markshuttle/dogfence-pcb/ACCEPTANCE.md

# Prototype and Field Acceptance

**Draft revision: 1.2.1-dev. Test requirements, not test results or release approval.**

This protocol separates basic acceptance of **five fully assembled prototypes** from qualification of the **41-station, 0-4000 m installation with 82 APEM indicators**. There are 40 spans, five earth-connected stations and 36 standard stations. Five basic bench passes do not authorize a perimeter production order, prove a board surge rating, or release the fence for animal containment.

[Agreed requirements](REMEDIATION.md#agreed-requirements) and [release gates](REMEDIATION.md#release-gates) control this protocol. Test the [reviewed prototype population](pcb/ASSEMBLY.md#reviewed-components) against the [BOM](pcb/BOM.csv). **C4, C5, W3, W1 and W4 remain open** for transient response, powered recovery, continuous thermal behavior and supplier process/fit acceptance; the [issue register](REMEDIATION.md#issue-register) owns their disposition.

Use [INSTALL.md](INSTALL.md) for isolation, wiring and operation, [RISKS.md](RISKS.md) for fault/environmental limitations and [ELECTRICAL](pcb/ELECTRICAL.md) for the circuit evidence. All steps below require recorded evidence; an unperformed or inconclusive test is **NOT RUN / HELD**, not PASS.

Purchases and allocation, including [resistor procurement/history](MATERIALS.md#resistor-procurement-and-history), belong to [MATERIALS](MATERIALS.md); manufacturer sources and unresolved product/process discrepancies belong to [ENVIRONMENT_EVIDENCE](pcb/ENVIRONMENT_EVIDENCE.md).

## Release Boundaries

| Gate | Evidence needed before release | Status in this draft |
| :--- | :--- | :--- |
| **P: File-verified prototype artifacts** | Strict file/artifact and sourcing checks; matching `status=prototype`, `mode=prototype` manifest and hashes; all five ledger holds explicitly deferred, not closed. | **Authorized artifact scope only.** Require current source-matched results in REMEDIATION; this protocol implies no fresh publication or upload/order authorization. Supplier CAM/placement/allocated parts are still required before an actual order. |
| **A: Production file ready** | Original engineering/file-release review: correct hub/circuit design; consistent source, libraries, rules and revision; passing checks; reviewed data and synchronized documentation. | **Held by unresolved protection, continuous-duty and part/land-pattern acceptance**, even when automated file checks pass. Not closed by P. See `pcb/verification.json`. |
| **B: Original prototype-order gate** | Original Gate A plus exact part/fit, placement, GDT forming, solder/via process and CAM acceptance, and an approved, safely bounded test programme. Known manufacturing defects cannot be deferred silently. | **Held wherever supplier/process evidence or controlled scope is missing.** Prototype-dependent tests may be explicitly deferred, not passed; P alone does not close B or authorize an order. |
| **C: Field release** | Required normal, selected negative-voltage protection, duty/thermal, visibility, full-hub, RF/site, fault/surge and material evidence; accepted earthing and maintained cattle-fence prohibition; documented performance limits. | **Held pending genuine qualification.** Excluded installation-polarity immunity is not a test PASS. |

The live checklist, not this table, records subsequent evidence-backed closures. **P is separate from the original A/B/C production/field holds.** Switch/environmental qualification and enclosure dry-fit on received boards are not prerequisites to prototype-file generation. Board-specific MPN/fit, GDT forming, panel/process, supplier CAM/placement and allocation remain order tasks; whole-BOM `allocation_verified` remains `false`. `1.2.1-dev` identifies a draft target; record actual board markings and hashes rather than relabelling older hardware as tested.

**TE prototype results do not qualify Yageo production.** Before production release, separately review the Yageo part's manufacturer/rating, land-pattern, thermal, pulse and process evidence, update the controlled BOM/CAD, libraries, models and notes, and reverify under the [population/substitution controls](pcb/ASSEMBLY.md#reviewed-components). Define the production configuration's required qualification and retained evidence explicitly; an order does not implement or approve a BOM variant.

## Preconditions

Apply these to the corresponding **hardware test**, not Gate P artifact generation. Switch/field approval is needed for hub/site tests and OneGel acceptance for potting, not for unpowered incoming-board inspection. An isolated board bench test still needs its own approved electrical bounds and stop limits.

1. Freeze the intended test configuration, including the revisions of this protocol and its referenced limits/tables. Record board serial numbers, source revision, schematic/BOM, as-built deviations, native placement/assembly drawing, fabrication manifest and report hashes. The population comes from the final BOM, not the legacy component count. **1.2.1-dev is retained for the approved 2 mm east board extension and H2/H4 moves after the westward GDT/via relocation.** Keep the pre-extension `1.2.1-dev` and earlier axial-AC / SMT AC/rear-B `1.2.0-dev` snapshots' hashes and sample histories separate, without transferring test results to the new outline/mount configuration. Approve substitutions and rework explicitly; no field soldering is part of the installation plan.
2. Have the electrical reviewer supply **numerical acceptance bands before testing**: source minimum/nominal/maximum including accessible adjustment, tolerance and overshoot; verified cable resistance/temperature range; per-channel current and branch loading; LED forward/reverse limits; power/temperature derating and stop limits; protection trip/recovery behavior; and the intended surge/insulation test envelope. Missing bounds hold the corresponding test. Do not choose limits after seeing the result.
3. Use **one MEAN WELL LRS-75-36 (36 V / 2.1 A / 75.6 W) for TEST; keep the second disconnected as a spare**. Verify receipt/nameplates and the TEST unit's qualified setting; no parallel, series, separate-channel or opposite-end feeding. Qualify the actual supply's hiccup/retry behavior with the actual **Littelfuse 0217002.MXP (2 A, 217 series)** and **Phoenix Contact UK 5-HESILED 60 / 3004139** holder and any revised source protection. Published DC interrupting capability is not clearing coordination.
4. Confirm the exact six-end switch program and source-side wiring. **Kraus & Naimer CA10.A364** is provisional; current **WAA364 (formerly A364) is eight-pole, 1-0-2 centre-off, 60-degree switching, not six-pole**. The six-end matrix is unchanged; **two extra poles remain unassigned**. The [catalogue contact/link schedule](pcb/ENVIRONMENT_EVIDENCE.md#catalogue-contact-schedule) is verified static source evidence, not the supplied-switch pinout. Obtain manufacturer approval of the exact offered contact development, DC breaking suitability and **global break-before-make** sequence across the entire used program, in both directions. A 20 A thermal rating or a static continuity test cannot supply this evidence. Assign physical terminal numbers only in the subsequently accepted hardware drawing.
5. Establish an authorized test area, independent animal containment, emergency shutdown, personnel responsibility and safe source isolation. OFF/TEST disable the RF fence. Follow [INSTALL.md](INSTALL.md#safety-first): isolate transmitter/PSU/backups, discharge and verify de-energization before handling terminals, then disconnect all six field ends. Inspect the **entire 4 km boundary cable, stations and hub** against the [energized-cattle-fence prohibition](INSTALL.md#cattle-fence-prohibition); record compliance and any required reassessment. If the hazard is found, stop work/use, arrange safe isolation and reassess before proceeding. Do not work during storms. Mains/PE and any surge testing require the relevant qualified personnel.
6. Obtain the supplied-revision APEM, COMBI 308 PP/TPE, Essentra, confirmed AMC cable and WISKA OneGel documents and define the material/fit process after manufacturer-conflict clarification. Do not pot the reference sample. Do not deliberately reverse LED flying leads to prove the excluded immunity requirement, or surge-test an assembly as an ordinary bench check; abnormal-voltage work requires a controlled test plan.

The [declared source-envelope study](pcb/DESIGN_BOUNDS.md#evidence-and-inputs) and [electrical load cases](pcb/ELECTRICAL.md#2-calculated-results) are analysis inputs, **not pre-approved test bands or enforced hardware limits**. Establish actual adjustment, tolerance, ripple/startup and hub/interface losses; PSU OVP is not a precision operating limiter. The historical restricted-voltage proposal was never enforced. Qualifying the actual normal source range is an alternative to requiring an active cutoff.

## Sample Allocation

All five units receive the workmanship, cold-circuit and normal-function checks below. The allocation is **proposed scope, not accomplished coverage**; record changes and sample history before each qualification test.

| Unit | Proposed additional use | Restriction |
| :--- | :--- | :--- |
| Board 1 | **Unpotted reference** with approved parts, measurements and photographs. | Retain unpotted; no intentional fault, reversal-stress, environmental or destructive surge programme. |
| Board 2 | Instrumented selected negative-voltage protection and unpotted electrical characterization; support nondestructive hub testing. | No required reversed-flying-lead survival test after the user's installation-risk acceptance. Approve the actual clamp/exposure test scope first and record stress/degradation before reuse. |
| Board 3 | Complete enclosure dry-fit/process qualification, then potted **0 m/source-end** continuous-duty thermal testing. | Fit actual WAGOs, cables, glands, earth conductors and lid indicators; instrument before filling. |
| Board 4 | Complete enclosure dry-fit/process qualification, then potted **4000 m/far-end** duty, visibility and environmental/site work. | Include reduced-voltage conditions and real viewing angles; reuse only if prior tests leave the unit suitable. |
| Board 5 | Full-hub/RF work and controlled source-fault/protection development; potentially destructive tests only when approved. | One unit cannot establish every surge, fault and environmental corner. Record stress order and preserve evidence. |

Five boards are not a 41-station fixture and do not provide independent replicates for every test. Review the required fault/surge polarities, levels, repetitions and destructive sample count with the test laboratory. **Request approval for more boards, indicators and fixture materials when the scope needs them**, rather than sacrificing the reference or inventing five-board coverage. Required deployment quantities and historic purchases remain distinct in [MATERIALS.md](MATERIALS.md).

## Instruments and Evidence

Use calibrated instruments suited to the circuit, location and energy involved. The following are acquisition requirements for the low-voltage programme, not claims about an available meter. Tighten them where the final design's margin requires it; record instrument model/serial, calibration, range, resolution, accuracy specification, offsets and probe loading.

| Measurement | Required capability / method |
| :--- | :--- |
| Steady DC voltage | At least a **0-60 V DC** measurement range covering the verified supply maximum, with appropriate overload/transient and common-mode ratings. Target expanded uncertainty no worse than **0.5% of reading + 0.05 V** for source/rail readings. Resolve the actual LED terminal voltage with **0.05 V or better uncertainty**, or tighter if needed for the 5 V limit. |
| Normal current | Suitable ranges for roughly **0-50 mA per indicator** and **0-3 A source current**, enlarged if the approved source can exceed these ranges. Target uncertainty **1% of reading or better** at each operating point, including offsets and shunt tolerance. Use calibrated low-burden shunts or properly fused current inputs; connect in series while unpowered, never place a current input across a supply. Fault/pulse ranges need separate sizing. |
| Resistance | Low-ohm/Kelvin measurement for PCB bonds, typically **0-1 ohm with at most 0.02 ohm uncertainty**; **0-100 ohms with at most 0.2 ohm uncertainty** for a core baseline; and a suitable resistor range with **0.25% or better uncertainty** for a 1% resistor. Lead/contact compensation is required. A beeper is a connectivity screen, not a precision bond measurement. |
| Leakage / high resistance | Record the meter's actual range, test voltage, input impedance and detection limit. Use a suitably sensitive guarded measurement if a sub-microampere bound is required. **A 0.00 mA display is not proof of zero or sub-microampere leakage**, and `OL` means beyond that instrument's range under those conditions, not infinity. |
| Temperature | Calibrated attached thermocouples/RTDs and an electrically suitable logger, covering at least **-20 to +125 degrees C**, with **2 degrees C or better uncertainty** including attachment effects; tighten for small margins. Measure ambient, internal gel/air and critical parts. Use appropriately isolated sensors. Do not infer part temperature by touching it; uncorrected IR readings on shiny parts are not sufficient. |
| Waveforms / timing | Appropriately rated **differential or isolated** voltage and current acquisition. Select probe bandwidth and sampling to resolve the fastest relevant edge, with at least ten samples across it and a justified probe rise-time/loading budget. Capture peaks, switching transitions, RF, start-up and full PSU hiccup/retry cycles, not just a DMM average. Record trigger, bandwidth, sample rate, time span, clipping checks and raw data. |
| Mechanical / optical | Calipers/gauges adequate for drawing tolerances, a calibrated low-range torque tool for the LED nut, and a measured **5 m** viewing distance. Record actual daylight illuminance, weather, background, sun direction, lens orientation and observer angles; use a light meter with documented range/accuracy suitable for full sun. Photographs alone do not establish ON/OFF visibility. |

These low-voltage ranges **do not authorize high-voltage field or surge measurements**. The qualified lab must select probes, isolation, differential/common-mode voltage, impulse energy and measurement-category ratings for the actual test. Never lift a scope's protective earth or improvise with a grounded scope clip on a floating field core. A mains isolation transformer is not a substitute for rated differential measurement. Keep required source chassis PE intact. Probe resistance/capacitance can alter LED reverse-voltage sharing; include that loading in the method and uncertainty.

Document an expanded uncertainty `U` with its confidence/coverage factor and the complete measurement chain. Apply guard bands: for an upper limit require `measured maximum + U <= limit`; for a lower limit require `measured minimum - U >= limit`. Include component/environmental corner allowances from the analysis separately. Resolution is not accuracy. If uncertainty or uncaptured transients could conceal a violation, mark **HELD**, not PASS.

## All-Five Workmanship

**Incoming fit evidence precedes assembly.** [ASSEMBLY's adopted hole/pin limits](pcb/ASSEMBLY.md#hole-fit-evidence) and [DFM evidence](pcb/DFM_EVIDENCE.md#independent-acceptance) distinguish published maxima from controlled **E procurement envelopes** and historical parts. Independently inspect **every allocated controlled-envelope part, including attrition**, with uncertainty. Verify the separate **0.050 mm radial per-pin pattern limit after common rigid alignment through the insertion length**; together with **+/-0.05 mm hole position on each axis**, it allocates **0.241421 mm diametrally in addition to the 0.10 mm assembly allowance** for retained Kefa/earth-GDT holes. R1/R2, D1-D4 and all three inter-core GDTs are SMT, with no insertion holes or axial resistor/AC forming/standoff. No allocated lot, earth-GDT forming process or insertion yield is approved by these calculations.

Perform and record these checks on **each** unpowered prototype before stress testing:

1. Match markings, references, MPNs, values, population and orientation to the accepted [BOM](pcb/BOM.csv) and [reviewed components/drawing](pcb/ASSEMBLY.md#reviewed-components). The design specifies **16 electrical parts, nine SMT and seven THT**, plus four mounting footprints. Verify both prototype R1/R2 are the selected TE part and all three inter-core GDTs, including GDT_AC, are the selected Ruilon SMT part, not production or retired-part substitutions. Require incoming-lot and PCBA-job allocation evidence, not just a matching sourcing code. No assumed approval of alternative indicators or historical active candidates.
2. Verify the **65 x 56 mm** outline and agreed fabrication tolerances, clean depanelized edges, and four **3.2 mm NPTH** mounting holes at the [controlled positions and mechanical clearances](pcb/ASSEMBLY.md#physical-guardrails). Rails/tooling removal follows the accepted manufacturer's plan; do not assume automatic removal or impose an unquoted outline tolerance.
3. Verify the required two exterior **2 oz / 0.070 mm** copper layers and
   [layer-specific protected geometry](pcb/ASSEMBLY.md#physical-guardrails)
   through manufacturing evidence and inspection: **3.20 mm A/C main rails on
   both faces, exactly 6.00 mm nominal rear B main width**, the **3.20 mm front-B
   main track with its approved stop**, the rear-return move and intact EARTH
   copper. Compare source/native and processed geometry with
   the controlled drawing and agreed fabrication tolerances; 6.40 mm is not the
   selected rear-B width. Require **>=3.00 mm different-core A/B/C copper
   separation on B.Cu only**, and **>=3.00 mm fence-to-EARTH separation on both
   faces**, applying `measured minimum - U >= limit`. Record the locations,
   measurements, uncertainty and manufacturing evidence; nominal source minima
   of **3.02 mm rear inter-core / 3.25 mm EARTH** are not finished-board guarantees.
   Preserve all nine rail and five earth stitching vias at the
   [controlled positions](pcb/ASSEMBLY.md#stitching-via-identification) and
   **1.00 mm nominal drill / 1.80 mm copper**. Vias are standard **UNTENTED on
   both sides: nominal 1.80 mm F.Mask/B.Mask openings, no via paste and no
   fill/plug/cap**. Adjacent same-net rail-via mask openings intentionally overlap;
   no SMT mask/paste aperture may overlap a protected via hole or annulus.
   Inspect processed drills/openings and actual solder ingress, drain-through,
   beads and cleanliness. Neither untented ENIG nor gel seals a via, and
   surface-copper weight is not barrel-plating thickness.
4. Compare the adopted [component-hole schedule](pcb/ASSEMBLY.md#hole-fit-evidence), pin/body/pattern limits and incoming reports with actual finished holes, annular rings and courtyards. Only retained connector/earth-GDT insertion holes remain; verify no resistor, diode or former GDT_AC holes. Require actual free insertion, accepted seating/earth-GDT forming and solder fill; nominal hole size alone is not lot-fit approval. Do not ream a plated hole, force a component or shrink a courtyard to hide interference. Resolve defects through the assembler/design owner.
5. In the controlled board view, verify `J_IN` opens left, `J_EARTH` right, `J_LED_A` north and `J_LED_C` south. Verify both LED connectors place the anode `+` left and cathode `-` right. D1/D2 cathodes face right toward LED positive; D3/D4 are rotated 180 degrees with **cathodes left to LED positive and anodes right to B**. Check actual nets and assembly drawing, not only the local `BYG23T_SMA_K_Right` name. D3/D4 are shunts after D1/D2, not additional series parts.
6. Inspect all three SMT inter-core GDTs against the accepted
   [placement/body/seating controls](pcb/ASSEMBLY.md#placement-and-polarity),
   including electrodes and solder fillets. Require no unintended conductive
   bridge, loose solder/debris or contact between unlike nets; record photographs
   and seating/clearance observations before gel. **GDT_AC has no axial
   lead-forming, raised-air-gap or height-gauge requirement.** Its SMT seating and
   the through-board B crossing still need workmanship, cold and qualified
   insulation/transient checks, not acceptance from mask or gel alone. SMT
   resistor seating follows its accepted reflow process, not retired PR02 rules.
   Check the three axial earth GDTs at **9.00 mm centre pitch** against the
   controlled **8.21 mm body envelope and 0.10 mm per-side projected pose
   allowance**: the budgeted body gap is **0.59 mm**, not a 1.00 mm air-gap or
   impulse-insulation claim. Measure their actual formed pitch, body/lead
   projections, standoff and complete height against the accepted
   [earth-GDT forming drawing](pcb/ASSEMBLY.md#axial-forming-approval), with
   uncertainty; missing forming/process limits leave that check **HELD**.
   Record results and defects per board. Retiring AC's forming task does not
   close W5's remaining forming, support/enclosure or material/process holds.
   On both bare and assembled boards, verify **>=3.00 mm between unlike-net
   pads of different GDTs and between AC pads and front B copper**, including
   solder encroachment after assembly. Record minimum location, value and
   uncertainty; require `measured minimum - U >= 3.00 mm`. The **3.20 mm nominal
   source minimum** is not a finished-board guarantee. This does not impose 3 mm
   within one tube or between the same-net AB/BC B pads, nor qualify flashover
   withstand. Check J_IN seating/access at the **0.25 mm courtyard gap** and
   inspect solder/beads and cleanliness at vias under its conservative body
   projection; record hidden-inspection evidence or hold an inconclusive result.
7. Inspect SMT seating/wetting, THT joints, shorts, contamination, damaged parts and excessive lead protrusion to the **agreed workmanship class and edition** (for example IPC-A-610 Class 2 when specified in the order). Obtain appropriate assembler evidence for internal barrel fill or hidden defects; an exterior fillet alone does not establish internal fill. Record any inspection requiring additional samples rather than sectioning the reference.
8. Match processed mask/stencil data and actual SMT joints to the
   [Ruilon land/clearance controls](pcb/ASSEMBLY.md#smt-via-relocation) and
   [SMA/resistor assembly controls](pcb/ASSEMBLY.md#indicator-sma-and-resistor-assembly).
   The selected metric Ruilon pattern's contradictory inch entry and actual
   solder/profile acceptance remain **W1 at all three GDT positions**, not
   resolved by the drawing choice or use of the same part code. Inspect **six
   Ruilon, eight BYG23T and four resistor paste apertures**, including actual
   registration/solder allowances and separation from via holes/annuli. Verify
   the **2.80 mm nominal land/mask/paste inner gap** and distinct **1.80 mm
   connected-copper gap** beneath each SMT GDT against source and processed
   geometry; inspect actual underbody joints/cleanliness against the accepted
   process and record any hidden-inspection evidence needed. Obtain supplier
   placement/stencil/solder acceptance of the
   [retained alternative TE lands](pcb/ASSEMBLY.md#2512-smt-resistors) under
   **W4**; body containment is not a manufacturer-exact land match. Verify
   land/body/courtyard geometry and zero additional source mask/paste margins
   against the referenced drawings. These source-design counts/geometry are not
   native or processed-stencil acceptance. Preserve below-tube insulation space;
   a raw F.Paste export is not supplier approval.

## All-Five Cold Checks

Disconnect external LEDs/loads as the **final circuit's** cold-test procedure requires; unplug all sources. Added clamps and semiconductor branches can change inter-net readings. Do not reuse a blanket requirement that every A/B/C pair must read above 50 or 100 megohms.

- Check intended same-net continuity from each `J_IN` core to its branch/rail test points, and between the three `J_EARTH` positions. Include the rear B connection to GDT_B_E's input PTH and both LED returns after the front-B stop/return relocation. Use the final netlist and a documented low-ohm limit with the uncertainty above; record readings and investigate unexpected resistance or intermittency. A shared earth net is not an aggregate terminal-current rating.
- Screen unintended shorts and earth leakage in both meter polarities, recording test voltage, range, connected loads and expected semiconductor paths. Compare against the final schematic's predicted behavior. **A DMM-open GDT is not proof of sparkover, discharge capacity or recovery.** Do not use a megger through electronics.
- Check resistor values and diode orientation/forward behavior at the meter's actual test current and temperature. For prototype **TE 35212K2FT, 2.2 kohm / 1%**, nominal tolerance arithmetic is **2178-2222 ohms**, not an automatically valid 25 C incoming-test band. The model's 25 C reference is an engineering assumption, not a verified TE measurement condition. Establish applicable reference/test conditions and allowances for **+/-100 ppm/C**, solder/ageing drift, measurement guard bands and parallel paths before accepting an in-circuit reading; see [DESIGN_BOUNDS](pcb/DESIGN_BOUNDS.md#evidence-and-inputs). A diode's forward reading is test-current dependent, and reverse `OL` is not a rated-voltage test.
- For an optional installed-cable baseline, follow [INSTALL.md](INSTALL.md#optional-dmm-checks): disconnect all six ends from hub/PSU/transmitter/backups and measure each **Start-to-End core separately**. Do not use zero or the parallel-core resistance as the single-core target. Set limits from verified cable data and commissioning baselines; record the actual cable data, temperature and meter uncertainty, and separate electronics if they affect the diagnosis.

## All-Five Normal Function

Use two actual **APEM Q10F5SXXSG02E no-resistor indicators** per board. Verify lead polarity before power. The published family maximum is **20 mA forward and 5 V reverse**, subject to the exact part's temperature and pulse conditions. A raw indicator is not a regulated 2 V load.

1. On a guarded, isolated low-voltage bench fixture, connect labelled A and C to the approved TEST positive source and B to **DC negative, not an assumed earth ground**. Connect each LED anode/cathode to its channel's verified `+`/`-` terminals. Set current limiting from the approved per-board normal envelope and fault-stop plan, not an arbitrary 0.5-1 A limit for one board.
2. Energize under the approved procedure and capture start-up as well as steady values. Test at the approved minimum, nominal **36 V**, and maximum supply/local-voltage conditions, including **0 m/source-end and 4000 m/far-end** loading. Record each LED's current and voltage, resistor voltage/power, board input and source current. Derive LED current from resistor drop only if the final branch current balance permits it; protection/bleed current may make them different.
3. Compare results with the final tolerance-aware analysis. The [historical nominal forward-only comparisons](pcb/ELECTRICAL.md#2-calculated-results) are context, not acceptance bands for a modified circuit. Verify the source can supply the actual 41-station network, including any credible negligible-cable commissioning load, without overload cycling. An upgrade's normal capacity margin does not prove fault coordination.
4. Check both channels illuminate as specified. Capture peak LED current/reverse voltage as well as steady readings; apply uncertainty and the exact part's limits. A visual glow is not a current measurement. Normal operation must remain within limits throughout the approved temperature and source range.
5. With power removed between changes, disconnect local tap A, then C, then B independently and verify the final design's expected local responses: A off/C on, A on/C off, and both off respectively. Restore and retest normal function. These are **local branch checks**, not a substitute for the full-hub cut tests below.
6. Record initial measured temperatures and abnormal behavior, but do not call a short bench run a continuous-duty qualification. Quarantine a failing unit and record correction/retest before any later qualification use.

## Negative-Voltage Protection

**Scope revised by the user, 2026-09-07:** accidental low-voltage installation polarity errors may damage LEDs; replacement with installation spares is accepted. **Reversed flying-lead survival is no longer mandatory.** Record polarity checks and spare allocation rather than performing destructive reversal solely to prove an excluded immunity requirement. This is a risk acceptance, not a protection-test PASS.

For the implemented D3/D4 negative-voltage shunts, test only the **selected, stated protection scope** on the allocated instrumented unit with correctly oriented external LEDs, a reviewed current-limited fixture and stop limits. Include normal operation, relevant negative connector voltage, startup/turn-off and agreed transients. The former complete eight-case source/LED-reversal immunity matrix is not a required design exit. Change wiring only while isolated; do not prescribe darkness as proof of protection. **C4 remains held because ordinary transient response is not qualified, not because the shunts are absent from CAD.** BYG23T's **75 ns reverse recovery is not forward-clamp speed**; the [typical forward-recovery test](pcb/DESIGN_BOUNDS.md#fault-screen) is not proof of <=5 V at the LED. D3/D4 do not regulate positive voltage or forward pulse current.

Measure **at the physical LED**, accounting for probe loading, and capture reverse voltage, forward current, protection current/power and temperature. Respect the **5 V reverse / 20 mA forward** ratings in normal operation and establish acceptable response to the defined pulse exposure; absent pulse ratings are not proof that every brief excursion causes failure. Do not invent blanket surge immunity or silently waive ordinary/nearby-lightning damage. The cattle-fence exposure is excluded by the whole-boundary installation prohibition, not a pulse-test PASS. Stop at the pre-approved thresholds and retain failures. Any topology change must pass the full-hub observability tests.

## Full-Hub Cuts

Use the **actual approved hub**, including sources/protectors and independently accessible boundary ends. With **all sources and the field disconnected**, verify and record **every RUN/OFF/TEST state for each of the six ends** against [INSTALL's functional matrix](INSTALL.md#functional-matrix). Record the expectation revision with the accepted hub terminal drawing; the functional matrix is not physical terminal numbering.

TEST is **same-end Start A/C positive, Start B DC negative, all End A/B/C separately isolated**. OFF isolates all six ends individually. T1/T2 retain the required OEM protector connections. RUN and TEST ties are made only on the appropriate **source-side contacts**, never as permanent boundary-side straps. **No End A/C common, opposite-end B return or dual-B negative return is permitted in TEST.** Retain manufacturer/dynamic evidence of global break-before-make, source isolation and DC load breaking; static states alone do not prove them.

Build a reviewed **41-station** fixture with A, B and C modeled separately over all 40 spans, using actual assemblies or validated electrically equivalent indicator/protection modules. A plain resistor load that loses the final branch's directionality or protection leakage is not automatically equivalent. Validate cable resistance/tolerances and actual nonlinear branch behavior; request additional hardware if needed. A five-board chain or software-only test is not a full-hub hardware pass.

Run and record **all seven clean-cut combinations (A, B, C, A+B, A+C, B+C, A+B+C) at each of the 40 spans: 7 x 40 = 280 cases**, including **0-100 m and 3900-4000 m**. Compare every case with the revision-controlled [clean-cut indications](INSTALL.md#clean-cut-indications), with one clean cut site, otherwise healthy branches/GDTs and no additional inter-core shorts. Record the automated model/regression results and the full-fixture results separately.

Record **both LED states at all 41 stations for every case** and representative actual currents/voltages, not just a count of lit LEDs. The first applicable transition must identify the adjacent 100 m span. Exact broken-core classification is not required. Exercise representative multiple-site [repair/retest](INSTALL.md#repair-and-retest) sequences: isolate all sources and six ends, repair the first located span, restore TEST, and check all stations again to locate remaining faults, including the final span. The separate 0 m and 4000 m stations at the shed must not be joined accidentally in the fixture.

Include negative controls for an unintended field-side A/C tie and an extra End B negative connection, demonstrating that the procedure/model detects their masking effects; do not install these as operating options. Separately record local failed indicators/taps, inter-core shorts and mixed open/short cases. They are diagnostic limitations, not cases required to satisfy the clean-cut table. Perform live fault stress only under the later qualified fault plan. Finish by restoring the approved wiring and verifying **operator restoration of RUN** and receiver function; TEST/OFF require independent containment throughout.

## Enclosure and Materials

With the assembly unpowered and before potting, dry-fit the actual **COMBI 308, polypropylene (PP) with TPE gasket, not polycarbonate**, with board, four **Essentra LCBSBM-6-01A-RT** supports, three **WAGO 221-613s**, actual cables/glands, both lid LEDs, plugs/seals, earth conductors where applicable, and service tools. Test both standard and earth-connected configurations. Check each board's support interfaces; use the allocated full assemblies for documented enclosure/process qualification.

- Verify support hole and board-thickness tolerances against the exact Essentra drawing (listing nominally 3.18 mm hole, 1.57 mm panel and 9.53 mm spacing), retention without damage, accepted adhesive preparation/dwell on the actual PP substrate and long-term mechanical support. Gel is not assumed to replace failed adhesive or support locks.
- Measure the actual internal clearances, wire bends, screwdriver access and lid service slack against the [controlled body/pose envelopes](pcb/ASSEMBLY.md#body-and-courtyard-evidence). Include J_EARTH's unchanged body/pose envelope and full courtyard, now nominally inside the extended edge, under the [edge-clearance controls](pcb/ASSEMBLY.md#earth-terminal-edge-clearance). Before this fit check, obtain accepted routed-edge tolerances and numerical mechanical/tool-clearance limits; require `measured minimum - U >= accepted minimum` for each clearance. Stop and record interference or confirmed limit violations as **FAIL**; mark missing limits or inconclusive fit **HELD**. Nominal or conditional budgeted margins are not accepted supplier tolerances or measured fit. External box dimensions do not establish a universal wall-clearance margin. Close the lid fully without pressing on SMT bodies/joints, displacing axial earth GDTs, straining LED leads or trapping the gasket. Record actual edge, seating, body/lead and lid clearances with uncertainty, including solder seating height, and reinspect after closure/re-entry. No retired AC overpass-height gauge applies; earth-GDT forming and complete assembly fit remain required.
- Verify the exact APEM cutout, panel thickness, seal stack and tightening instructions. Published Q10 guidance is **0.20-0.25 Nm**, subject to **Q10F5SXXSG02E** confirmation; record the actual torque/instruction revision. Verify cable glands against measured jacket diameter and the accepted WISKA entry/sealing arrangement. Do not use green/yellow as an active core.
- Record the confirmed **AMC Oceanflex CM03/05.100** reel labels from MATERIALS and **red, black and PLAIN green** cores. AMC **2026 Update V.3** lists **3 x 2.5 mm^2, Class 5 tinned copper, 7.4 mm maximum OD, 60 V max DC, -30 to +70 degrees C** complete-cable service. Reconcile the [conditional standard-resistance ceiling and strand-construction discrepancy](pcb/DESIGN_BOUNDS.md#evidence-and-inputs) for the supplied lot; the screen is not measured reel resistance. Obtain separate weather/UV, wet-conduit and impulse evidence. The older core-only 105-degree reference is not a complete-cable rating.
- Retain the exact **WISKA OneGel, 10108963, single-component 300 ml cartridge; no mixing** technical/process and safety evidence. Obtain dated supplied-lot clarification of the conflicting cure/temperature fields, with batch/storage record, preparation, application conditions, coverage/fill/vent method and re-entry limits. Do not import MP0100 instructions, assume self-levelling pour behaviour or prescribe an unsupported cure time or volume. Verify compatibility with PP/TPE, exact supports/adhesive, LED seals/leads, WAGO 221-613 contacts/housings, cable, components and assembly residues. **No thermal conductivity is published in the reviewed OneGel sources**; do not substitute a generic silicone value.
- Record pre-/post-potting photographs, measured dispensed consumption/usable yield, coverage/void inspection and normal electrical results. Historical litre and per-box estimates in MATERIALS are not acceptance volumes. Define and perform the intended raised-installation rain/condensation/salt, thermal-cycle, cable-entry strain and service/resealing tests on the completed assembly. IP claims must be limited to an applicable tested configuration; constituent ratings and gel do not establish hermetic or IP68 performance. No continuous submersion or multi-decade life is qualified here.

## Continuous Duty

**Continuous-safe normal TEST** is required even though normal use is one to two hours. A timer is not the baseline safeguard. Qualify the potted, closed assembly under an approved worst-credible ambient and solar envelope, not just the observed outdoor **-10 to +30 degrees C** or a ten-minute unpotted bench test.

Exposed LED front faces and cool outside air do not establish internal resistor temperature. SMT terminations, solder lands and PCB copper may change heat rejection, but do not lower electrical loss or prove cooler operation. No closed OneGel thermal test has been performed. Qualifying the real normal supply range is an alternative to adding circuitry solely to enforce the historical restricted-voltage proposal.

Use [DESIGN_BOUNDS's nominal and upper TE-prototype thermal cases](pcb/DESIGN_BOUNDS.md#thermal-screens) with their declared resistance/source assumptions, not measured temperatures, retired PS12/PR02 calculations or unreviewed Yageo ratings. The model's reference/temperature inputs are engineering assumptions, not verified TE test conditions. Establish applicability of catalogue power/ambient derating from [TE's different reference mounting](pcb/DFM_EVIDENCE.md#te-rating-and-mounting-basis) before using it as acceptance evidence; unverified transfer is not demonstrated two-layer failure. A rating-only ambient ceiling is not an approved assembly stop limit. PR02 hot-spot, mounted thermal-resistance and axial-standoff data do not apply. Actual chip/termination/PCB and adjacent-material temperatures remain to establish for each accepted part/configuration.

| Case | Required coverage |
| :--- | :--- |
| **0 m / source end** | Highest accessible PSU adjustment plus tolerance/ripple/overshoot, low cable drop, resistor/LED tolerances that maximize dissipation, and the hottest credible solar-loaded enclosure. Include the real load on the source, not only an ideal bench PSU. |
| **4000 m / far end** | Final distributed-cable/load behavior at both the minimum-current/visibility corner and the maximum credible local heating corner, with the actual potted enclosure and solar exposure. Do not assume far-end and source-end boards have identical currents or temperatures. |
| Normal source capacity | Actual 41-station load and any credible negligible-cable staging configuration, maximum setting and temperature derating. Record source regulation, overload/hiccup absence in normal operation, and power balance against the final analysis. |

Attach calibrated sensors before potting to R1/R2 and any new dissipative protection parts, relevant terminals/cable, gel/interior and enclosure/ambient locations. Record supply and branch current/voltage alongside temperatures. Ensure sensors do not compromise insulation, sealing or heat flow without accounting for it. Use a controlled radiant/thermal setup or a justified measured outdoor solar case; brief cloud-cooled results do not bound direct-sun operation.

Run through at least the two-hour typical duty and continue to demonstrated steady state. As a protocol criterion, under stable imposed conditions require critical temperatures to change by less than **1 degree C over an hour**, then log another hour; justify logger stability and any alternative criterion before testing. If stability or the environmental envelope is not established, extend the test or hold it. This demonstrates a bounded steady-state condition, not indefinite lifetime.

Compare measured temperatures/powers plus uncertainty and corner allowances with **each actual component's applicable derating/mounting conditions**. Do not assume a package or OneGel thermal resistance. Establish chip/termination/pad/PCB, estimated-film and adjacent-material temperatures with both branches powered, including the defined output-short screen. The linked interface/film development targets are not measured results or new user-wide temperature requirements. Check the cable, LED, gel, support adhesive and seals as well as the resistor. Define stop thresholds before starting and stop for instability, smell, damage, abnormal source cycling or a limit violation. Abnormal fault/surge heating remains a separate qualification.

## Daylight Visibility

Test the actual **Q10F5SXXSG02E** units in the final lid/gel/installation geometry at **5 m in full daylight**. Drive at the **final minimum expected field LED current**, including supply minimum, cable resistance/temperature, LED/protection tolerances and actual branch loading. A nominal source-end current or a larger bezel is not a visibility qualification.

Use the [nonuniform high-drop/Rmax versus zero-drop/Rmin comparisons](pcb/DESIGN_BOUNDS.md#normal-current), including conditional clamp diversion, to inform the test envelope. Named corners and the loose comparison floor are **not exhaustive minima, measurements or guaranteed optical floors**. The high-drop and leakage assumptions are not full-temperature low-current manufacturer bounds. Uniform loads cannot set the acceptance current. Verify physical OFF-state glow as well: series-diode reverse leakage is not solved by the ideal one-way cut classifier.

Use real patrol heights/angles, sun directions and backgrounds, including sunlight directly colouring the OFF lens. Record measured current, illuminance, lens condition and geometry. Require the intended operator to distinguish ON/OFF correctly in repeated blinded state changes at every required viewing angle, including the A-off/C-on and A-on/C-off patterns; retain observations and failures. Qualify any shade, orientation or other optical improvement before raising current. LED/resistor substitutions require renewed electrical, thermal, fit and procurement approval.

## RF and Site

1. Use the actual transmitter, required OEM protectors, accepted regional PE/bonding and cable, intended station population, fence construction/height and test receiver. Obtain OEM acceptance of the nonstandard boundary configuration. Record the real carrier/output settings and safe measurements; do not assume a universal RF amplitude or perfect inter-core equality.
2. Compare an accepted reference configuration with the added circuit in **RUN**. Verify boundary detection, absence of unintended receiver activation, transmitter loop/alarm behavior, and absence of misleading indicator light. Check inter-core/common-mode behavior and any rectified/protection current with suitable isolated methods. Darkness is not proof of RF transparency.
3. Inspect and record compliance with the [prohibition on energized cattle fencing](INSTALL.md#cattle-fence-prohibition) near the **entire 4 km boundary cable, every station and the hub**, and maintain it in service. Do not perform energizer-on/off testing of the prohibited exposure. If land use changes or the hazard returns, record the reassessment before use. No numerical safe separation or zero induction/lightning claim follows; plastic conduit is not shielding.
4. Qualify enough repetitions and operating/environmental corners to support the declared scope; define the duration/count beforehand with the reviewer. Record any incomplete population or untested exposure and retain the corresponding release hold. A short pilot with five boards cannot silently stand in for the final RF network or an endurance claim.
5. Verify earthing/bonding and any required site measurements through the qualified installer. The proposed common local earth for the OEM protection and both shed-end boards must match actual building PE/electrodes. Do not introduce independent unbonded rods, direct core-earth connections, or an assumed DC-negative earth bond. Keep animals independently contained until the operator restores and verifies RUN.

## Qualified Fault Tests

**C5 remains held** until the final powered fault and surge behavior is demonstrated. Recovery is unresolved, not an observed latched failure; the modeled ignited-state paths do not predict extinction or non-extinction. D3/D4 do not change those upstream GDT paths. A suitably equipped, qualified reviewer/laboratory must approve the procedure, sample count, applied energy, instrumentation, barriers, shutdown and discharge arrangements. Do not create high-voltage impulses or ignite GDTs with ordinary bench/DMM/grounded-scope improvisations.

- Test the actual source, fuse/holder, switch/interface and final circuit at relevant minimum/maximum output, ambient and cable conditions. Include near/middle/far **A-B, B-C and A-C shorts**, resistive faults that can produce sustained heating below a fuse threshold, and earth faults with the actual floating/bonded return paths. Include appropriate failed-short/failed-open GDT and protection-device cases, and representative additional faults needed by the analysis.
- For the **2 A Littelfuse 217**, use the applicable published **DC interrupting** conditions and actual time-current/I^2t data. Verify clearing or controlled shutdown under the real source waveform; do not assign a pass because a calculated current is merely above 2 A. Cable resistance and PSU hiccup pulses can prevent prompt clearing. Include fuse-holder indication/leakage paths where relevant. An intact fuse is not proof of safety.
- Include GDT ignition followed by a **powered nominal 36 V source**. Approximately **10-15 V arc voltage** can allow DC follow current after sparkover; 36 V below the nominal 470 V firing level does not prove extinction. Capture ignition, arc/follow current, extinction or safe shutdown, and all source retry cycles. Do not substitute a glow-to-arc transition number for holding-current evidence.
- Define the line-to-line and line-to-earth surge waveforms, polarities, source impedances, levels and repetitions before testing the **complete intended discharge path**. Measure residual/overshoot voltage at the vulnerable LED branch, cable, board and hub/OEM interface, and current/temperature in the real GDT/terminal/copper/earth paths. Account for unequal firing, not guaranteed sharing. Component impulse-current figures do not establish an assembled board rating.
- Use exact-part resistor evidence for pulse acceptance. TE's family working/overload ceilings and catalogue working-voltage arithmetic are not a five-second or impulse test specification. The cited TE sheet does not establish the historical PS12 `2.5 * RCWV` / 5 s test; do not transfer PS one-pulse curves or TE prototype results to Yageo. The [TE rating/mounting evidence](pcb/DFM_EVIDENCE.md#te-rating-and-mounting-basis) and [thermal screens](pcb/DESIGN_BOUNDS.md#thermal-screens) control those evidence boundaries.
- Include actual cable/insulation and enclosure/material configurations in the
  applicable dielectric/transient tests, including the **front A/C to rear B
  crossing at GDT_AC through nominal 1.440 mm FR-4** and the actual surface/edge
  paths. That nominal core thickness is not a guaranteed finished dielectric
  minimum or qualified impulse withstand; neither solder mask nor gel supplies
  insulation approval. Define test connections/device states, waveforms,
  voltages, durations, polarities and leakage/breakdown limits before testing,
  so GDT conduction is not mistaken for an insulation result. Record as-built
  laminate/process evidence, post-assembly workmanship, raw measurements and
  pre-/post-exposure insulation and normal-function results. The cable's 60 V
  operating rating is not impulse qualification; neither is a GDT's nominal DC
  sparkover or a switch's insulation/thermal rating. Any destructive insulation
  testing must isolate unrelated electronics and use an approved laboratory
  method; this is not an ordinary bench/field megger check.
- Require the predeclared limits for touch/step hazards, temperature, current, residual voltage, insulation and physical damage to be met, with no uncontrolled arcing or persistent/repeating follow-current heating. After each exposure, verify the specified **powered recovery or safe shutdown**, inspect for latent open/short damage, and repeat normal, selected protection and diagnostic checks as appropriate. A DMM-open GDT must not be called a functioning arrester without the relevant post-stress characterization.

Record any required manual reset/replacement and safe inspection procedure. Recovery of the TEST source is not automatic return to RUN; containment restoration remains the operator's action. Qualifying a declared exposure does not establish direct-strike survival or an untested assembled surge-current/lifetime rating.

## Acceptance Record

For each unit, retain serial/revision, part and process identities, protocol/expectation revisions, test configuration and source settings, measured values with uncertainty, raw captures, photographs, test date/operator, defects, rework, repeat tests and disposition. Retain the unpotted reference and its baseline data. Use the table as an empty record, not a pre-issued certificate:

| Unit | Workmanship | Cold checks | Normal min/nominal/max | Allocated qualification evidence | Disposition |
| :--- | :--- | :--- | :--- | :--- | :--- |
| Board 1 | NOT RUN | NOT RUN | NOT RUN | Unpotted reference record pending | HELD |
| Board 2 | NOT RUN | NOT RUN | NOT RUN | Negative-voltage protection/characterization pending | HELD |
| Board 3 | NOT RUN | NOT RUN | NOT RUN | Source-end potted duty/process pending | HELD |
| Board 4 | NOT RUN | NOT RUN | NOT RUN | Far-end duty/visibility/material/site pending | HELD |
| Board 5 | NOT RUN | NOT RUN | NOT RUN | Hub/fault/protection scope and evidence pending | HELD |

Maintain separate evidence reports for the **280 full-hub cut cases**, selected negative-voltage protection, thermal corners, visibility, enclosure/material process, RF/site (including cattle-prohibition compliance/reassessment) and qualified powered fault/surge recovery. Identify sample reuse and gaps explicitly. The engineering reviewer records evidence-backed gate or issue closure in [REMEDIATION.md](REMEDIATION.md); these documents neither authorize an order nor close C4/C5/W3/W1/W4. Resolve the existing sample, supplier, installer or laboratory requirements before requesting the applicable release.
