markshuttle/dogfence-pcb/REVIEW.md

# Reusable Engineering Audit Brief

**This is a review prompt/template, not a completed audit, order specification override, or release sign-off.** The issue/evidence record and gate decisions are in [REMEDIATION.md](REMEDIATION.md). Draft hardware revision is **1.2.1-dev**, with **1.1.0** the reviewed baseline; determine what is actually implemented from the current sources and reports.

## Scope

Act as a hardware, PCB DFM and procurement reviewer. Read REMEDIATION and [AGENTS.md](AGENTS.md), then the current schematic/PCB, project/rule/library files, reviewed sourcing, build implementation and associated documentation. Include [pcb/ELECTRICAL.md](pcb/ELECTRICAL.md), [pcb/ASSEMBLY.md](pcb/ASSEMBLY.md) and [pcb/DFM_EVIDENCE.md](pcb/DFM_EVIDENCE.md): they distinguish adopted file limits and visually resolved drawings from still-unperformed lot/process acceptance. Missing acceptance is a hold for its relevant order/qualification scope, not permission to assume it exists.

For a **board/prototype-only audit**, prioritize P3/P4 and **Gate P file-verified prototype artifacts**, separate from the original A/B/C production/field holds. Preserve switch/environmental qualification without restarting that research; enclosure dry-fit follows prototype receipt, not file generation. Supplier CAM/placement/allocated parts, SMT seating and earth-GDT fit/forming/panel/process acceptance remain explicit order tasks. No upload or order is authorized.

Use [pcb/ENVIRONMENT_EVIDENCE.md](pcb/ENVIRONMENT_EVIDENCE.md) for manufacturer sources and detailed unresolved discrepancies, and [MATERIALS.md](MATERIALS.md) for the latest user-confirmed inventory, reel labels and PSU allocation.

Perform a **read-only audit of design/source files** unless changes are separately requested. Use headless tools and build-owned, non-hidden project-local staging; preserve unrelated work and audit evidence. Reports/generated test outputs do not authorize source edits, commits, uploads, part purchases or fabrication. Record the exact revision/hashes and tool versions reviewed; old successful reports are historical evidence only.

## Agreed Baseline

| Area | Audit against this requirement, not a forced upgrade |
| :--- | :--- |
| Prototype | **Five individual fully assembled JLCPCB boards**, including all SMT/THT work and controlled earth-GDT forming; **no field soldering**. |
| Fabrication | Available JLCPCB standard **FR-4, two layers, 2 oz copper on both F.Cu/B.Cu, ENIG, nominal 1.6 mm finished thickness, green mask quote default**. Selected vias are **UNTENTED both sides, no fill/plug/cap**. This is not a special-stackup/filling request or evidence of special CAM approval. Do not impose High-Tg 170, 2-microinch gold or other process changes without approved need and supplier acceptance. |
| Deployment | **41 stations at 0, 100, ..., 4000 m**, including separate shed-end boards: **36 standard + 5 earth-connected**, **82 LEDs, 164 supports, 123 WAGO 221-613 splices**. Reconcile boxes/glands/prototype/spare allocation separately. |
| Purchases | Reconcile orders, cancellations, receipts and allocations against [MATERIALS](MATERIALS.md), including [resistor procurement/history](MATERIALS.md#resistor-procurement-and-history) and the [GDT quantity change](MATERIALS.md#gdt-procurement-and-history). Preserve historical records and current dispositions separately; removed Bencent positions are not a cancelled purchase, and extra fitted Ruilon requirements are not allocated stock. Do not transfer quantities between parts or invent purchases. Check field shortfalls before additional samples/spares, and retain the old switch's unapproved purchase history. |
| TEST | Nominal 36 V, same-end feed/return, typically one to two hours but **continuous-safe normal TEST** required. No direction selector, automatic core classification or timer-based safety requirement. |
| Fault requirement | Localize one site affecting any one, two or all three cores to a 100 m span. Repair first fault and repeat for multiple sites; no promise of identical behavior with mixed open/short faults. |
| Indicators | Purchased **APEM Q10F5SXXSG02E**, no internal resistor, 20 mA family maximum, 5 V reverse maximum. ON/OFF distinguishable at **5 m in full daylight at minimum field current and actual angles**. Q14 and README alternatives are unapproved. |
| Accepted damage / design scope | LED damage from accidental low-voltage installation polarity errors is accepted, with spares still to allocate; reversed flying-lead survival is no longer required. Direct-strike rebuilding is accepted, not all ordinary/nearby transient damage. Continuous-safe normal TEST remains hard. Review the authorized **16-part 2512 SMT/BYG23T hybrid** in ELECTRICAL section 9, not a mandatory historical 40-part circuit. |
| TEST source | **One MEAN WELL LRS-75-36 for TEST; second a disconnected spare** under [INSTALL's source controls](INSTALL.md#switch-and-supply). No parallel, series, separate-channel or opposite-end feeding. Verify received units/settings; source capacity is not a fault fix. |
| Switch candidate | **Kraus & Naimer CA10.A364**, provisional; current **WAA364 (formerly A364), eight-pole, 1-0-2, 60 degrees**, not six-pole. Exact physical numbering, DC/contact/global-transfer approval remain open. Six-end matrix unchanged; **two extra poles unassigned**. |
| Site | Coastal Isle of Man, observed -10 to +30 degrees C with some direct sun, not guaranteed extremes/internal limits. [Energized cattle fencing is prohibited](INSTALL.md#cattle-fence-prohibition) near the **whole 4 km boundary cable, every station and the hub**. Inspect and maintain the prohibition, not the withdrawn exposure test; reassess before use if the hazard returns. No safe-distance or zero induction/lightning claim. |
| Cable | User-confirmed **AMC Oceanflex CM03/05.100** reel labels and **red, black and PLAIN green** cores. Audit supplied manufacturing-revision and conditional standard-resistance applicability against the [AMC 2026 Update V.3 evidence](pcb/ENVIRONMENT_EVIDENCE.md#amc-oceanflex-cable). UV/weather, wet-conduit and impulse evidence remain open, not product identity or colours. Core-only 105-degree data is not a complete-cable rating. |
| Enclosure and gel | **COMBI 308 is PP with TPE gasket, not polycarbonate**. Confirmed **WISKA OneGel, not MP0100: single-component cartridge, no mixing**. [Manufacturer cure/temperature conflicts](pcb/ENVIRONMENT_EVIDENCE.md#wiska-onegel) require clarification; no thermal conductivity is published in the reviewed sources. Audit consumption/yield against the accepted process, not historical purchase estimates. |

## 1. Electrical And Hub Review

- Verify every RUN/OFF/TEST state for all six independent ends against [INSTALL's functional matrix](INSTALL.md#functional-matrix). **TEST Start A/C -> positive, Start B -> DC negative, End A/B/C independently isolated**; OFF isolates all six individually. Required ties must be source-side contacts, not permanent field straps. Reject opposite-end B return, both-B negative ties or an End A/C common that masks a cut. Check transfer globally across all switch poles, not just individual break-before-make claims.
- Preserve the WAGO through-splice/PCB-tap architecture. Model actual cable-end connections and local board currents; do not route the full perimeter current through every PCB in the calculation. Confirm transmitter/DC separation, OFF limitations, fence-inactive indication and independent containment in TEST/OFF.
- Reproduce the four **historical ideal-36 V, forward-only comparisons** in [ELECTRICAL's calculated results](pcb/ELECTRICAL.md#2-calculated-results): distributed 41-board nominal, five zero-cable-resistance boards, all 41 zero-cable-resistance boards and the higher-resistance/higher-drop sensitivity. Record inputs, branch/source currents and power against the named cases; these are not current cable bounds, measurements or visibility proof.
- Review the [declared source/cable/resistance envelope](pcb/DESIGN_BOUNDS.md#evidence-and-inputs): source screens are not enforced limits, and the historical restricted-voltage proposal was never implemented. Confirm the conditional standard-resistance basis and resolve the labelled-strand/standard construction discrepancy. Use the [TE-prototype nonuniform current cases and loose comparison floor](pcb/DESIGN_BOUNDS.md#normal-current), not retired PS12/PR02/MBE evidence or unreviewed Yageo extrapolations. High-drop and clamp-diversion assumptions are not exhaustive or measured minima or predicted brightness. Do not double-count diverted clamp current in source demand or add the disconnected spare's capacity; series-diode reverse leakage and OFF glow remain outside the ideal cut model.
- Test all seven cut-core combinations across the 40 spans, especially the first and 3900-4000 m spans, plus repair/retest sequences, power balance and negative controls for masking connections. Check observability again if protection changes make the rungs bidirectional; the old forward-only model cannot validate a different circuit.
- Review **C4 against its updated scope**, not mandatory survival of installation polarity mistakes. Verify D1-D4 BYG23T identities against the [BOM](pcb/BOM.csv). D1/D2 are series; D3/D4 are negative shunts after them, cathode to LED positive/anode to B. Verify actual connections, light/cut behavior and ordinary/transient response. **75 ns reverse recovery is not forward-clamp speed**; the [typical forward-recovery evidence](pcb/DESIGN_BOUNDS.md#fault-screen) does not prove <=5 V at the LED. The diode reverse rating and output shunts neither regulate forward pulse current nor protect reversed flying leads. Implementation is not qualification, and the historical active design is not a prerequisite.
- Keep **C5** open until the actual PSU/fuse/GDT system is analyzed and appropriately tested for hard/resistive shorts, ignited and failed GDTs, cable-limited current and powered recovery. Recovery is unresolved, **not an observed latched failure**; conditional arc load lines do not predict extinction/non-extinction. D3/D4 do not alter those upstream paths. Use actual DC interrupting/time-current and hiccup data. Do not infer fuse clearing from `>2 A`, extinction from 36 V being below sparkover, or equal transient sharing from parallel conductors.
- Check transient residual voltage, lead overshoot, RF loading and cable insulation limits. A 470 V DC sparkover rating is not a 470 V transient clamp; component 5/20 kA data does not rate the assembled board, and three parallel earth pins do not establish 72 A capability.
- Verify the [TE evidence correction](pcb/DFM_EVIDENCE.md#te-3521-prototype-selection) against **9-1773463-5, Rev G, 02/2025**, not the unsupported 03/2023 attribution for which no archived copy was found. Check that [model fields](pcb/DESIGN_BOUNDS.md#evidence-and-inputs) distinguish the supported manufacturer TCR magnitude from the assumed resistance reference and linear temperature screen. Do not transfer PS12 TCR test endpoints to TE or treat conditional power screens as measured temperatures.
- Bound continuous TEST temperatures using [thermal screens](pcb/DESIGN_BOUNDS.md#thermal-screens) and [actual mounting evidence](pcb/DFM_EVIDENCE.md#te-rating-and-mounting-basis). TE's four-layer reference differs from this two-layer PCB; catalogue power/derating transfer is conditional, not proof of two-layer failure. Verify actual chip/termination/pad/PCB and material-interface temperatures; PR02 hot-spot, mounted thermal-resistance and axial-standoff data do not apply. SMT changes heat flow, not nominal loss or proven OneGel temperature. W3 remains open, not a Gate P prerequisite; no timer, headline wattage or assumed conductivity closes it.
- Keep TE family voltage ceilings distinct from the power-limited catalogue working-voltage calculation under the [rating/mounting evidence](pcb/DFM_EVIDENCE.md#te-rating-and-mounting-basis). The cited TE sheet does not establish a `2.5 * RCWV` / 5 s overload test or the historical PS one-pulse curves. Require exact-part pulse evidence instead of renaming PS12 test conditions as TE data. No component ceiling is a system voltage or surge rating.

## 2. Project And Publication Verification

- Inspect the actual [Makefile](Makefile) and exercise the intended strict workflow: complete-project staging with schematic, PCB, project/rules and reproducible local libraries; headless DRC, ERC, schematic/PCB parity, protected geometry and artifact checking. Retain readable/machine-readable reports on success and failure. Block electrical/DFM errors and unreviewed design warnings rather than suppressing missing libraries or courtyards.
- Verify the resolved KiCad executable by invocation and version. Reviewed tool baseline is **9.0.7**, not untested KiCad 7/8 support. Use Snap-accessible project-local staging and ensure cleanup cannot delete unrelated `tmp/` evidence.
- Check that every public export/package target runs complete file/artifact checks. **`make gerbers` / `make prototype` may publish FILE-VERIFIED PROTOTYPE ONLY packages with all five C4/C5/W3/W1/W4 holds deferred, not closed**. `all`, `package`, `release`, `production`, `drills`, `ipc`, `bom`, `cpl`, `zip-gerbers` and `zip-flytest` retain production holds; production wins mixed goals in either order. `make check` never publishes. Explicit `External` metadata may pass file checks, but unresolved sourcing blocks **both** publication modes. No diagnostic or sourcing bypass, guessed code or automatic approval-hash refresh is allowed.
- With exclusive runtime ownership, use `verify_workflow.py --expect-holds C4 C5 W3 W1 W4` for the default production-refusal comparison and `--target prototype --expect-holds C4 C5 W3 W1 W4` for **real serial/parallel prototype publication**, including notices/manifests. Prototype refusal for unresolved sourcing is not a publication PASS. Preserve useful evidence before cleanup; failures must not leave stale packages presented as current.
- Compare complete schematic/PCB/IPC terminal membership with documented aliases, coordinates/units and rounding tolerance. Reject empty/unrecognized inputs. Verify the [expected file inventory](pcb/ASSEMBLY.md#reviewed-components) independently from native exports: nets, terminals/IPC records, component versus via drills, PTH/NPTH classification and mask/paste apertures. Expected counts are not a current native result. Check actual geometry, layers, BOM/CPL completeness, ZIP contents and hashes; use REMEDIATION for the latest revision-specific results.
- Inspect `build/manifest.json` revision, tool, results and matching source/artifact hashes: **`status=prototype`, `mode=prototype`**, or production **`status=verified`, `mode=build`**. Status alone is insufficient. Verify source/visible board/schematic/docs revisions match and generated `README.txt` carries mode/open-hold notices inside both Gerbers/FlyTest ZIPs. Both modes use the same public filenames and `pcb/Gerbers.zip` mirror; filenames do not identify the approved scope or authorize upload/order.

## 3. Fabrication And Physical Fit

- Apply [README's via and component hole DFM policy](README.md#via-and-component-hole-dfm) using current order-specific manufacturer data. Check applicable two-layer/2 oz rules, including at least 0.1651 mm track width, the project's 0.20 mm general copper clearance and **0.254 mm nominal component PTH ring**, plus hole/edge rules. Distinguish manufacturer minima, conservative project rules and generic via-ring limits.
- Verify all [physical guardrails](pcb/ASSEMBLY.md#physical-guardrails) against source/native geometry: **65 x 56 mm outline and east-shifted H2/H4 mounts**, all mounting holes/keepouts, **3.20 mm A/C main rails on both faces**, **exactly 6.00 mm rear B main width, not 6.40**, approved front-B stop/rear-return move, matching EARTH bus, all fourteen stitching vias, LED connector polarity/outward orientations and earth-GDT pitch. Check **>=3.00 mm different-core A/B/C copper clearance on B.Cu only** with both native and independent guards, separately from fence/EARTH clearance on both faces. Do not impose that inter-core rule on F.Cu's reviewed SMT gaps or claim all A/B/C rails are 3.20 mm on both faces. No folded takeoff or extra via is authorized. Measure actual geometry rather than assuming nominal gaps are tolerance-free; no further unapproved guardrail change is permitted.
- Verify D1-D4's [SMA land/mask/paste geometry](pcb/ASSEMBLY.md#indicator-sma-and-resistor-assembly) and [placement, pad nets and routing](pcb/ASSEMBLY.md#placement-and-polarity). D1/D2 cathodes face right; D3/D4 are rotated 180 degrees with cathodes left to LED positive and anodes right to B. Check straight cathode links and shunt anode-to-B routes to J_LED_A/C pin 2, actual stencil and supplier models, zero additional mask/paste margins and absence of diode PTHs. A footprint name alone is not global polarity evidence.
- Verify R1/R2 origins, rotations, pad centres, land/body/courtyard geometry and zero additional mask/paste margins against the [2512 SMT assembly controls](pcb/ASSEMBLY.md#2512-smt-resistors) and [placement table](pcb/ASSEMBLY.md#placement-and-polarity). The retained project lands differ from TE's recommendation; body containment is not exact land compatibility or 100% fit. Require supplier placement/stencil/solder acceptance of the alternative. No geometry change, resistor holes, axial standoff or forming is authorized by this evidence correction.
- Verify the adopted [component hole/pad and pin-envelope schedule](pcb/ASSEMBLY.md#hole-fit-evidence) against source/native drills. Distinguish the Kefa **E procurement envelopes** from guaranteed maxima and the earth-GDT drawing maximum; the Bencent AC selection/holes are retired. Require independent allocated-lot pin/body inspection with uncertainty, including attrition; no forced insertion, clipped pins or reamed plating.
- For the retained Kefa/earth-GDT holes, verify `nominal hole - 0.08 - pin envelope - 0.241421 >= 0.10 mm`, using rectangular diagonals. The extra position budget covers **+/-0.05 mm hole position per axis** plus an independently controlled **0.050 mm radial per-pin part-pattern limit after common rigid alignment through the full insertion depth**. Do not spend the 0.10 assembly allowance twice or call larger holes solder-fill/lot-fit proof. **W4 remains held.**
- Verify all fourteen vias against the [coordinate/function schedule](pcb/ASSEMBLY.md#stitching-via-identification): **UNTENTED both sides, no via paste, no fill/plug/cap**, with protected drills/copper/positions and specified F.Mask/B.Mask openings. Adjacent same-net rail-via mask openings intentionally overlap; this is not a blanket permission for an SMT mask/paste aperture over a via hole or annulus. Obtain coordinate-specific drill-preservation CAM evidence and inspect solder ingress, beads and cleanliness; ordinary via processing does not guarantee a finished 1.00 mm tolerance or a seal. Resistor and AC insertion holes are removed; identify every retained hole by function, not diameter.
- Verify the [selected metric Ruilon lands and clearance proof](pcb/ASSEMBLY.md#smt-via-relocation) against actual exports/processed data for **all six lands across GDT_AB, GDT_BC and GDT_AC**. The contradictory inch entry and actual solder/stencil/CAM acceptance remain **W1 at all three positions**; figure association is resolved, not manufacturer correction. Recheck full drill-circle/annulus distances with registration and solder allowances, including every GDT, BYG23T and resistor aperture. Preserve the distinct land/mask/paste gap versus connected-copper gap and full-width stub endpoints; reject aperture-over-hole regressions.
- Distinguish **70 micrometres exterior copper** from barrel thickness; a published 18-micrometre average is not a minimum for every barrel. Require accepted plating and solder processes where the electrical case depends on them. Do not add narrow thermal spokes to protected surge paths merely to simplify soldering.
- Verify all [maximum-body boxes and courtyards](pcb/ASSEMBLY.md#body-and-courtyard-evidence) against ASSEMBLY/DFM_EVIDENCE: original figures have been visually read and Kefa uses explicit E boxes, not unbounded nominal bodies. Apply the controlled 0.10 mm projected pose allowance, including tilt. Apply [J_EARTH's current edge-clearance controls](pcb/ASSEMBLY.md#earth-terminal-edge-clearance) to its unchanged body/pose envelope and full courtyard, now nominally inside the extended edge. Distinguish nominal and conditional budgeted margins from accepted routed-edge tolerances and measured fit. Require and record actual panel/depanelization, enclosure and wire/tool-access acceptance; hold missing or inconclusive evidence and do not trim envelopes or move protected earth copper to conceal interference. The 9.00 mm earth-GDT pitch yields a **0.59 mm budgeted body gap**, not 1.00 mm air-gap/impulse proof.
- Verify GDT_AC's [current placement](pcb/ASSEMBLY.md#placement-and-polarity): same Ruilon SMD5050-470NA identity and top-only metric footprint as GDT_AB/BC, approved westward origin, north A/south C pads, no retired Bencent local footprint or two AC insertion holes. Check the front-B stop and rear continuity to GDT_B_E's input PTH, relocated rail vias, and separate **>=3.00 mm unlike-net inter-GDT pad / AC-pad-to-front-B copper controls**. Do not extend those controls inside one GDT or infer physical fit from J_IN's **0.25 mm courtyard gap**; require seating/solder inspection at vias under its conservative projection. The crossing uses nominal **1.440 mm FR-4**, not the old raised air gap; nominal thickness, mask and gel do not qualify impulse insulation. No AC lead-forming or height-gauge requirement remains. Inspect actual SMT seating/fillets and require post-assembly insulation/transient evidence in its qualification scope. The three axial earth GDTs still need accepted [forming drawings](pcb/ASSEMBLY.md#axial-forming-approval), seal/bend/pattern/standoff/height and process inspection; **W5's other fit/material/process holds remain open**.
- Check nominal 1.6 mm finished thickness against stackup, fabrication tolerance and the actual Essentra supports. After prototype receipt, dry-fit COMBI 308, WAGO 221-613s, glands, cable bends, earth wires, lid LEDs and screwdriver/rework access; this is not a prerequisite to Gate P files. Correct APEM mounting torque is **0.20-0.25 Nm**, subject to exact model instructions.
- Check legend height/stroke and pad clearance, useful underside references and revision marking; a font setting does not prove printed minimum stroke. Review manufacturer-added rails, fiducials/tooling and depanelization without invading protected copper. Do not mandate a 73 x 76 mm panel or assume automatic rail removal.

There are no ICs, oscillators or high-speed digital interfaces in the implemented 16-part passive hybrid. Do not prescribe generic decoupling, oscillator guard rings or a blanket ground plane. Assess any further approved circuit additions on their own needs and RF/isolation effects.

## 4. Sourcing And Assembly Data

- Derive the actual population from the schematic/PCB and compare with the [reviewed component index](pcb/ASSEMBLY.md#reviewed-components): all required top-side SMT/THT parts and separate mechanical footprints, including series versus shunt diode roles. Retired parts are not defaults. Verify exact manufacturer, MPN, footprint and population against BOM and order without claiming assembled or native-verified counts from prose alone.
- Generate CPL natively for **all required SMT/THT**, excluding mechanical/DNP items. Retain native signed Y, common origin and correct handedness; do not use absolute Y values. Normalize rotations modulo 360, so -90 and 270 degrees agree. Confirm footprint origins versus physical assembly centroids and document only evidence-backed part/model corrections.
- Independently verify outward terminal openings, both LED connectors' left-positive/right-return pad mapping, **D1/D2 cathodes right, D3/D4 cathodes left**, and GDT_AC's north-south SMT geometry. Do not infer polarity/orientation from local footprint names or move PCB pads to repair an import error.
- Obtain dated quote-specific stock/allocation, attrition, packaging/minimum loading, Basic/Extended status, prices and schedule when supplier review is authorized. Verify both prototype R1/R2 identities and synchronized sourcing metadata against the [BOM](pcb/BOM.csv), including manufacturer `TE Connectivity`, `Sourcing=LCSC` and empty `Sourcing Reference`. A matching identity is not whole-BOM allocation: **`allocation_verified` remains `false`**. Unresolved external rows still block both publication modes; public stock is not allocated inventory. Preserve the linked procurement history without restoring retired procurement/forming tasks. Economic and Standard both permit THT in principle; verify this exact 2 oz/ENIG mixed assembly, heavy-copper soldering and earth-GDT forming job rather than imposing a universal service restriction.
- Audit the [Yageo production selection and its procurement record](MATERIALS.md#resistor-procurement-and-history), not an assumed receipt/allocation or implemented BOM variant. Do not invent manufacturer mounting/thermal/pulse claims from an identity listing. Before production release require separate exact-part review and controlled BOM/CAD, library, model and note updates, followed by reverification and applicable qualification. **TE prototype results do not qualify Yageo production.** Rejected-code history is not another purchase.
- Do not automatically substitute Q14 or README alternatives for stock issues. Require exact electrical, package/pin/body, RF, thermal/pulse, optical, process and procurement review. A larger bezel or higher headline rating is not evidence of system improvement.
- Separate **processed PCB/stencil CAM approval** from **parts-placement/assembly approval**, including panel/rails/fiducials, protected hole coordinates, accepted solder/forming process and delivery condition. A checkout checkbox or 3D preview does not prove both.
- Reconcile 41 field boxes/two cable entries each, additional earth/hub hardware and prototype/spare consumption against actual inventory. Preserve ORDERED/ON HAND history, especially the **2 LED / 4 support / 3 WAGO field shortfalls**; do not turn candidates or pending items into purchases. Historical **207-1331/207-1333** Gelbox suggestions belong to the **4 mm^2 connector series**, not a verified **221-613** match; do not promote them into approved alternatives.

## 5. Qualification And Reporting

Separate file verification, supplier acceptance and physical qualification. Review the actual scope/results under [ACCEPTANCE](ACCEPTANCE.md) for workmanship on all five prototypes, normal function, selected negative-voltage protection, continuous potted thermal soak, 5 m minimum-current daylight contrast, full-hub cut behavior, enclosure/material process, RF/site and qualified fault/surge recovery. Check predeclared limits, uncertainty, per-station records and separation of model results from full-fixture evidence. Do not reinstate the excluded reversed-flying-lead immunity test or call accepted installation damage an immunity PASS. Retain an unpotted reference; obtain approval for extra/destructive samples if needed. A DMM-open GDT, dark LED or displayed 0.00 mA is not proof of firing capability, safe reverse voltage or sub-microampere leakage.

Require supplied-reel manufacturing-revision and conditional standard-resistance applicability, plus UV/wet-conduit/impulse evidence, without reopening confirmed cable identity or colours. Require OneGel supplied-lot process clarification and compatibility with PP/TPE, exact Essentra supports/adhesive and WAGO 221-613s; no assumed mixing, self-levelling pour or curing step. Include credible coastal/solar conditions and actual RUN/TEST RF/site qualification. **Verify recorded inspection/compliance and ongoing maintenance of the whole-boundary cattle-fence prohibition, not energizer-on/off testing of the prohibited exposure**; changed land use or reintroduced exposure requires recorded reassessment before use. Verify the site-specific earthing/bonding design with regional OEM instructions and a qualified installer; do not prescribe arbitrary unbonded rods, direct fence-core earthing or a default DC-negative bond. Do not infer an assembled IP68/hermetic rating, direct-strike protection or multi-decade life from ENIG, gel or component data.

Report **findings first**, ordered by severity, with file/line or measured feature, reproducible evidence, consequence and a specific closure action. Distinguish a demonstrated defect from absent supplier/test evidence and from an optional improvement. Do not describe every unqualified item as certain hardware failure.

Use **PASS, FAIL, HOLD, NOT RUN** only for a named check and inspected revision, not a blanket executive sign-off. Summarize **P separately from the original A/B/C production/field gates**, with remaining conditions and owners. State exactly which commands ran, results and limits, sources/dates, untested cases and missing evidence. A prototype build verifies files with holds deferred; it does not close C4/C5/W3/W1/W4 or grant upload/order/field/surge approval. Do not turn a production-refusal workflow PASS into a publication claim or infer hardware qualification from artifacts.
