markshuttle/dogfence-pcb/pcb/DFM_EVIDENCE.md

# DFM Evidence

Research date: **2026-09-07**. Original DFM baseline: **97e202d**; SMT-resistor
review: **02661d8**, followed by the manufacturer-land correction retained below.
**PS12 replacement review: 2026-09-08**, with no geometry change.
**TE 3521 prototype evidence correction: 2026-09-11**, with no geometry change.
**SMT AC crossover selection: 2026-09-14**, with the explicitly approved
1.2.0-dev AC/front-B/rear-B and return-stem changes retained below as history.
**Westward GDT/via spacing selection: 2026-09-14**, with the explicitly approved
placement/front-B changes below.
**East board extension: 2026-09-15**, with the approved outline/H2/H4 changes
recorded separately under [East Board Extension](#east-board-extension).
Hardware **1.2.1-dev**. Scope: P3/P4 board design and five assembled prototypes.

Dimensions are millimetres unless explicitly marked inches. Global coordinates
use [ASSEMBLY's top-view convention](ASSEMBLY.md#drawing-conventions); local
coordinates are identified separately below. [BOM.csv](BOM.csv) controls the
current population; [Reviewed Components](ASSEMBLY.md#reviewed-components)
indexes its assembly applicability and expected file inventory.

**Evidence, not supplier approval.** The TE prototype body fits the retained
envelope, but its lands remain a project alternative under **W4** and catalogue
rating transfer to this mounting remains conditional under **W3**. The dated
reviews below preserve those corrections and the historical PS12/HP12/axial
investigations. The separately dated AC selection changed population/routing;
the later westward selection changes placement/routing only. The east board
extension changes only the outline and H2/H4, not copper, electrical components
or part/datasheet evidence. None changes qualification status or rewrites those
earlier investigations.
[Physical Guardrails](ASSEMBLY.md#physical-guardrails) controls preservation;
[SMA assembly evidence](ASSEMBLY.md#indicator-sma-and-resistor-assembly) owns the
retained Vishay 89429, 25-Feb-2020 p4 outline/land review. Historical diameter-only
screens below are not the current THT hole schedule.

Prototype files still require every file/diagnostic/sourcing check, with
**C4/C5/W3/W1/W4 deferred, not closed**, in [verification.json](verification.json).
Production/field release remains held. Supplier part/fit/forming/process,
allocation, placement and processed CAM acceptance are separate order duties;
switch/environmental and received-board qualification do not gate prototype
files. No supplier response, physical test or fresh publication result is
implied. [Artifact controls](ASSEMBLY.md#prototype-artifacts) explain the required
source-matched manifest and scope notices. All seven notes, BOM and ledger ship
flat in the full release, not as the complete contents of either fabrication ZIP.

Optional **repository-only** references: [MATERIALS](../MATERIALS.md) owns purchase
history; [README's master DFM policy](../README.md#via-and-component-hole-dfm)
remains normative. This note supports that policy with evidence and calculations;
its sibling assembly controls and local acceptance duties remain usable without
the root guides.

## Westward Spacing Selection

**2026-09-14, hardware 1.2.1-dev: user-approved alternate WESTWARD selection,
not a native, supplier or hardware PASS.** The initially requested eastward
shifts would short unlike-net GDT pads; the exact mirrored westward proposal
also fails the intended spacing/process objectives. The approved alternative
and the disclosed J_IN fit tradeoff are distinct from those rejected cases.

The pre-implementation source-shape assessment is recorded by the
repository-only `tmp/gdt-spacing-feasibility-2026-09-14.py`. It is bound to the
**old 1.2.0-dev PCB SHA-256**, not the edited 1.2.1 source:

```text
84975df16c7241a78c24ba80c33dddadf3c091a93481e685fe0f58a5ed2e38eb
```

The helper's `unapproved_west_candidate` label records its assessment-time
status; the user subsequently approved that alternative. Do not edit the
historical label/hash or run this snapshot-bound helper on changed source.
The following are handed-off nominal source-shape results with the dimension
arithmetic checked separately, not a fresh full-source/native verification.

| Dated candidate disposition | X shifts from 1.2.0-dev: nine rail vias / AB+BC and four stubs / AC and two takeoffs | Source-only finding |
| :--- | :--- | :--- |
| Requested east, **REJECTED** | **+4.00 / +4.00 / +2.00**; front-B stop stays X=121.00 | AB/BC B pads overlap AC pads by **1.20** horizontally. AC pads also intrude into the retained GDT_B_E.1 pad by **0.029455883**. These are unlike-net shorts, not small positive clearances. |
| Exact mirrored west, **REJECTED** | **-4.00 / -4.00 / -2.00**; translated front-B stop X=117.00 | Unlike-net inter-GDT pad gap remains only **2.80**. First rail vias at X=108.50 leave **zero nominal mask barrier** to J_IN: `2.50 - 0.90 - 1.60 = 0.00`. Same-net component mask is not exempt. |
| Alternate west, **SELECTED 1.2.1-dev** | **-3.50 / -4.50 / -2.10**; front-B stop X=115.00 | Unlike-net inter-GDT pad minimum **3.20**; first-via/J_IN mask gap **0.50**. The J_IN-to-AB/BC courtyard gap reduces **4.75 to 0.25**, explicitly disclosed and user-approved; no nominal courtyard clash, **physical fit not proven**. |

For the east case, the signed pad-edge gap is
`(125.80 + 2.00 - 2.75) - (119.50 + 4.00 + 2.75) = -1.20`.
The retained B_E pad relation is
`sqrt(0.45^2 + 1.40^2) - 1.50 = -0.029455883`.
These rejected assessments are not implemented geometry or supplier acceptance.

[ASSEMBLY](ASSEMBLY.md#physical-guardrails) owns the complete current controls:
rail vias **X=109.00/110.50/112.00**, AB/BC and their four **3.20 F.Cu** stubs
**X=115.00**, AC and its two front-only **3.20** takeoffs **X=123.70**, and
front B **3.20 wide, (106.00,122.50)..(115.00,122.50)**. All moved-item Y
coordinates, GDT zero rotations, pad mappings, local lands/body/courtyards,
parts and nets are unchanged. Via drills/copper remain **1.00/1.80**,
untented on both sides, no fill/plug/cap and no paste. Main A/C rails remain
**3.20 on both faces**. Rear B remains **exactly 6.00, X=106.00..131.00**, with
return **X=136.50**; EARTH and its five vias, mounts and indicator routing are
unchanged. No extra via, new circuit or blanket front-side clearance rule is
authorized.

### Westward Clearance Evidence

**Current 1.2.1-dev nominal geometry, not a finished-board or native result.**
All six SMT-GDT lands retain **5.50 X x 1.20 Y**, zero effective mask/paste margins,
and no drills. AB/BC lands now span **X=112.25..117.75**, with the unchanged
[four Y intervals](#smt-land-resolution). AC centres are
**(123.70,120.50)/(123.70,124.50)**, spanning **X=120.95..126.45** and
**Y=119.90..121.10 / 123.90..125.10**. Local body/courtyard dimensions remain
those reviewed for the [initial SMT conversion](#crossover-clearance-evidence).

| Relationship | Nominal source evidence / clearance, mm |
| :--- | :--- |
| Unlike-net pads on different GDTs, minimum | **3.20**: AB.2-to-AC.1 and BC.1-to-AC.2, `120.95 - 117.75`, with overlapping Y intervals. This is not the same-tube land gap. |
| AC pads to retained GDT_B_E.1 copper/open mask | Pad at **(131.00,122.50)**, diameter 3.00: `sqrt(4.55^2 + 1.40^2) - 1.50 = 3.260514678`. |
| AC apertures to retained GDT_B_E.1 drill | Same corner, hole diameter 1.50: `sqrt(4.55^2 + 1.40^2) - 0.75 = 4.010514678`. |
| AC pads to front-B main round cap | Endpoint **(115.00,122.50)**, radius 1.60: `sqrt(5.95^2 + 1.40^2) - 1.60 = 4.512487219`. Cap reaches X=116.60. |
| AC pads to all front WIRE_B copper, minimum | **3.20**, controlled by the AB/BC B lands, not by the shortened main-rail cap or the retained B_E pad alone. |
| Opposite-net copper within each SMT tube | **2.80 land/mask/paste gap**, but **1.80 connected-copper gap** with retained rounded stub endpoints. AC endpoints remain Y=120.00/125.00; AB/BC endpoints remain Y=116.19/121.19/123.81/128.81. Do not extend tracks to pad centres. |
| AB.2 to BC.1 facing lands | **2.42**, `123.71 - 121.29`, both **WIRE_B**. Not an unlike-net differential-flashover case or a new front-clearance rule. |
| J_IN to AB/BC courtyards | **0.25**, X=111.75 to 112.00, formerly 4.75. User-approved drawing-space reduction, not actual connector/GDT/tool fit proof. |
| AB/BC to AC courtyards | **2.70**, X=118.00 to 120.70. |
| AC to GDT_B_E courtyards | **2.52**, X=126.70 to 129.22. |
| AC body including 0.10 projected pose to front B | AC X bounds **120.995..126.405**. To main cap **4.395**; to AB/BC B lands **3.245**; to B_E.1 pad **3.095**. No front B under that bounded body projection; solder seating/tilt still needs inspection. |

The nearest rail via at **X=112.00** and AB/BC aperture corner at **X=112.25**
have **dx=0.25, dy=1.21**. Full-shape radii, not centre clearance alone, give:

```text
corner distance = sqrt(0.25^2 + 1.21^2) = 1.235556555
to nominal 1.00 drill circle            = 0.735556555
to nominal 1.80 annulus/open mask       = 0.335556555
```

At the first rail via **X=109.00**, J_IN's **X=106.00** pad is 3.00 away:
mask-opening edge gap **0.50** (`3.00 - 0.90 - 1.60`), drill-to-drill gap
**1.50** (`3.00 - 0.50 - 1.00`), and via-drill to component-mask gap **0.90**.
These are distinct source budgets; neither same net nor adjacent via-to-via
mask overlap excuses component mask/paste over a via hole. All actual processed
drill/aperture sizes, registration allowances and solder spread remain to accept.

The first two via centres on each rail, **X=109.00/110.50**, now lie under
J_IN's conservative body/courtyard projection. The controlled body envelope reaches
**X=111.40**, **111.50 with 0.10 pose**, and courtyard **111.75**; part of each
X=112.00 annulus also enters that projection. Inspect actual moulding/seating,
full openings, drain-through, wetting and solder beads, not just the absence of
a GDT/connector courtyard overlap. No new body clearance, process approval or
physical qualification is claimed, and no courtyard/land reduction is selected.

Native integration exposed two J_IN silk/mask clashes caused by the relocated
openings. The source and local input footprint now omit only the east/rear
F.SilkS edge; the mirrored B.SilkS reference moves to **(106.00,108.50)**.
Pads, the F.Fab maximum-body box and full courtyard remain unchanged. This is
a legend correction, not via covering, body-clearance relief or physical fit
approval. The other eight local footprint definitions are unchanged.

Rear different-core minimum remains **3.02**, including the retained **3.10**
return gap; fence/EARTH minimum remains **3.25 on both faces**. The native and
independent **>=3.00 rear-only** inter-core controls and both-face fence/EARTH
controls remain required. The nominal **3.20 front inter-GDT pad gap does not
guarantee 3.00 finished** and does not apply to every F.Cu gap. Rear B still
passes below AC through the nominal FR-4 core; mask, gel, body projections and
these source distances do not qualify physical impulse insulation.

The **0.420 mm^2 / 93.75%** ideal-area comparison from the initial conversion
is unchanged, but the last-B-via lumped path to GDT_B_E.1 is now
**`131.00 - 112.00 = 19.00 mm`**, not the former **15.50**. Any length-dependent
screen must use that current geometry under
[DESIGN_BOUNDS](DESIGN_BOUNDS.md#ac-conversion-copper-screen); nominal metal
area is not a board current/surge rating or equal-layer-sharing proof.

All **C4/C5/W3/W1/W4** holds remain open. Supplier CAM/placement, allocated-lot
fit/process, earth-GDT forming and W5 enclosure/support/material acceptance are
unchanged duties. The changed source and controlled notes require a **fresh
matching artifact snapshot**, not relabelling a 1.2.0 package. Require recorded
native/annotation/workflow verification and the revision-specific release
decision; this selection is not that evidence.

## SMT AC Crossover Selection

**Historical first SMT conversion, 2026-09-14, hardware 1.2.0-dev: user-approved
selection, not a native or hardware PASS.** The dimensions below preserve that
snapshot; [Westward Spacing Selection](#westward-spacing-selection) controls
1.2.1-dev placement. GDT_AC changes from Bencent B5G470L / C5337217 to the same
**Ruilon SMD5050-470NA / C39692533** already selected for AB/BC. The original
[manufacturer][ruilon-smt-m] and [distributed][ruilon-smt-l] **SP-GDT-006 A3,
2024-08-19**, especially p3's body/land leaders, were already reviewed under
[Figure Access](#figure-access) and [SMT Land Resolution](#smt-land-resolution).
No footprint redesign, fresh manufacturer retrieval, corrected drawing, stock
reservation or supplier approval is inferred from using it for the third tube.

The initial 1.2.0-dev construction retained AC origin
**(125.80,122.50), 0 degrees**, with new north/south A/C SMT
lands, **F.Cu-only** takeoffs, front-B cutback, **exactly 6.00 mm rear B** and
the necessary **1.00 mm rightward return-stem shift**. AB/BC parts/stubs,
A/C main rails on both layers, EARTH, all fourteen dedicated vias, mounts and
indicator routing remain unchanged. Only the two retired AC component holes
and their barrel links are removed; retained input/earth-GDT PTHs and dedicated
stitches still link layers. That is not preservation of every former parallel
barrel path.

The rear width is **6.00, not the proposed 6.40**. With 7.62 rail spacing and
3.20 A/C widths, the nominal straight-rail edge gap is
`7.62 - 6.00/2 - 3.20/2 = 3.02`; a 6.40 B strip would leave **2.82**, below
the new **>=3.00 rear A/B/C copper requirement**. Width alone was insufficient:
the full-source rear-copper analysis in repository-only scratch
`tmp/gdt-ac-6mm-review.py` found the existing **X=135.50, 1.60-wide B-return
stem** only **2.10** from the A/C rail ends, with either the old or widened B
strip. Meeting the user's whole-back clearance requirement also requires moving
the stem to **X=136.50**. This necessary localized routing adjustment was disclosed
before implementation; all Y coordinates, widths and terminal endpoints remain.
Five adjoining 1.60-wide segments change their stem-side coordinates only.
The stem-to-A/C gap becomes **3.10**; the nominal whole-rear different-core
minimum becomes **3.02**, while global fence/EARTH separation remains **3.25**.

Require a **native >=3.00 different-A/B/C-net clearance rule on B.Cu only** and
an independent full-source guard covering all rear copper, including tracks,
PTH pads and vias, not just the three long strips. The independent **>=3.00
fence/EARTH separation on both faces** remains unchanged. Fresh integrated
native and export checks must verify the changed source; the source-shape
calculation is not that result. The **0.02 mm
nominal margin** over the rear design threshold is small: source coordinates
do not guarantee **>=3.00 on the finished etched board**. Obtain accepted CAM,
etch/registration tolerances and finished-gap acceptance evidence; do not
silently widen B to recover area or lower the rule to obtain a PASS.

Using nominal 0.070 mm exterior copper, the rear crossover strip has
`6.00 * 0.070 = 0.420 mm^2`, **93.75%** of the former ideal dual-3.20 sum
`2 * 3.20 * 0.070 = 0.448 mm^2`. This is a local ideal-area comparison, not
restored full area, guaranteed finished copper, equal layer sharing, replacement
barrel area or a board current/surge rating. [ELECTRICAL](ELECTRICAL.md) retains
the circuit/protection limitations; [DESIGN_BOUNDS](DESIGN_BOUNDS.md) owns named
current/thermal screens, not this drawing-only comparison.

**2026-09-14 applicability erratum:** all B5G470L pin/body/hole/forming and
overpass calculations retained below describe the **retired axial AC design**.
They are not current supplier tasks or a reason to impose a raised gap on SMT
AC. The former **>=2.00 gap, 2.50 +/-0.25 underside, <=8.50 complete height**
process was never physically qualified; removal of that construction is not
qualification closure. Only the three earth GDTs remain axial, with their
existing forming/lot/process holds. All **C4/C5/W3/W1/W4** holds remain open.

### Crossover Clearance Evidence

These are **historical 2026-09-14, 1.2.0-dev nominal source-shape dimensions**,
not finished-board measurements, processed CAM acceptance or a new native DRC
result. They do not describe the [1.2.1-dev westward geometry](#westward-clearance-evidence).
The shared SMD5050 pattern is unchanged: each **5.50 X x 1.20 Y** rectangular, undrilled
F.Cu/F.Mask/F.Paste land uses zero effective mask/paste margins. At AC the A/C
centres are **(125.80,120.50)/(125.80,124.50)**; both lands span
**X=123.05..128.55**, with **Y=119.90..121.10 / 123.90..125.10** respectively.
The retained project footprint has a **5.21 X x 4.50 Y** maximum-body box based
on the already reviewed dimensions and a **6.00 X x 7.50 Y** project courtyard,
not a manufacturer-specified assembly envelope. End-face height is **<=5.21
before solder seating**, not the axial 4.2 dimension; this applies to all three
SMT tubes.

| Relationship | Nominal source evidence / clearance, mm |
| :--- | :--- |
| Opposite A/C copper under AC | New 3.20-wide takeoffs stop at **Y=120.00/125.00**, each 0.50 outward from its land centre. Round caps end at **121.60/123.40**, leaving **1.80** connected-copper gap, versus **2.80** between lands/mask/paste. |
| Front-B cap to either AC land | Front-B endpoint **(121.00,122.50)**, radius 1.60: `sqrt(2.05^2 + 1.40^2) - 1.60 = 0.882438`. No right-hand front-B track stub is needed; GDT_B_E.1 retains its front PTH pad through the rear connection. |
| Existing AB/BC B land to nearest AC land | **0.80**, from X=122.25 to X=123.05 where their Y spans overlap. This is a front-side component gap, not the >=3.00 rear-core rule. |
| AB/BC courtyard to AC courtyard | **0.30**, X=122.50 to X=122.80. |
| AC courtyard to GDT_B_E courtyard | **0.42**, X=128.80 to X=129.22. Drawing space, not proven rework/tool access. |
| Nearest AC aperture to hole, GDT_B_E.1 | Hole at **(131.00,122.50)**, diameter 1.50: `sqrt(2.45^2 + 1.40^2) - 0.75 = 2.071790`. Full drill circle, not just the centre. |
| Same AC aperture to full annulus/open mask | GDT_B_E.1 diameter 3.00: `sqrt(2.45^2 + 1.40^2) - 1.50 = 1.321790`. Compare actual processed apertures and registration, not only nominal pad copper. |
| Front B to maximum AC body including pose | West body bound **125.80 - 5.21/2 - 0.10 = 123.095**; front-B cap reaches **122.60**. Minimum **0.495**, including 0.10 projected pose; no front B under that body envelope. |

Rear B spans **Y=119.50..125.50**, below both complete AC lands and body,
separated in the source stackup by **nominal 1.440 mm FR-4**. Removing front B
from below the body is not removal of that through-board crossover. Neither
the FR-4 model, nominal surface gaps nor mask/OneGel establish physical impulse
qualification or approved insulation. Inspect seating/tilt, solder spread and
the processed copper/mask/stencil; the existing **4.00 mm versus 0.165-inch
discrepancy and W1 stencil/profile hold apply to all three SMT GDTs**. The
[current assembly and acceptance controls](ASSEMBLY.md#acceptance-record) remain
binding; no AC forming acceptance is newly claimed.

## TE 3521 Prototype Selection

The **2026-09-11** independent review visually read original TE **CGS 3521 Series,
Data Sheet 9-1773463-5 Rev G, 02/2025, PDF pages 1-5**. The printed revision
differs from the earlier **03/2023** citation. No March 2023 TE PDF/page images
were retained in the inspected project `tmp/` or `/tmp/opencode`; staged project
notes repeating that date are not a manufacturer source. No material comparison
against an unretained March 2023 edition is asserted.

| Source | Readable evidence / limitation |
| :--- | :--- |
| [Original TE 3521 PDF][te-pdf], Rev G 02/2025 | **V: pp1-5**. p1 ratings/ambient derating, AEC-Q200 and MSL 1; p2 working-voltage formula/body/terminal bands; p3 recommended lands and four-layer reference PCB; pp4-5 performance-test conditions. These do not establish the earlier exact-pattern or PS12-derived test claims. |
| [JLCPCB C4129105](https://jlcpcb.com/partdetail/C4129105) | Identifies **TE Connectivity 35212K2FT, 2.2 kohm, 2 W, 1%, +/-100 ppm/C, 2512**, classified as an Extended Part for automated PCBA assembly. Identity is not receipt or job allocation. |
| [JLCPCB C876850](https://jlcpcb.com/partdetail/C876850) | Direct listing verified 2026-09-11: **YAGEO SR2512FK-7W2K2L, 2.2 kohm, 2 W, 1%, +/-100 ppm/C, 2512**. Unpopulated production variant's identity only, not receipt, job allocation or independent model/footprint/process/thermal acceptance. |

### TE 3521 Body And Lands Fit

TE p2 gives **L=6.35 +/-0.10, W=3.20 +/-0.20, H=0.55 +/-0.10**: maximum body
**6.45 x 3.40 x 0.65 mm**. Terminal bands are distinct: **l1=0.60 +/-0.25 top**
and **l2=0.50 +/-0.20 bottom**, not a common 0.55 +/-0.25 band.

The existing `R_2512_6332Metric` F.Fab remains **X=+/-3.225, Y=+/-1.70** and
F.CrtYd **X=+/-4.05, Y=+/-2.10**, respectively **6.45 x 3.40** and **8.10 x 4.20**.
Body containment is supported; it is not a manufacturer-exact land-pattern or
electrical drop-in approval.

TE p3's drawing leaders identify **A as transverse width, B as longitudinal pad
length and C as the inner gap**. The table gives A=3.0, B=1.5, C=5.0 mm:

| Land geometry, mm | TE p3 recommendation | Retained project alternative |
| :--- | ---: | ---: |
| One rectangular land, X x Y | **1.50 x 3.00** | **1.35 x 3.70** |
| Inner gap | **5.00** | **4.90** |
| Centre pitch, derived | **6.50** | **6.25** |
| Outside span, derived | **8.00** | **7.60** |
| Local pad centres, derived | **X=+/-3.25, Y=0** | **X=+/-3.125, Y=0** |

The HP/PS-derived alternative remains undrilled, top-side F.Cu/F.Mask/F.Paste
with project-selected zero additional mask/paste margins. All actual pad
positions and routing remain unchanged. Accept the **specific retained
alternative** through the existing W4 supplier placement/stencil/solder-process
review, not by relabelling it as TE's recommendation. A different recommendation
does not by itself prove the alternative unusable or require a reroute.

For nominal PCB lands and a centered TE body, these are **geometric extensions,
not guaranteed wetted fillets**; PCB fabrication and placement errors are excluded:

| Extension per side/end | Calculation | Conditional geometry, mm |
| :--- | :--- | :--- |
| Outer toe | `3.80 - L/2` | **0.625 nominal; 0.575..0.675** over published L tolerance |
| Inner land beyond bottom band (heel) | `L/2 - l2 - 2.45` | **0.225 nominal, not a guaranteed minimum**; body/band and placement tolerances still apply |
| Transverse side | `(3.70 - W)/2` | **0.25 nominal; 0.15 minimum** over published W tolerance, before placement error |

Inspect actual seating, wetting, fillets and solder volume. The 0.65 body-height
maximum excludes solder seating height; no axial standoff applies.

### TE Rating And Mounting Basis

TE p3 explicitly states **four-layer PCB, 2 oz outer layers and 4 oz inner
layers**. The project remains **two-layer, 2 oz per side**. Transfer of the
catalogue power/derating basis to this mounting is conditional on adequate heat
flow and accepted assembly; actual continuous thermal qualification remains
**W3**, and alternate-land/process acceptance remains **W4**. This is not proof
that two layers fail or that 2 W is possible only on four layers. Do not change
the protected stackup/copper to manufacture a claimed match.

- **Power/working voltage, pp1-2:** 2 W at 70 C ambient, constant from -55 to
  70 C and linearly derated to zero at 155 C; operating range **-55..155 C**.
  Family working/overload/dielectric
  ceilings are **250/500/500 V**. `min(250, sqrt(P*R_nominal))` gives **66.33 V
  RCWV** at catalogue 2 W / 2.2 kohm; this is not a system operating voltage.
- **TCR, p4:** **+/-100 ppm/C for 100 ohm < R <=10 Mohm**, covering 2.2 kohm.
  The method calls for characterization at room and minimum/maximum operating
  temperatures, marked **User Spec**. The model's **25 C reference, -30..125 C
  study and -55..125 C supported inputs are engineering assumptions**, not TE
  test conditions. [DESIGN_BOUNDS](DESIGN_BOUNDS.md#evidence-and-inputs) leaves
  numeric manufacturer test endpoints unknown.
- **Overload, pp1-2/4-5:** the inspected sheet gives a 500 V family ceiling but
  does **not establish the 2.5*RCWV, five-second test** previously carried over
  from PS12. No short-time or pulse capability is inferred; applicable TE or
  standard evidence would be needed to establish those conditions. This is not
  a claim that no such specification exists elsewhere.
- **Heat/process:** retained **0.501018 W nominal / 0.756803 W upper per resistor**
  are conditional DC calculations under [DESIGN_BOUNDS](DESIGN_BOUNDS.md#thermal-screens),
  not measured chip/pad/PCB temperatures or a cooler result. PR02
  hot-spot/K/W/standoff data do not apply. TE p5 solderability
  and soldering-heat tests are not an accepted stencil/reflow recipe; PS12's
  historical reflow profile is not automatically transferable.

These TE results do not qualify the unpopulated Yageo production variant; apply
the [independent review/substitution controls](ASSEMBLY.md#reviewed-components)
before changing the population.

## PS12 SMT Selection (Historical Review)

**Historical only, not current population or TE/Yageo specifications.** This
preserves the then-selected **Uni-Royal PS122WF2201T4E / C2793873** and its
manufacturer evidence, not available inventory or job allocation.

The bounded **2026-09-08** review used the actual **PS Series** document from
**Uniroyal Electronics Global Co., Ltd.**, not the HP datasheet. The cover and
printed footers identify **SMD-SP-007, V.7, 08-Jan-2026**, eleven pages; the
July-2026 upload date is not a drawing revision.

| Source | Readable evidence / limitation |
| :--- | :--- |
| [Original manufacturer PS PDF][ps-pdf] | **V:** pages **1, 2, 4, 5, 6, 7 and 8**: cover, ordering, body/land leaders, ratings/derating, one-pulse curves, TCR/overload and reflow. Public Google PDF-viewer page images were visually read; text extraction was supplementary, not dimensional proof. |
| [Manufacturer PS12 product page][ps-page] | PS12, 2 W, 0.5%/1%/5% options, 0.1 ohm..10 Mohm, **+/-100 ppm/C**, consistent with the PS PDF. Links the PS specification, not HP. |
| [JLCPCB C2793873][ps-jlc] and [LCSC C2793873][ps-lcsc] | Both identify **PS122WF2201T4E, 2.2 kohm, 2 W, 1%, +/-100 ppm/C, 2512**, with a 500-V family label. Public identity is not receipt, inspected lot or board-job allocation. |
| [Stable LCSC datasheet entry][ps-distributed] | Resolves to [this PDF target][ps-target]; attempted retrievals did not yield usable drawing pages. No distributor-PDF revision is established here; the manufacturer PS PDF controls the drawing review. |

Page 2 decodes **PS12 / 2W / F / 2201 / T4 / E** as PS12, 2 W, 1%, 2200 ohm,
tape/reel with a standard 4,000-piece reel, standard feature. It does not require
a full-reel purchase for five prototypes or establish job allocation.

Then-reviewed metadata was **`MPN=PS122WF2201T4E`**, **`LCSC Part #=C2793873`**,
**`Sourcing=LCSC`**, empty **`Sourcing Reference`**, and [the PS manufacturer
PDF][ps-pdf] as **`Datasheet`**. No NAC external-source row or pending HP code
applied to PS; these are historical metadata, not current sourcing instructions.

### Body And Lands

PS page 4's body drawing gives **L=6.35 +/-0.10, W=3.20 +/-0.20 and H=0.55 +/-0.10**,
therefore maxima **6.45 x 3.40 x 0.65 mm**. Its top termination length A is
0.60 +/-0.25 and bottom termination length B is 0.50 +/-0.20. Those letters are
body-drawing dimensions, not the separate land-pattern letters on page 5.

PS page 5's original leaders independently identify:

| Land drawing field | Meaning | Manufacturer recommendation, mm |
| :--- | :--- | ---: |
| A | Inner gap between lands | **4.90 +/-0.10** |
| B | One land's longitudinal length | **1.35 +/-0.10** |
| C | Transverse land width | **3.70 +/-0.10** |
| D | Outside span | **7.60 +/-0.10** |

The PS review retained these nominal values as **rectangular, undrilled
F.Cu/F.Mask/F.Paste lands**, with **zero effective mask margin, paste margin and
paste ratio**. They matched the HP-derived geometry; no PS land deviation was
needed. `D = A + 2B` keeps the dimensional choices consistent. The zero margins
are the project's aperture choice, not a manufacturer stencil specification.
Centre pitch is `4.90 + 1.35 = 6.25`, hence local X=**-3.125/+3.125** for
pad 1/pad 2. Each nominal land has **4.995 mm^2** area. Customer F.Paste remains
a source datum, not approval of the assembler's processed aperture or deposit.

The maximum-body F.Fab is **X=+/-3.225, Y=+/-1.70**. The selected courtyard is
**X=+/-4.05, Y=+/-2.10**: lands plus 0.25 per side need **8.10 x 4.20**;
maximum body plus 0.10 projected pose and 0.25 assembly clearance needs
**7.15 x 4.10**, which fits inside it. Body height 0.65 excludes solder seating
height. The chip is not assigned the retired resistor's axial body standoff.

### Placement And Routing

The PS review did not change placement/routing; the retained TE implementation
uses the same [origins, pad/net mappings and indicator routing](ASSEMBLY.md#placement-and-polarity).
Preserve nonpolar R1/R2 pad numbering, one-way D1/D2 branch order, straight
cathode links, takeoffs and shunt routes. The
[physical guardrails](ASSEMBLY.md#physical-guardrails) prohibit an unapproved
folded branch, new via or change to the protected rails/EARTH/returns/mounts/LEDs.

### Rating And Process

- **PS TCR basis, p7:** +/-100 ppm/C, with reference temperature **25 C or
  specified room temperature** and test temperatures **-55/125 C**. The PS web
  page agrees. These inputs supported the PS resistance screen, not TE's test
  conditions; neither the separate 155 C operating endpoint nor PR02's
  250 ppm/K model was used for that screen.
- **Power/voltage:** 2 W through 70 C ambient, linear derating to zero at 155 C.
  PS pp4/5 specify **500 V maximum working / 1000 V maximum overload / 500 V
  dielectric withstand**, operating range -55..155 C. The working limit is also
  constrained by `RCWV = sqrt(P*R)`, still **66.33 V** for nominal 2.2 kohm at
  2 W. Page 7's five-second overload test uses the lower of `2.5*RCWV` and
  1000 V, still **165.83 V**, with +/-(1% +0.1 ohm) resistance-change limit
  for the 1% part. The family voltage labels are not allowable continuous
  voltages for every resistance value.
- **One-pulse limits, p6:** PS supplies separate **power-versus-duration and
  voltage-versus-duration curves**; both constrain use. No curve digitization,
  repetitive-pulse rating or assembled-board/transient qualification is claimed.
  The HP review's absence of established pulse curves is not a PS fact.
- **Heat path:** the PS nominal comparison still dissipated about **0.50 W per
  resistor**. Neither the family change nor wider tracks establishes reduced
  heat or temperature; **PR02's hot-spot limit and 75 K/W mounting example do not
  apply**. See the [assembly heat-path limitation](ASSEMBLY.md#2512-smt-resistors),
  not a completed continuous-duty test.
- **Reflow:** visually read p8 recommends SAC305, 150..200 C preheat for
  60..120 s, <=3 C/s ramp-up, 217 C liquidus for 60..150 s, **260 C peak**,
  10 s within 5 C below peak, <=6 C/s ramp-down, <=8 minutes from 25 C to peak
  and **two reflow cycles**. The manufacturer explicitly calls for application
  adjustment. Actual mixed-assembly/stencil acceptance remains a supplier fact,
  not permission to apply the most permissive GDT heat-test limit to every part.

These PS-specific limits remain historical, not transferable TE or Yageo
specifications.

## HP12 Investigation History

**Historical 2026-09-07 review of 02661d8, not PS research or current sourcing
instructions.** The then-intended HP122WF2201T4E remained without a verified
JLCPCB/LCSC code. Its manufacturer document was **SMD-SP-003, HP Series, V.7,
08-Jan-2026**, from Uniroyal Electronics Global Co., Ltd., carrying Uni-Royal,
Royalohm and Uniohm branding; the July upload date was not its revision date.

| Historical source | Evidence retained / limitation |
| :--- | :--- |
| [Original manufacturer HP PDF][hp-pdf] | **V:** pages **1, 2, 4, 5, 6 and 8**, including cover, ordering, body/land leaders, ratings/derating, TCR/overload and reflow. **T:** full eleven-page text through [the reader][hp-text]. No dimensions were inferred from an unreadable figure. |
| [Manufacturer HP product listing][hp-page] | HP12, 2 W, 0.5%/1%/5% options. The applicable range was listed at **+/-75 ppm/C**, conflicting with the PDF's **+/-100 ppm/C**. The tighter figure was not adopted. This conflict does not transfer to PS. |
| [LCSC C2791283][hp-wrong-lcsc] and [JLCPCB C2791283][hp-wrong-jlc] | Both identify **HP122WJ0472T4E, 4.7 kohm, 5%, 2 W, 2512**, not HP122WF2201T4E or PS122WF2201T4E. The old mapping was rejected; internal metadata parity could not cure that identity mismatch. |
| [NAC Semi former intended-MPN listing][hp-nac] | Readable **ROYALOHM HP122WF2201T4E, 2512, 2.2 kohm, 1%, 2 W**; retrieved MOQ **3,600**. Former external BOM/source reference, not an accepted small-lot quote, JLCPCB code or allocation. Public stock was indicative only. |

The [HP-associated LCSC PDF][hp-distributed] did not yield usable drawing pages;
no revision or dimensional proof was assigned to it. TME returned HTTP 403 and
Mouser an access-denied page. Exact/prefix searches did not establish an HP code
or packaging-only alternative: the [JLCPCB exact search][hp-search-jlc] and
[known-listed HP122WJ0472T4E control][hp-control-jlc] both returned
JavaScript-dependent zero-result pages; [LCSC search][hp-search-lcsc] returned
`Search by ""` without rows. These were retrieval limitations, not proof of HP
unavailability. No HP supplier response, purchase or board-job allocation was
established by that investigation.

HP p2 decoded **HP12 / 2W / F / 2201 / T4 / E** as 2 W, 1%, 2.2 kohm,
tape/reel with a standard 4,000-piece reel and standard feature, not a requirement
to purchase a full reel. HP's recorded family working/overload limits were
**300/500 V**, with 500 V dielectric withstand and a five-second overload test;
no one-pulse curve was established in that HP review. Both HP and PS limits are
now historical; the active TE evidence is separately recorded above.

**Historical land correction, not approved alternate geometry:** 02661d8 used
1.80 x 3.40 roundrect lands at +/-2.80, 3.80 inner gap and 7.40 outside span,
with 6.30 x 3.20 F.Fab and 7.90 x 3.90 courtyard. Its F.Fab did not bound the
HP12 maximum body; the courtyard was 0.10 short per transverse side under the
stated pose/assembly budget. No neighbour collision was demonstrated. The prior
manufacturer-land correction replaced that deviation; the later PS review
independently supported those corrected lands. They are retained as an alternate
pattern for TE, not as TE's recommendation. Internal/native consistency was not
land-pattern approval.

## Conclusions

- **TE prototype selection:** exact C4129105 identity is resolved; maximum body
  fits the retained envelope, but **TE p3 recommends different lands and a
  four-layer reference PCB**. Retain current geometry as a project alternative
  pending W4 supplier acceptance and W3 thermal/mounting qualification. Neither
  an exact mechanical/electrical drop-in nor a two-layer failure is established.
- Original mechanical figures for **all six requested part families were
  visually read**, including the Kefa tolerance tables and both Ruilon THT
  revisions. Their dimensional associations are no longer a text-reader hold.
- Ruilon **2R470TD-8** has a drawing lead maximum of **1.05 mm**. Its former
  97e202d 1.20 mm hole left only `1.20 - 0.08 - 1.05 = 0.07 mm`, below the
  required 0.10 mm allowance; the retained selected hole is **1.50 mm**. Its
  metric maximum body is **6.30 long x 8.20 diameter**.
- Kefa **KF128-7.62-3P** pins are rectangular, nominal **0.90 x 0.80**.
  **KF129-5.08-2P** has a real source conflict: **0.90 x 0.80** in the
  C475092-distributed drawing versus **0.95 x 0.80** in the manufacturer-linked
  drawing, both marked **A / 21.03.13**. The former 97e202d 1.40/1.30 holes were
  not a tolerance-supported solution; both retained selections use **2.00 mm**.
  In particular, the old KF129 hole failed the project allowance even using the
  smaller nominal pin, before adding pin tolerances.
- The retired Vishay MBE explicitly labels its **0.80 mm lead as nominal**.
  Bencent's original figure labels a **0.80 mm round lead without a tolerance**.
  Neither figure supplies a manufacturer-guaranteed finished lead maximum. A controlled
  **0.90 mm finished acceptance envelope** was proposed for each; at that
  checkpoint it remained operative only for **B5G470L**, with 1.40 mm holes.
  **2026-09-14 applicability erratum:** B5G470L is now retired too; current
  R1/R2 and GDT_AC are SMT. Neither historical E envelope is a current fit hold.
- Ruilon **SMD5050-470NA**: **X1 is pad centre-to-centre spacing**, not the inner
  gap or outside span. The metric recommendation translates to **5.50 x 1.20 mm
  lands at local Y = +/-2.00** in this board's orientation. The 4.0 mm / 0.165 in
  conflict exists in the original manufacturer PDF too. Use of the metric column
  is an explicit selected engineering choice, not a claimed manufacturer erratum.
- **Standard untented ENIG vias** are a supported alternative to unsupported
  1.00 mm filling/tenting assumptions. Preserve every 1.00/1.80 via and all
  protected copper. No special fill, press-fit tolerance or CAM exception is
  proposed as the solution.

## Figure Access

In the original DFM research, direct PDF requests with native `webfetch` returned
PDF streams rather than rendered pages. That was not treated as evidence that the figures were
unreadable. The original public URLs were then opened through Google's public
PDF viewer, and its page-image endpoints were fetched with native `webfetch`.
The returned image attachments, including dimension arrows and title blocks,
were visually inspected. No terminal network fetch or download script was used.
Existing `tmp/dfm-review/` and `tmp/layout-review/` directory listings were also
inspected without changing their evidence; they did not provide the requested
component drawings in the inspected listings.

The later PS12 review and the **2026-09-11 TE correction** used the same
public-viewer method for their respective original PDFs, independently of the
historical THT/GDT/HP retrievals. TE PDF pages **1-5** were visually inspected;
the full seven-page text was supplementary, not proof of drawing leaders.

Repeatable access method, not an alternative drawing authority:

1. Fetch `https://docs.google.com/gview?embedded=1&url=<URL-encoded-original-URL>`
   as HTML. Some initial requests returned an empty response; retrying succeeded.
2. Use the returned `img?id=...` URL under `https://docs.google.com/viewerng/`,
   with `&page=N-1&w=2400` for printed page N. `page` is zero-based;
   `pagenumber` did not select the requested page in this viewer.
3. Check the actual printed page number, MPN/family, revision and dimension
   leaders. Viewer IDs are temporary, so the permanent evidence links below
   identify the original files, not expiring image tokens.

**V** means original figure visually read; **T** means retrieved text.
**Derived** means arithmetic from published dimensions. **E** means a controlled
procurement/assembly envelope, **not a manufacturer guarantee**.
Original PDFs/images were not added to the workspace in this bounded task.

| Retained or explicitly historical identity | Original source and revision | Access actually used |
| :--- | :--- | :--- |
| Cixi Kefa KF128-7.62-3P / C474957 | [Manufacturer drawing][k128-m] and [C474957 drawing][k128-l], title KF128-7.62, revision A, 21.03.13, one sheet. Manufacturer [product page][k128-page] links the 7.62 drawing separately from 7.5. | V: both sheets, pin leaders, PCB layout and general tolerance table. P=3 applied to the family drawing. |
| Cixi Kefa KF129-5.08-2P / C475092 | [Manufacturer drawing][k129-m] and [C475092 drawing][k129-l], title KF129-5.08, revision A, 21.03.13, one sheet. [Product page][k129-page] identifies the 5.08 drawing. | V: both sheets. Different 0.95/0.90 pin-width labels despite identical revision/date; not silently reconciled. P=2. |
| **Historical, retired:** Vishay MBE04140C2201FC100 / C1368610 | [Document 28766][vishay], revision 11-Jul-2018, p13 dimensions; p4 ordering and p7 construction/assembly. [Document 28721][vishay-pack], revision 16-Jan-2025, packaging. | V: 28766 p13. T: ordering, tin-plated copper construction and packaging. Packaging did not establish a missing lead-diameter maximum. Not a current procurement/forming requirement. |
| **Historical, retired 2026-09-14:** Bencent B5G470L / C5337217 | [C5337217 PDF][bencent-l], A2 / 2018-01-03, p2. The then-current [manufacturer product page][bencent-page] supplied [this direct PDF download][bencent-m], also A2 / 2018-01-03. | V: p2 from both sources. The 20260514 upload pathname is not a new drawing revision. Lead diameter is printed directly on the figure, outside its A/B/C table. |
| Ruilon 2R470TD-8 / C2836978 | [Distributed SP-GDT-017][ruilon-tht-l], A3 / 2023-11-02, p3; [manufacturer SP-GDT-017][ruilon-tht-m], A6 / 2025-10-16, p5. Manufacturer listing [page 4][ruilon-page4] links A6 for 2R470TD-8. | V: both dimension figures, specifically the **TD axial** drawing, not the SD surface-mount drawing below it. Mechanical dimensions agree. |
| Ruilon SMD5050-470NA / C39692533 | [Distributed SP-GDT-006][ruilon-smt-l] and [manufacturer SP-GDT-006][ruilon-smt-m], A3 / 2024-08-19, p3. Manufacturer listing [page 5][ruilon-page5] links that file for the exact non-BVL MPN. | V: both p3 figures/tables; X/X1/Y leaders and body axes resolved. T: p5 reflow and p6 solder-bridging caution. No BVL or NB substitution used. |

## THT Dimensions

### Kefa

The printed general linear-tolerance table on **both** families says:
dimensions up to 6: +/-0.20; over 6 to 10: +/-0.30; over 10 to 30: +/-0.50 mm.
Its heading cites **GB/T 14486-2008**, a plastics dimensional-tolerance standard.
There is no separately stated plating/burr allowance for the metal pins.
Applying its +/-0.20 band to pin cross-sections is a conservative, drawing-based
**procurement envelope**, not a claim that the plastics standard independently
guarantees the maximum finished metal pin. The chosen limits must include the
actual tin plating and any permissible stamping/cutting irregularity.

| Association visually read | KF128-7.62, P=3 | KF129-5.08, P=2 |
| :--- | :--- | :--- |
| Rectangular pin cross-section | Front view width 0.90; side view thickness 0.80. | Front view width 0.90 in LCSC copy, 0.95 in manufacturer copy; side view thickness 0.80 in both. |
| Lead length below seating face | 4.30 +/-0.30. The table's "Pin Dimensions 4.3" is length, not diameter. | 4.80 +/-0.30. The table's "Pin Dimensions 4.8" is length, not diameter. |
| Body depth, front to rear | 10.50; pin row to rear face 5.20, hence nominal front projection 5.30. | 10.60; pin row to rear face 4.90, hence nominal front projection 5.70. |
| Body height above seating face | 14.10. Derived general-tolerance upper bound 14.60. | 18.30. Derived general-tolerance upper bound 18.80. |
| Main body length along pin row | P x 7.62 = 22.86; derived upper bound 23.36. | P x 5.08 = 10.16; derived upper bound 10.66. |
| End interlocking projection | Separately dimensioned 0.60; derived upper bound 0.80. Do not omit it from an isolated terminal's envelope. | Separately dimensioned 0.55; derived upper bound 0.75. |
| Actual part pitch callouts | 7.62 and (P-1) x 7.62, without individual +/- labels. General bands would be +/-0.30 on adjacent pitch and +/-0.50 on 15.24 overall span. | 5.08 and (P-1) x 5.08, without individual +/- labels; general band +/-0.20. |
| Recommended PCB, **not a pin tolerance** | Hole diameter 1.40 +0.10/-0.00; pitch 7.62 +/-0.03. | Hole diameter 1.40 +0.10/-0.00; pitch 5.08 +/-0.03. |

The Kefa PCB hole recommendation has **no negative hole tolerance**. A JLCPCB
nominal 1.40 component hole can finish at 1.32; it is not the same requirement.
Likewise the +/-0.03 layout pitch must not be passed off as the tolerance of
the delivered connector pins.

Proposed finished-pin limits:

```text
KF128 E: width <=1.10, thickness <=1.00
         diagonal = sqrt(1.10^2 + 1.00^2) = 1.486607
KF129 E: width <=1.15, thickness <=1.00
         diagonal = sqrt(1.15^2 + 1.00^2) = 1.523975
```

The KF129 envelope covers the larger of the conflicting nominal widths plus
the printed small-dimension tolerance band. These are not promises that an
uninspected allocation meets them. Check the widest insertion section, not
just the tapered tip. Do not clip, grind or squeeze pins into compliance.

Body projections also need tolerance stacking, not just a larger total depth:

```text
KF128 rear max = 5.20 + 0.20 = 5.40
      front max = (10.50 + 0.50) - (5.20 - 0.20) = 6.00
KF129 rear max = 4.90 + 0.20 = 5.10
      front max = (10.60 + 0.50) - (4.90 - 0.20) = 6.40
```

Neither sheet independently dimensions every end-face-to-pin datum. The
pin-row-relative body boxes below are therefore explicit **E acceptance boxes**,
including the end keys, rather than an assertion of exact body centring from
the drawing alone. Their row half-extents are based on half the toleranced
main length plus the entire maximum end key: `23.36/2 + 0.80 = 12.48` and
`10.66/2 + 0.75 = 6.08`, rounded outward to 12.50 and 6.10. Inspect both ends
relative to the actual pin-pattern datum, not only the total body length.

### Axial Parts

| Exact identity | Visually resolved dimensions | Finished-pin design treatment |
| :--- | :--- | :--- |
| **Historical, retired:** Vishay MBE04140C2201FC100 | p13's `d_nom = 0.80` is the round wire diameter. `D_max = 4.20` is body diameter; `L_max = 11.90` body length; `l_min = 31.0` each unformed lead; `M_min = 15.0` mounting pitch. | Former **E <=0.90 diameter**, including tin finish, roundness and forming distortion, was a nominal +0.10 design limit, not a Vishay guarantee. No current R1/R2 insertion or forming task. |
| **Historical, retired 2026-09-14:** Bencent B5G470L | p2 lead is explicitly round, diameter **0.80**, with no +/- or maximum qualifier. A=62 +/-2 is unformed overall length; B=6 +/-0.20 is body length; C=diameter 5.50 +/-0.20 is body diameter including the end-electrode outline. Copper leads, matte-tin finish are stated. | **E <=0.90 diameter**, for the stated procurement rationale. A/B/C tolerances do not create a tolerance on the separate 0.80 lead callout. Former 1.20 holes passed diameter-only against this E, but not the complete fixed-pattern budget below; then-selected holes were **1.40**. No current AC insertion task. |
| Ruilon 2R470TD-8 | TD figure in both revisions: lead diameter **1.00 +/-0.05**; body diameter **8.00 +/-0.20**; axial body length **6.00 +/-0.30**; unformed overall length **62 +/-2**. | Drawing-derived maximum **1.05 diameter**. Require the finished insertion section to remain <=1.05 after forming too; enlarged bends/burrs must not enter the barrel. THT finish is nickel plated in the retrieved manufacturer text. |

The Ruilon A6 version-history text dates its A3 entry 2023-03-31, whereas the
distributed A3 dimension sheet prints 2023-11-02. This does not change the
visually matching mechanical numbers, but retain the exact applicable file/lot;
do not merge electrical or temperature claims across revisions.

Where a metric and a rounded inch body limit differ slightly, the proposed
library bounds below round **the larger converted upper value** outward:

| Body dimension | Metric upper | Inch upper converted | Proposed bound |
| :--- | ---: | ---: | ---: |
| Historical Bencent diameter | 5.700 | (0.217+0.008) x 25.4 = 5.715 | 5.72 |
| Ruilon TD diameter | 8.200 | (0.315+0.008) x 25.4 = 8.2042 | 8.21 |
| Ruilon SMT end-face A/B | 5.200 | (0.197+0.008) x 25.4 = 5.207 | 5.21 |

These small outward roundings avoid needing a controlling-unit assumption for
body clearance. They are not new manufacturer dimensional tolerances. Ruilon's
1.05 metric lead upper limit is already larger than the converted inch upper
limit, `(0.039+0.002) x 25.4 = 1.0414`.

## Hole Recommendations

All hole sizes here are **nominal finished component PTH dimensions**, not
unplated tool diameters. Use ordinary round holes, not press-fit or slots.
The first table is the **historical 97e202d diameter-only screen**, not the
current hole schedule. The adopted Kefa/earth-GDT position budget follows it,
with the retired AC case explicitly labelled; current R1/R2, D1-D4 and GDT_AC
have no holes.

```text
H_min = H_nom - 0.08
D_pin = finished round diameter, or sqrt(W_max^2 + T_max^2)
Diameter-only requirement: H_min >= D_pin + 0.10
Nominal ring = (minimum pad width - H_nom) / 2 >= 0.254
```

| Part family | 97e202d hole | H_min minus design pin envelope | Diameter-only minimum on a 0.10 mm hole grid |
| :--- | ---: | ---: | ---: |
| KF128, E diagonal 1.486607 | 1.40 | -0.166607 | 1.70 |
| KF129, E diagonal 1.523975 | 1.30 | -0.303975 | 1.80 |
| MBE0414, E diameter 0.90 | 1.00 | 0.020000 | 1.10 |
| B5G470L, E diameter 0.90 | 1.20 | 0.220000 | 1.10 |
| 2R470TD-8, diameter 1.05 | 1.20 | 0.070000 | 1.30 |

The first two negative results are against the **proposed conservative E**,
not a claim that every nominal connector fails to enter the old board.
Nominal KF128 diagonal is 1.204159, leaving 0.115841 in that former worst hole,
only 0.015841 beyond the required allowance before any pin tolerance. KF129's
smaller nominal diagonal is also 1.204159, leaving **0.015841 total** in its
1.22 worst hole; the larger nominal diagonal is 1.241974 and exceeds that hole.

### Independent Position Budget

The last column above is **not** a complete insertion recommendation. A 0.10
diametral assembly allowance cannot also pay for arbitrary pitch error.
JLCPCB publishes hole position tolerance +/-0.05. Conservatively treating that
as +/-0.05 on each board axis gives radial `e_h = sqrt(2)*0.05 = 0.070711`.

The retained selected Kefa/earth-GDT ordinary-process geometry follows, with a
**separately controlled part-pattern limit `e_p <=0.050 mm radial` per pin**.
This limit applies after one common rigid alignment of the complete pin pattern
to the nominal footprint, through the full insertion length. It includes
non-collinearity, lean and forming errors, not just adjacent pitch. It is an
incoming/formed-part inspection condition, **not a Kefa/GDT guarantee**.

```text
Additional diametral position budget = 2*(e_h + e_p) = 0.241421
Require H_nom - 0.08 - D_pin - 0.241421 >= 0.10
```

| References | Selected hole / retained pad size | Diameter-only clearance | Clearance after separate position budget | Nominal ring |
| :--- | :--- | ---: | ---: | ---: |
| J_IN, J_EARTH | **2.00 / 3.20** | 0.433393 | 0.191972 | 0.60 |
| J_LED_A, J_LED_C | **2.00 / 2.80** | 0.396025 | 0.154604 | 0.40 |
| **Historical GDT_AC / B5G470L, retired 2026-09-14** | **1.40 / 2.80** | 0.420000 | 0.178579 | 0.70 |
| GDT_A_E, GDT_B_E, GDT_C_E | **1.50 / 3.00** | 0.370000 | 0.128579 | 0.75 |

**2026-09-14 applicability erratum:** the AC row preserves the former hole/ring
case unchanged, not an SMT fit requirement. The current
[hole schedule](ASSEMBLY.md#hole-fit-evidence) includes only Kefa and earth GDTs.
For those retained parts this is the conservative **bounded THT design**, not a
requirement to enlarge every hole this much regardless of actual part evidence.
It deliberately trades more solder volume and fixture dependence for insertion
margin without requiring tighter JLCPCB fabrication tolerances. The retained
Kefa/earth-GDT pad shapes, centres, nets and copper dimensions remain unchanged. The
minimum ring is 0.40, above 0.254. Nominal rings are not guarantees of finished
registration, etch tolerance, solder fill or barrel copper.

Smaller holes are supportable only with an independently demonstrated combined
alignment bound `e_h + e_p <= (H_nom - 0.08 - D_pin - 0.10)/2`, or an accepted
forming process that fits the measured actual board pattern. Do not claim that
1.70/1.80 connector holes accommodate the broad general pitch bands on the
Kefa drawings. Conversely, screening an ordinary lot to the explicit E/pattern
limits is a legitimate alternative to waiting for a new manufacturer guarantee;
do not claim the screen has already passed or that its yield is known.

For the retained 15.24-pitch axial earth GDTs, the radial part-pattern bound limits
two-pin spacing error to at most 0.10. Inspect the actual formed pattern and
accepted standoff/height after seating; larger holes must not permit collapse or tilt.
The minimum-hole proof covers neither ceramic-seal bending stress nor pullout.

## Body Geometry

Implementation coordinates in this table are **local footprint coordinates**,
using the existing origins/rotations and the two distinct LED pad mappings.
Body boxes include electrodes, moulding projections and end keys, but not the
entire unformed lead length. Retain reference/polarity/lead graphics as needed.
Use the complete [local/global LED mappings](ASSEMBLY.md#placement-and-polarity),
including stored pad angles. Body-outline changes do not authorize pad-position,
pad-angle or net changes.

Selected assembly control: the actual projected body must remain inside its
listed body box expanded by **0.10 on each side**, including translation and
tilt. This is an inspected projection bound, not permission to add arbitrary
rotation on top of the allowance. Courtyards contain that projection plus at
least 0.25 assembly margin, and existing pads plus 0.25 where pads dominate.

| Footprint family | Selected F.Fab body/envelope box: X; Y | Selected F.CrtYd box: X; Y |
| :--- | :--- | :--- |
| KF128 Input and Earth | **-6.00..5.40; -12.50..12.50** (E) | **-6.35..5.75; -12.85..12.85** |
| KF129 LED A and C | **-5.10..6.40; -6.10..6.10** (E) | **-5.45..6.75; -6.45..6.45** |
| TE 3521 prototype SMT resistor, retained alternate lands | **-3.225..3.225; -1.70..1.70** | **-4.05..4.05; -2.10..2.10** |
| **Historical B5G470L north-south overpass, retired 2026-09-14** | **-2.86..2.86; -3.10..3.10** | **-3.25..3.25; -9.30..9.30** |
| 2R470TD-8 east-west | **-3.15..3.15; -4.105..4.105** | **-9.40..9.40; -4.46..4.46** |
| SMD5050-470NA north-south electrode axis | **-2.605..2.605; -2.25..2.25** | **-3.00..3.00; -3.75..3.75**, retained |

These selections do not conceal interference by shrinking courtyards. The
Ruilon SMT-GDT body's shorter Y follows its resolved axial C dimension; its
courtyard Y is deliberately retained. TE's maximum body fits the existing
explicit envelope; the retained alternate lands are not TE's recommended pattern.
Preserve protected vias, rails, earth copper,
mounts and LEDs; native file verification and actual assembly acceptance remain
different checks.

**2026-09-14 applicability erratum:** the B5G470L body/courtyard row is historical.
The following checkpoint-placement calculations are preserved, **not a new DRC
run**: the AC-related **0.05/0.17** gaps apply only to the old overpass. Use
[Westward Clearance Evidence](#westward-clearance-evidence) for the current
1.2.1-dev SMT-GDT placement. The **4.75 J_IN gap** below also belongs to the
earlier AB/BC placement; it is now **0.25**. Retained Kefa/earth-GDT envelope,
overhang and body-gap controls still apply.

**2026-09-15 mechanical applicability erratum:** the LED/mount and J_EARTH
edge calculations in this checkpoint list apply to the **old 63.00 x 56.00
outline, east edge X=160.00 and H2/H4 centres X=155.50**. Preserve their
**0.10 LED/mount gap and 1.30 conditional overhang** as historical evidence;
[East Board Extension](#east-board-extension) records the new margins. The
retained body/pose envelopes and earth-GDT body-gap controls are unchanged.

- J_IN courtyard east becomes X=111.75; SMT west is X=116.50: **4.75 gap**.
- SMT east becomes X=122.50; overpass west is X=122.55: **0.05 gap**.
  This is a small drawing-space margin, not demonstrated rework access.
- Overpass east is X=129.05; earth-GDT west is X=129.22: **0.17 gap**.
- Earth-GDT courtyard height is 8.92 on the preserved 9.00 pitch: **0.08 gap**.
  With an 8.21 body bound and the stated 0.10 projected displacement allowance
  for each neighbour, physical body gap is at least
  `9.00 - 8.21 - 2*0.10 = 0.59`. This is **not a 1.00 mm air-gap guarantee**,
  nor an impulse-insulation qualification. Inspect the full bodies/electrodes.
- LED courtyard global X is **139.05..151.95**. The protected H2/H4 courtyard
  west boundary was X=152.05: **0.10 gap** with the old mount positions.
  LED A global courtyard Y is **96.25..108.45**; LED C is **136.55..148.75**.
  No pad/net remapping or
  connector rotation change is needed.
- At unchanged J_EARTH=(155.00,122.50), 180 degrees, the controlled E body envelope
  reaches X=161.00 before pose allowance, or **161.10 after it**. With the old
  nominal edge X=160.00, the pre-pose body overhang was **1.00**. The former
  **CONDITIONAL 0.20 inward-route allowance** put the edge at **159.80**, requiring
  **1.30 overhang including pose**, not the former nominal 0.30. That allowance
  was not an accepted supplier tolerance or a guaranteed manufactured margin.
  Its courtyard reaches X=161.35. The old panel/routed-spacing and COMBI review
  needed that full envelope, not trimmed bodies/courtyards or shifted earth copper.

The Kefa maximum body heights are 14.60 and 18.80 above their seating planes;
seat standoff and solder/lead protrusions are separate. Assuming flush seating
and the standard 1.44..1.76 board-thickness range, untrimmed lead protrusion is
2.24..3.16 for KF128 and 2.74..3.66 for KF129. These calculations do not approve
the support/enclosure fit or the assembler's trimming process.

### East Board Extension

**2026-09-15, hardware 1.2.1-dev: user-approved mechanical update, not a native,
CAM or hardware PASS.** The staged PCB expands only the east edge **2.00**, from
**X=160.00 to 162.00**, and moves H2/H4 **2.00 east**. This is distinct from the
rejected eastward GDT proposal; the approved westward GDT/via placement remains.
All copper, vias and electrical components stay in place. Local lands,
body/courtyard shapes, drill sizes, stackup, population and part/datasheet evidence
are unchanged; no fresh manufacturer retrieval or supplier acceptance is implied.

- Board outline is now **65.00 x 56.00**, from **(97.00,94.50) to
  (162.00,150.50)**; the west, north and south edges are unchanged.
- **H2=(157.50,99.00), H4=(157.50,146.00)** replace their former X=155.50
  positions. **H1=(101.50,99.00), H3=(101.50,146.00)** remain. All four centres
  are nominally **4.50 from their adjacent edges**; **3.20 NPTH**, 6.40 collar
  markings and **3.45-radius front/back mechanical courtyards/copper keepouts**
  are unchanged.
- J_EARTH remains **(155.00,122.50), 180 degrees**. Its existing controlled E
  body maximum is **X=161.00**, **161.10 including 0.10 projected pose**, and its
  retained courtyard maximum is **161.35**. These are the existing project
  envelopes, not new manufacturer maxima or accepted-lot measurements.

| Relationship | Current nominal or conditional arithmetic, mm |
| :--- | :--- |
| Posed body to nominal east edge | `162.00 - 161.10 = 0.90` |
| Courtyard to nominal east edge | `162.00 - 161.35 = 0.65` |
| Posed body with **CONDITIONAL 0.20 inward-route allowance** | Assumed edge `162.00 - 0.20 = 161.80`; `161.80 - 161.10 = 0.70` |
| Courtyard with the same conditional allowance | `161.80 - 161.35 = 0.45` |
| LED courtyard to H2/H4 courtyard west bound | `157.50 - 3.45 = 154.05`; `154.05 - 151.95 = 2.10` |

The former **0.20 inward-route allowance remains CONDITIONAL**, not an accepted
supplier outline tolerance. Neither the nominal **0.90/0.65** nor conditional
**0.70/0.45** establishes guaranteed manufactured margins. Nominal envelope
containment replaces the old drawn overhang, not outline/edge/hole-position,
allocated-part/pose, panel/clamping/depanelization or enclosure/support/tool-fit
acceptance. Use [Earth Terminal Edge Clearance](ASSEMBLY.md#earth-terminal-edge-clearance)
for the canonical extents and local acceptance duties; do not trim envelopes,
move copper or assume a courtyard is sufficient cutter clearance.

All **C4/C5/W3/W1/W4** holds remain open and whole-BOM **`allocation_verified`
remains `false`**. A fresh source-matched artifact snapshot is required; earlier
checks and packages do not verify this mechanical or controlled-note change.
Supplier/order and received-board qualification remain separate from Gate P
files. This entry records the approved geometry and arithmetic, not fresh native
checks, processed CAM, a physical fit result or hardware approval.

### Overpass Control

**HISTORICAL, retired 2026-09-14: B5G470L only.** The requirements and arithmetic
below record the former unqualified overpass, not current SMT instructions or
current forming holds. The complete [historical drawing and method](ASSEMBLY.md#gdt_ac-forming-drawing)
remain available; the [SMT AC crossover](ASSEMBLY.md#smt-ac-crossover) replaces
this construction without closing physical protection/insulation qualification.

Keep GDT_AC at X=125.80, north-south, pad Y=114.88/130.12, pitch 15.24.
The whole raised body/electrode/lead span must retain **>=2.00 above the highest
finished PCB surface** before encapsulation, as ASSEMBLY.md requires. A
candidate fixture target is body underside **2.50 +/-0.25**, with the complete
assembled projection limited to **8.50 maximum height**: 2.75 + 5.72 = 8.47
for the body alone. Inspect the actual complete span; the body-only calculation
does not account for an upward lead bow or a low bend.

The 15.14 minimum formed pitch and 6.20 maximum body leave 4.47 per end before
body offset and bend geometry. This establishes available geometric room, not
an approved bend radius or seal setback. Manufacturer/assembler limits on seal
support, bend radius, springback and soldering remain specific open facts.
Gel does not preserve an air gap or replace insulation qualification.

## SMT Land Resolution

**2026-09-14, 1.2.1-dev applicability:** the reviewed local pattern/body/process
evidence still applies to **AB, BC and AC** without a footprint change. Current
AB/BC global coordinates are updated below; the old via proof is explicitly
historical. Four-land and paste-area comparisons remain specific to **AB/BC**,
not a claim that AC was always SMT. Current AC coordinates and component-hole
clearances are in [Westward Clearance Evidence](#westward-clearance-evidence).

In both original **SP-GDT-006 A3 / 2024-08-19 p3** figures:

- **X=1.2** spans the width of one narrow rectangular land, along the tube axis.
- **X1=4.0** runs between the dashed centre lines of the two lands.
- **Y=5.5** spans the long dimension of each land, transverse to the tube axis.
- A/B=5.0 +/-0.2 describe the **square end face**, not a 5 x 5 plan body with
  4.2 height. C=4.2 +/-0.3 spans the axial length including end electrodes;
  D=0.5 +/-0.1 describes one end-electrode thickness.

The conversion conflict is substantial, not ordinary display rounding:

```text
4.000 mm / 25.4 = 0.157480 in, not 0.165 in
0.165 in * 25.4 = 4.191 mm
```

The original manufacturer file repeats the contradiction; there was no public
correction in the retrieved exact-MPN source. **The printed metric 4.00 mm
spacing is explicitly selected**, not an inferred manufacturer erratum. The
duplicated 0.165 also appears as the correct rounded inch value for C=4.2 in the
same table, which is consistent with a copied conversion error, but does not prove
the manufacturer's intended correction. Do not average the numbers, silently
choose a 4.2 pitch, call X1 a gap, or claim written approval.

Retained selected footprint geometry, preserving pad numbers and nonpolar part
orientation:

| Pad | Local centre | Copper / nominal mask / nominal paste rectangle |
| :--- | :--- | :--- |
| 1, north | **(0,-2.00)** | **5.50 X x 1.20 Y**, F.Cu/F.Mask/F.Paste |
| 2, south | **(0,+2.00)** | **5.50 X x 1.20 Y**, F.Cu/F.Mask/F.Paste |

Use zero extra mask/paste margins as the source baseline; no custom stencil
process is implied. Inner land gap is **2.80**, outside span **5.20**, width
**5.50**. At the **1.2.1-dev AB/BC origins X=115.00**, their four lands have
**X=112.25..117.75**, moved west from the 1.2.0-dev X=116.75..122.25. Y is unchanged:

| Part / pad | Global Y bounds |
| :--- | :--- |
| GDT_AB / 1 | 116.09..117.29 |
| GDT_AB / 2 | 120.09..121.29 |
| GDT_BC / 1 | 123.71..124.91 |
| GDT_BC / 2 | 127.71..128.91 |

The metric body/electrode limits give at least 0.40 axial overlap of each
electrode with its land at nominal placement, also with up to +/-0.10 axial
translation when evaluated over C=3.9..4.5 and D=0.4..0.6. This is a geometric
contact check, not a solder-fillet or paste-volume qualification. Transverse
body maximum 5.21 plus +/-0.10 placement fits inside the 5.50 land width.

**Keep the current AB/BC 3.20-wide connection-stub endpoints** at
(115.00,116.19), (115.00,121.19), (115.00,123.81), (115.00,128.81).
Only X changed from 119.50 in 1.2.0-dev; Y, F.Cu layer and width are retained.
They still overlap the lands with a full-width incoming section. Do not
blindly extend these wide round-ended tracks to the new pad centres: their
inner copper ends would then leave only 0.80 between opposite nets. Keeping
the old endpoints preserves their existing **1.80 masked-copper gap** beneath
each AB/BC tube. The 2.80 figure above is the **land/mask/paste gap**, not the minimum
gap of all connected copper. Preserve mask over the extra stub copper and
inspect the processed mask and stencil; no solder bridge may reduce the
insulation distance beneath the arrester.

**Historical metric-land/via proof, retained through 1.2.0-dev:** the closest
protected via was X=115.50 on each adjacent rail, with AB/BC land west edge
X=116.75. That land corner gave dx=1.25 and dy=1.21:

```text
corner distance = sqrt(1.25^2 + 1.21^2) = 1.739713
to full nominal 1.00 drill circle         = 1.239713
to full nominal 1.80 copper/mask opening  = 0.839713
```

That metric-land selection allowed untenting without moving/shrinking vias or
filling them to cure the former SMT collision. The **1.2.1-dev westward
placement changes those distances**, not the historical proof; use the
[current via/J_IN gaps](#westward-clearance-evidence). If CAM expands apertures
or changes drills, subtract those actual changes and registration allowances
and recheck all six current lands. The historical AB/BC area change per source
paste land was from 10.40 to the retained **6.60 mm^2**, a
**36.54% reduction at equal stencil thickness**. JLCPCB generates its processed
stencil using its own component rules, not necessarily these raw F.Paste
rectangles. This does not specify the actual deposited solder volume.

## Standard Process

The authorized baseline is ordinary **two-layer FR-4, 2 oz on both sides,
nominal 1.6 mm, ENIG**, with green mask a standard choice. Nothing in these
recommendations needs epoxy/copper filling, reliable 1 mm tenting, press-fit
holes, heavier barrel plating by assertion or a special CAM concession.

| Primary public evidence, retrieved 2026-09-07 | What it actually establishes |
| :--- | :--- |
| [Via covering][jlc-via], updated 18-Aug-2026 | Untented vias have no special process requirements; exposed copper receives the selected finish, including ENIG. The <=0.5 mm covering recommendation applies to the other treatments, not untented vias. Untented vias are wettable; solder ingress/beads remain possible. |
| [Pad/via hole tolerance][jlc-holes], updated 24-Apr-2025 | Ordinary component holes: +0.13/-0.08; use pin diagonals and metric one-decimal hole sizes. Ordinary via diameter is **not controlled** and may be adjusted in production. |
| [Rigid PCB capabilities][jlc-pcb], live table | Two-layer 2 oz and ENIG offered; hole position +/-0.05; two-layer/2 oz component PTH ring >=0.254; 1.6 thickness +/-10%; 18 micrometres **average**, not minimum, hole plating. Mask can be 1:1 following the June-2025 LDI update; 2 oz mask bridges require 0.20. |
| [PCBA capabilities][jlc-pcba], live table | Mixed SMT/THT offered in both service tiers. Standard PCBA needs 70 x 70 minimum processing size and rails; Economic lists applicable 1.6/green/ENIG options. These are not allocation or exact 2 oz assembly-quote acceptance. |
| [Stencil preparation][jlc-stencil], updated 16-May-2026 | Stencil apertures are generated from verified production/component data, not simply copied from the customer's paste Gerber. Normally only selected SMT parts receive apertures. |

Adopted via implementation: explicitly **untent all fourteen on both
sides**, with nominal **1.80 circular F.Mask/B.Mask openings**, no via F.Paste,
and select the standard **Untented, no fill/plug/cap** order option. This replaces
the checkpoint's global front/back tenting request. Preserve **1.00 drill / 1.80
copper** at every location in the
[coordinate/function schedule](ASSEMBLY.md#stitching-via-identification).

Use coordinate/function identification, never a fill-by-diameter instruction.
Keep all component holes open. Review ordinary production files for preservation
of the fourteen 1.00 nominal drills and unchanged copper; reject an unapproved
CAM reduction rather than accepting it as an implementation detail. Public
standard-via guidance does **not** guarantee a 1.00 finished diameter/tolerance.
Any contractual finished-via minimum beyond standard service
remains a separate unresolved supplier fact, not authority to order special
processing. An untreated via is not a sealed environmental barrier.

The PCBA FAQ says unused through-holes are protected during wave soldering, but
that is not a coordinate-specific promise for these exposed stitching vias.
Inspect solder ingress, loose beads, hole fill, wetting and cleanliness on actual
boards. Do not depend on fill or mask opacity to make a process acceptable.
Retain the [protected rails/returns](ASSEMBLY.md#physical-guardrails) and solid
earth bus, including **exactly 6.00 rear B** and the **1.2.1-dev front-B stop
at X=115.00**, rather than the former all-3.20 dual-layer B geometry.
No thermal spokes, slits or drill reduction to ease soldering.

The published PCBA reflow table gives Economic 255 +/-5 degrees C and Standard
240 +/-5 degrees C, whereas SP-GDT-006 lists a 260 +0/-5 peak profile. Those
numbers are not interchangeable evidence of an accepted joint/body profile.
Select an ordinary supported assembly service whose actual profile is suitable;
do not presume a special profile is authorized. The 2 oz thermal load, actual
alloy/flux, THT sequence and formed GDTs still require process evidence.

## Independent Acceptance

The E limits make a bounded design possible; **no actual lot or sample was
measured in this research**. A normal procurement inspection can control them
without pretending that the manufacturer guarantees a new dimension.
These are supplier/order and physical-acceptance controls, not additional
qualification prerequisites for prototype artifact generation. Later enclosure,
thermal and protection activities stay separate from the board file workflow.
Current insertion checks apply to Kefa and the **three earth GDTs**; forming
applies only to those earth GDTs, not the retired B5G470L. All three inter-core
tubes instead need the selected SMT-land, seating and stencil/profile acceptance.

1. Record the adopted finished-pin/body/pattern limits and exact
   drawing/MPN/lot on the procurement and assembly traveller. Obtain an ordinary
   allocated-lot dimensional report or inspect independent actual samples
   before relying on the envelope for the prototype order. Do not approve an
   unallocated catalogue photo or supplier CAD model as this evidence.
2. For the five-board baseline, inspect **every allocated part** in the
   controlled-envelope families, including spares used in assembly. Measure
   both rectangular axes at their largest insertion section and enough axial
   wire orientations to bound ovality. Include plating, burrs and uncertainty:
   accept an upper limit only when `measured maximum + uncertainty <= limit`.
3. Independently measure the complete pin pattern through the insertion depth,
   using a calibrated optical fixture or suitable metrology. Confirm the
   separate 0.050 radial per-pin envelope, not just one nominal pitch. Formed
   earth GDTs are inspected after forming; R1/R2 and all inter-core GDTs are
   undrilled SMT. A tight nominal gauge that forces leads into place is not a
   valid inspection.
4. Check insertion with a dimensional fixture representing the chosen minimum
   finished holes and the accepted pattern budget, then on the actual boards.
   Record free insertion, seating, body projection, lead protrusion and accepted
   earth-GDT standoff/height. Never ream plated boards or force ceramic seals
   to fit. Larger-hole solder fill/workmanship must be accepted independently.
5. Measure body/end-key extents relative to pin-pattern datums and verify the
   proposed projected-body boxes, neighbour gaps, mounting keepouts and
   [J_EARTH edge clearance](ASSEMBLY.md#earth-terminal-edge-clearance) against the
   revised outline/mounts and accepted actual tolerances. Record the measurements
   and uncertainty; nominal/conditional margins are not accepted supplier limits.
   Inspect J_IN seating and solder/beads around the moved rail
   vias under its projection, and the reduced **0.25 courtyard gap** to AB/BC;
   nominal drawing space is not a physical-fit result.
   Perform the complete unpotted COMBI/WAGO/support/LED dry-fit,
   including screwdriver access and lid travel, before encapsulation.
6. Inspect processed copper/mask/paste/drills and actual SMT fillets. Keep the
   manufacturer's below-arrester insulation space free of solder. Inspect
   untented vias and do not treat gel as a seal or the drawing as surge proof.
   Retain the unpotted reference and distinguish workmanship from P2/P6
   electrical, thermal, environmental and powered-recovery qualification.
7. Accept the rear different-core finished-etch clearance and associated CAM
   tolerances for the new crossover. **3.02 nominal is not a guaranteed 3.00
   finished gap**; neither is the selected **3.20 front inter-GDT pad gap**.
   Compare full shapes, retained front GDT_B_E.1 pad and all
   six SMT-GDT apertures; preserve the [approved takeoff/cutback geometry](ASSEMBLY.md#smt-ac-crossover).

### Remaining Supplier Facts

| Party / part | Precise fact still needed; what no longer needs rediscovery |
| :--- | :--- |
| Kefa / C474957 and C475092 | Which controlled KF129 A/21.03.13 pin-width variant is actually supplied: 0.90 or 0.95? What finished metal-pin tolerances, plating/burr inclusion, pitch/non-collinearity and pin-to-body datums are guaranteed? The rectangular axes, body projections, end keys and drawing general-tolerance bands **have been read**. Adopted E limits plus independent lot acceptance can replace an absent tighter guarantee for that limited lot, not for all future purchases. |
| TE Connectivity / 35212K2FT / C4129105 | Exact prototype identity resolved; ten fitted parts plus attrition still need quote/job allocation. TE p2 body/bands and p3 recommended lands/reference PCB have been read. Accept the **retained alternative 1.35 x 3.70 lands at 6.25 pitch**, actual supplier model/placement, stencil and solder process under W4; W3 thermal transfer to the project's two-layer mounting remains conditional. Do not treat catalogue P70 or the family overload ceiling as assembled qualification. |
| Yageo / SR2512FK-7W2K2L / C876850 | Identity confirmed, not current prototype population or allocation. Independently accept applicable manufacturer evidence/model, footprint/placement, stencil/solder process and thermal performance, then review the source/BOM update before a Yageo build. |
| **Historical, retired 2026-09-14:** Bencent / B5G470L | Finished 0.80-wire tolerance and allowable forming/seal-support geometry were not accepted. Public p2 really contains a round 0.80 callout without its tolerance. A2 body limits were resolved; the then-current manufacturer download did not supply a newer toleranced lead drawing. The <=0.90 E/forming controls are retained evidence, **not current procurement or assembly tasks**. |
| Ruilon / 2R470TD-8 | Exact revision/production code allocated; allowed bend radius/seal setback, post-forming lead condition and ordinary nickel-lead solder process. The 1.05 lead maximum and 6.30/8.20 metric body maxima are **resolved in both drawings**, not unreadable. |
| Ruilon / SMD5050-470NA | **All three inter-core tubes:** formal resolution of X1=4.0 mm versus 0.165 in, preferably a corrected controlled drawing; actual supplier model, processed stencil, seating and joint/profile acceptance. Figure association and the selected metric-based implementation are resolved here, without claiming manufacturer correction or approval of the old 5.2 x 2 alternative. Five boards require **15 fitted parts plus supplier-defined attrition**, not an established purchase/allocation. [MATERIALS](../MATERIALS.md) owns procurement history (**repository-only**). |
| JLCPCB / actual assembly | Ordinary-service part allocation, retained drill data, processed mask/stencil, fitting/lead-forming capability, real solder profile and workmanship. Accept the [revised outline/mounts and J_EARTH edge/panel/fit envelope](ASSEMBLY.md#earth-terminal-edge-clearance), including actual edge/hole-position tolerances and panel/depanelization clearances. Standard untented fabrication does not require a 1 mm fill exception. Any required finished-via/barrel minimum beyond published standard guarantees remains a separate design/supplier decision, not implicitly approved special processing. |

## Verification Scope

These dated records apply only to their named snapshots. Reorganizing this note
does not revalidate an older package or report a new native/hardware result.

**Original 97e202d research record:** read AGENTS.md, all of REMEDIATION.md and
ASSEMBLY.md; inspected the then-current BOM, relevant local footprints and
routing without editing them. Original figure access and primary web evidence
are identified above. The stated diagonals,
hole/position/ring budgets, body conversions and SMT clearances were checked
with a calculation-only `python3 -B -c` invocation using `math.hypot`; it did
not read/write project files or access the network. No KiCad checks or physical
tests were run, and no release hold is closed by this record.
`git diff --no-index --check /dev/null pcb/DFM_EVIDENCE.md` passed as a
documentation whitespace check, not a hardware gate.

**02661d8 read-only review:** the source geometry check and 60 geometry tests
passed; retained native XML/IPC/CPL/BOM/Gerber/drill data matched the reviewed
PCB/schematic hashes, and the retained assembly PDF was inspected. Those results
described the former roundrect resistor lands, **not a validation of the selected
rectangular correction**. The manufacturer/body and C-code findings above were
not disproved by internal file consistency. In-memory probes also showed missing
resistor angle/aperture guards and a body/courtyard test that no longer iterated
R1/R2; the parent owns the checker/test corrections.

**Historical 2026-09-08 PS documentation integration edited only ASSEMBLY.md and DFM_EVIDENCE.md.**
The parent owns CAD/libraries/BOM/sourcing metadata, diagnostic review, checker
changes and integrated verification. No shared Make/native workflow, source
synchronization, supplier request, upload, order, commit or physical test is run
by this documentation task. Publish only source-matched artifacts under the
explicit prototype/production distinction; do not refresh approval hashes or
claim supplier/performance acceptance from this evidence record.

**Historical 2026-09-11 TE evidence correction edits only ASSEMBLY.md and DFM_EVIDENCE.md.**
It uses the independent original-page review above and the verified C876850
listing, corrects attribution/assumptions and preserves every physical guardrail.
No CAD/library/BOM/model/ledger or generated artifact is edited by this task.
Native/build/workflow/annotation verification remains with the parent; this
documentation correction is not a new native or hardware PASS and closes no hold.

**Historical 2026-09-14, 1.2.0-dev SMT AC documentation integration edits only
ASSEMBLY.md and DFM_EVIDENCE.md.** Read agreed requirements, current holds, physical guardrails
and existing source/evidence. `python3 -B tmp/gdt-ac-6mm-review.py` ran read-only
on the pre-conversion source: the old stem left 2.10 with either rear width;
the approved 6.00 / X=136.50 case left 3.02 rear-core minimum and 3.25 rear
EARTH separation. The helper verified that its source bytes were unchanged.
Other crossover dimensions above record the approved geometry handoff, not an
additional native run or physical measurement. No fresh manufacturer review,
CAD/library/BOM/ledger/approval edit, generated artifact, shared build workflow,
supplier request, upload, order, commit or hardware test is performed by this
documentation task. The parent owns integrated source/native/export checks,
diagnostic review and current results; old PASS records do not verify this change.

Documentation-only checks: `git diff --check -- pcb/ASSEMBLY.md pcb/DFM_EVIDENCE.md`
passed. Reused the existing `tmp/deduplication-review/audit.py` parser/functions
read-only, without its report-writing entry point: **101 local links resolve**;
the flat-note source projection resolves **93**, with **eight explicitly labelled
repository-only root-guide references** separately reviewed. No missing paths,
fragments, parser warnings or removed legacy anchors were found. The original
AC drawing/six-step method and DFM overpass calculations remain byte-identical,
as do the existing TE/PS/HP reviews and assembly resistor/axial history. This is
not an actual package audit, external-URL recheck, native result or hardware test.

**2026-09-14, hardware 1.2.1-dev westward documentation integration edits only
ASSEMBLY.md and DFM_EVIDENCE.md.** Read AGENTS, agreed requirements, issue/release
holds, current handoff and the owned assembly/DFM controls before editing. Read
the old-hash-bound spacing helper without executing or changing it. A
calculation-only `python3 -B -c` invocation using `math.hypot` checked the
new via corner/drill/annulus, inter-GDT and B_E pad/hole, front-B cap, body/pose,
courtyard, J_IN mask/drill and rear-rail dimensions above. It also checked the
rejected east overlaps, exact-mirror west gaps and **19.00 versus 15.50 mm**
last-B-via path. It did not read/write project files or access the network.
No CAD/library/BOM/ledger/approval or generated artifact is edited here. No
shared build/native/annotation/workflow command, supplier request, upload,
order, commit or physical test is run by this task. Integrated verification and
the new source-matched artifact/release record remain with the parent; none of
the preserved earlier results verifies 1.2.1-dev or closes an engineering hold.

Documentation-only verification: `git diff --check -- pcb/ASSEMBLY.md pcb/DFM_EVIDENCE.md`
passed. Reused the existing `tmp/deduplication-review/audit.py` parser/functions
read-only, without its report-writing entry point: **112 local links from the
two owned notes resolve**; their flat-note projection resolves **104**, with
**eight explicitly repository-only root-guide references** separately reviewed.
No missing paths/fragments, parser warnings or removed legacy anchors were
found; both owned notes are ASCII and the audited input reads were stable.
Diff review preserves the prior SMT-conversion dimensions, retired axial
drawing/method, manufacturer data and old native/test results. This is not an
actual package audit, external-URL recheck, native result or hardware test.

## Direct Sources

Exact original URLs behind the linked source tables above:

[te-pdf]: https://www.te.com/commerce/DocumentDelivery/DDEController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
[ps-pdf]: https://www.uni-royal.cn/en/images/userfile/file/1784854235b7c79f8d8a205c5d.pdf
[ps-page]: https://www.uni-royal.cn/en/article.php?id=10109
[ps-jlc]: https://jlcpcb.com/partdetail/C2793873
[ps-lcsc]: https://www.lcsc.com/product-detail/C2793873.html
[ps-distributed]: https://www.lcsc.com/datasheet/C2793873.pdf
[ps-target]: https://datasheet.lcsc.com/datasheet/pdf/72ec9a363d94a6fd0729e3976f9248d5.pdf?productCode=C2793873
[hp-pdf]: https://www.uni-royal.cn/en/images/userfile/file/1784806233a2e6d381ea80b5d9.pdf
[hp-text]: https://r.jina.ai/https://www.uni-royal.cn/en/images/userfile/file/1784806233a2e6d381ea80b5d9.pdf
[hp-page]: https://www.uni-royal.cn/en/product.php?s=High-Power+Thick+Film+Chip+Res
[hp-wrong-lcsc]: https://www.lcsc.com/product-detail/C2791283.html
[hp-wrong-jlc]: https://jlcpcb.com/partdetail/UniRoyalElec-HP122WJ0472T4E/C2791283
[hp-nac]: https://store.nacsemi.com/products/detail?stock=XSJMZ0000010410
[hp-distributed]: https://datasheet.lcsc.com/datasheet/pdf/72ec9a363d94a6fd0729e3976f9248d5.pdf?productCode=C2791283
[hp-search-jlc]: https://jlcpcb.com/parts/componentSearch?searchTxt=HP122WF2201T4E
[hp-control-jlc]: https://jlcpcb.com/parts/componentSearch?searchTxt=HP122WJ0472T4E
[hp-search-lcsc]: https://www.lcsc.com/search?q=HP122WF2201T4E
[k128-page]: https://www.kefaelectronic.com/KF128-7-5-7-62-PCB-Terminal-Block-pd45490974.html
[k128-m]: https://jirorwxhqiillo5p.ldycdn.com/KF128-7.62-aidqiBpqKirRliSqmrqirloj.pdf
[k128-l]: https://datasheet.lcsc.com/datasheet/pdf/2bd9ccda2e0f72df8237e78ea70a6d85.pdf?productCode=C474957
[k129-page]: https://www.kefaelectronic.com/KF129-5-0-5-08-PCB-Terminal-Block-pd47789974.html
[k129-m]: https://irrorwxhqiillo5p.ldycdn.com/KF129-5.08-aidqiBpqKirRljSjorlrqlri.pdf
[k129-l]: https://datasheet.lcsc.com/datasheet/pdf/99269cbb2dd06cf5383cf1cad04f20f7.pdf?productCode=C475092
[vishay]: https://www.vishay.com/docs/28766/mbxsma.pdf
[vishay-pack]: https://www.vishay.com/docs/28721/packaginglinleadres.pdf
[bencent-page]: https://www.bencent.com.cn/index/proinfo/id/35029.html
[bencent-m]: https://www.bencent.com.cn/index/xiazai/name/_upfile_admin_file_20260514_2026051411072672523.pdf.html
[bencent-l]: https://datasheet.lcsc.com/datasheet/pdf/6471acbc3d87a8a4a9e5f7b8a245655d.pdf?productCode=C5337217
[ruilon-tht-l]: https://datasheet.lcsc.com/datasheet/pdf/d0869b141c45d22998b36dee1e5e4d4c.pdf?productCode=C2836978
[ruilon-tht-m]: https://www.ruilon.com.cn/Uploads/pdf/017-2rd-8%20series_a6.pdf
[ruilon-smt-l]: https://datasheet.lcsc.com/datasheet/pdf/ce8e2bf652ab9d180a3e88b2584bb613.pdf?productCode=C39692533
[ruilon-smt-m]: https://www.ruilon.com.cn/Uploads/pdf/06-smd5050%20series_a3.pdf
[ruilon-page4]: https://www.ruilon.com.cn/taociqitifangdianguan/list/40-4.html
[ruilon-page5]: https://www.ruilon.com.cn/taociqitifangdianguan/list/40-5.html
[jlc-via]: https://jlcpcb.com/help/article/pcb-via-covering
[jlc-holes]: https://jlcpcb.com/help/article/difference-and-tolerance-explanation-between-via-and-pad-holes
[jlc-pcb]: https://jlcpcb.com/capabilities/pcb-capabilities
[jlc-pcba]: https://jlcpcb.com/capabilities/pcb-assembly-capabilities
[jlc-stencil]: https://jlcpcb.com/help/article/smt-stencil-data-prepared-for-smt-orders
