markshuttle/dogfence-pcb/pcb/ELECTRICAL.md

# Electrical Engineering Record

**Revision: 1.2.1-dev. User-approved westward GDT/via relocation recorded 2026-09-14. Electrical release HOLD.**

This record describes the implemented circuit, DC solver and fault interpretation.
[DESIGN_BOUNDS](DESIGN_BOUNDS.md) owns detailed current parametric screens;
[BOM.csv](BOM.csv) and [Reviewed Components](ASSEMBLY.md#reviewed-components)
identify the **16-part TE 35212K2FT / BYG23T prototype population**. The model
does not cover the unpopulated Yageo SR2512FK-7W2K2L / C876850 production variant;
its own part/model/process/thermal review and controlled source updates are
required before substitution. TE results do not qualify Yageo.

**A negative shunt is not a universal LED pulse-current limiter; powered-GDT/
source protection remains unresolved.** C4/C5/W3 performance and W1/W4 part/
process holds remain open in [verification.json](verification.json), deferred
only for file-verified prototype artifacts, not closed for production/field use.
[Artifact controls](ASSEMBLY.md#prototype-artifacts) distinguish files from
supplier acceptance and hardware qualification; no switch/environmental or
physical-test prerequisite is added to Gate P. Native/file verification requires
the current matching reports and artifact snapshot; earlier PASS results apply
only to their recorded source/note hashes. The normal DC model/scripts and TE
thermal screens are unchanged. Verifying those calculations or this note does
not qualify the changed physical construction.

The original axial hybrid followed **ad282e3**; later SMT selections and the
**1.2.1-dev** spacing change retain its topology. **One LRS-75-36 serves TEST; the other is a
disconnected spare**, not combined capacity. No physical switch pinout or
powered-GDT shutdown is implemented. Section 9 controls the current simple
circuit; older PS12/HP12/PR02/MBE and active/zener/source investigations remain
historical, not required additions. **Energized cattle fencing is prohibited near
the entire boundary cable, stations and hub**; the former close-parallel exposure
is withdrawn, not qualified safe.

Purchases, cancellations and allocation history are maintained in
[MATERIALS](../MATERIALS.md#resistor-procurement-and-history), an optional
**repository-only** reference. Root guides do not ship with the flat set of
seven engineering notes, BOM and verification ledger.

## 1. Implemented Model

The selected indicator circuit is:

```text
WIRE_A -> R1 35212K2FT 2.2k 2W -> D1 A(2), K(1) -> LED_A_POS -> J_LED_A.1
WIRE_C -> R2 35212K2FT 2.2k 2W -> D2 A(2), K(1) -> LED_C_POS -> J_LED_C.1
J_LED_A.2 = J_LED_C.2 = WIRE_B
D3: anode(2) to WIRE_B, cathode(1) to LED_A_POS
D4: anode(2) to WIRE_B, cathode(1) to LED_C_POS
External LED anode goes to terminal 1, cathode to terminal 2.
```

GDT_AB, GDT_BC and GDT_AC connect the named core pairs **before** the indicator resistors. The three core/EARTH tubes connect to the separate EARTH bus. Thus the 2 W R1/R2 do not limit GDT source follow current. R1/R2 are **TE Connectivity 35212K2FT / C4129105**, 2512 SMT, 2.2k, 1%, **+/-100 ppm/C** [S18]. The **25 C resistance reference is a declared engineering model assumption**, not a TE-specified TCR test reference. D1-D4 remain **Vishay General Semiconductor BYG23T-M3/TR / C145454**, 1300 V repetitive reverse / 1 A catalogue rating, SMA [S14]. D3/D4 do not create a forward B-to-A/C path through the intact series diodes. They are not connected before R1/R2 or directly to EARTH.

The approved population has **three SMT inter-core tubes and three THT
core/EARTH tubes**. GDT_AC now selects the same **Ruilon SMD5050-470NA /
C39692533** as AB/BC; all six GDT endpoint connections remain unchanged. The
component evidence [S10,S20,S21] is distinct from system performance:

| Path / population applicability | DC sparkover | Component impulse rating, 8/20 us | Impulse sparkover at 1 kV/us |
| :--- | :--- | :--- | :--- |
| AB/BC/AC, current: Ruilon SMD5050-470NA / C39692533 | 470 V +/-30% (329..611 V) | 5 kA, +/-5 operations | 950 V maximum |
| Core/EARTH: Ruilon 2R470TD-8 | 470 V | 20 kA | Up to 1100 V |
| AC, **historical, retired**: Bencent B5G470L / C5337217 | 470 V +/-20% (376..564 V) | 5 kA, +/-5 operations | 850 V for **99% of measured values** |

For the SMD5050/B5G comparison, both DC entries use **100 V/s**, at delivery,
ionized conditions and **AQL 0.65, inspection level II** [S20,S21]. Ruilon also
specifies **850 V maximum at 100 V/us**; Bencent's **800 V typical distribution
at 1 kV/us** is not its 850 V / 99% entry, and neither is equivalent to Ruilon's
950 V maximum. The change is not a like-for-like sparkover guarantee or an
improved-clamping claim merely because both are nominally 470 V.

Ruilon's **10 kA 8/20 us single operation**, **100 A 10/1000 us, 300 operations**
and **5 Arms, 50 Hz, 1 s, 10 operations** are separate component tests [S20],
not interchangeable pulse shapes, board ratings or required site exposures.
Its **15 V typical arc at 1 A**, **135 V typical glow at 10 mA** and **<0.5 A
glow-to-arc transition** do not specify holding current or extinction. Neither
the Ruilon nor the retired Bencent sheet guarantees recovery on the actual
powered DC fence. Ruilon's reflow profile has a **260 +0/-5 C peak**; its
temporary post-reflow sparkover increase and **24-hour recovery** concern
solder processing, **not powered surge recovery**. Actual profile acceptance
belongs to [ASSEMBLY](ASSEMBLY.md#thickness-and-process) and
[DFM_EVIDENCE](DFM_EVIDENCE.md#standard-process).

Ruilon specifies **<=0.8 pF at 1 MHz** versus the retired Bencent's **<=1 pF
at 1 MHz with 0.5 V bias**; these are not identical test conditions or an
assembled RF-loading comparison. Both specify **>=1 Gohm at 100 VDC**.

These cited test ratings do not establish an assembled surge rating, equal
sharing, powered recovery or cable impulse withstand. **470 V DC sparkover is
not a 470 V transient clamp**; unequal ignition and lead overshoot still matter.
The [SMT AC conversion](#smt-ac-conversion) changes physical discharge/insulation
paths, not the normal DC topology; its [copper screen](DESIGN_BOUNDS.md#ac-conversion-copper-screen)
does not qualify those paths.

The solver uses **same-end TEST: Start A/C positive, Start B negative, all three
End cores individually isolated**. All six ends remain independent; required
ties are **source-side only**, with no permanent End A/C strap, opposite-end B
return or dual-B negative return. No direction selector or normal TEST timeout
is required. TEST/OFF disable RF containment; OFF is not storm isolation.
The provisional eight-pole CA10.A364/WAA364 still needs exact DC interruption
and global transfer approval; no physical terminal numbers or extra poles are
assigned. The complete [INSTALL functional matrix](../INSTALL.md#functional-matrix)
is a supplemental **repository-only** operating reference, not a shipped
replacement for these model boundary conditions.

**Historical RUN comparison:** all three healthy 4 km cores, each nominally
2.5 mm^2, are paralleled at each transmitter end through the source-side RUN
contacts. Their combined nominal copper area is **7.5 mm^2**; the historical
illustrative **27.6 ohm/core** case gives **27.6 / 3 = 9.2 ohm** for the healthy
parallel equivalent. This is preserved resistance arithmetic, not a measurement,
RUN RF model or proof of transmitter compatibility. Healthy symmetry reduces
differential indicator loading, but real cable imbalance, faults, protection
capacitance and earth coupling must be checked with the actual transmitter and
receiver. Do not describe the boards as **RF-invisible** or add a blanket earth
plane across the isolated fence nets. No new RF qualification is implied.

### Parameters And Equations

Defaults are **41 stations**, numbered 0 through 40 at 0.1 km spacing; 82 branches; 36 V; and the historical illustrative 6.9 ohm/km per core. The 2.1 V LED / 0.7 V series-diode defaults preserve that comparison, **not characterized APEM/BYG23T I/V data**. `design_bounds.py` uses TE 35212K2FT tolerance/TCR with a **declared 25 C resistance reference and linear temperature screen**, the unchanged conditional cable/contact ceiling and a **5.2 V high-drop screen** (3.3 LED + the BYG23T 1.9 V maximum tested at 1 A/25 C). Neither junction test point is a full-temperature indicator-current guarantee. `R_nom_25` below is the assumed model reference, not a TE test-condition claim.

For core `c`, station `s`, and span length `dx`:

```text
r_span[c] = r20[c] * dx * (1 + cable_error[c]) * (1 + alpha * (T_cable - 20))
R[c,s]    = R_nom_25[c,s] * (1 + R_error[c,s]) * (1 + TCR_ppm[c,s]*1e-6*(T_R - 25))
V_LED     = V_LED_20 + LED_tempco * (T_junction - 20)
V_D       = V_D_20   + D_tempco   * (T_junction - 20)
V_source  = V_setting * (1 + source_error) * (1 + source_tempco*(T_source - 25))
            + selected_ripple_peak
I[c,s]    = max(0, (V[c,s] - V[B,s] - V_LED[c,s] - V_D[c,s]) / R[c,s])
P_R       = I^2 * R
P_LED     = I * V_LED
P_D       = I * V_D
```

These are branch/zero-leak LED currents. For a conducting fixed-Vf LED,
`I_LED = I_branch - I_clamp`; `branch_budget()` and the bounds report separately
account for up to **50 uA** normal clamp diversion under an explicit monotone
leakage/temperature assumption. This current is already in the resistor/diode/
PSU path, not an extra input load. The physical series-diode reverse leakage,
unpowered-island currents, capacitance and recovery remain outside the solver.

The copper temperature coefficient defaults to 0.00393/C as an engineering approximation. Tolerances and temperature coefficients are **signed selected corners**, not random distributions or automatically combined manufacturer maxima. Per-core cable resistance/errors and per-channel R/LED/diode parameters are independent. `channel_overrides` permits station-specific branches. Temperature correction is an input, not a self-heating iteration; reject negative/nonfinite effective parameters. Contact/splice aging, actual cable maximum resistance, and LED I/V distributions still need data.

- Nodes A/B/C are separate everywhere except the explicit source-side A/C connection. Healthy symmetry is an output/check, not a fault-model simplification.
- A cut `("A", 0)` removes the A conductor between stations 0 and 1. Span 39 is 3900-4000 m. Cut core names must be single valid core names; `"AB"` is not accepted as one core.
- Ideal wires and zero cable resistance are contracted exactly. An ideal short across an ideal nonzero source raises `IdealSourceShort`; it cannot produce a finite fuse verdict.
- Piecewise-linear passive branches are solved using damped Newton steps with sparse symmetric elimination. Convergence is checked against KCL, not just small voltage changes. Default residual tolerance is 1e-10 A; nonconvergence is an error.
- Floating components use a numerical voltage reference **without a conductance to earth/negative**. Their undetermined absolute node voltages are returned as `None`. Blocked one-way branches cannot backfeed those islands. These voltages are not inferred to be zero or safe to touch.
- Ideal-link currents are recovered by KCL where the ideal connection graph is a tree. Ideal cycles have indeterminate sharing, reported as `None`, with zero ideal-link dissipation. No equal-sharing assumption is made.
- Source and return current, every finite path's current/power, individual resistor/LED/diode power, KCL residual, and total power residual are available. Source power equals cable, branch, source-series, and fault-path dissipation within numerical tolerance. Only without cross-core/earth faults does source current equal the sum of indicator currents.
- `Fault(name, a, b, ohm, arc_v)` adds an explicit node-to-node path. Zero arc voltage is an ohmic fault; a positive arc voltage uses `I = sign(dV)*max(abs(dV)-V_arc,0)/R_arc`. It is a **conditional ignited-state load line**, not a sparkover, holding-current, hysteresis, or extinction model. The 10/15 V study values are sensitivities around published typical arc voltages, not guaranteed limits.
- `E` nodes and earth-path impedances must be explicitly supplied. This permits two fired line/earth tubes at different stations to complete a loop even with no DC-negative/PE bond. It makes **no proposal for unbonded electrodes**. A single tube with no modeled DC return has zero modeled steady current, not demonstrated safety in the real site's capacitive/leakage/PE network.

The solver does not model the external LED's internal reverse voltage, semiconductor recovery/capacitance, ignition, cable inductance/propagation, RF, lightning, cattle-fence pulses, PSU control dynamics, optics, or actual temperature. A zero forward current under reversed supply is expressly **not** a C4 protection pass.

### Reproduction

Repository-only reproduction, from the checkout root using Python's standard library:

```bash
TMPDIR=/tmp/opencode python3 -B -W error -m unittest discover -s tests -p test_electrical.py -v
TMPDIR=/tmp/opencode python3 -B -W error -m unittest discover -s tests -p test_design_bounds.py -v
TMPDIR=/tmp/opencode python3 -B scripts/analyze_limits.py --json
TMPDIR=/tmp/opencode python3 -B scripts/design_bounds.py --json
```

`--json` writes the declared inputs, summaries, cut regression, and prospective fault study to stdout; no scratch evidence or third-party numeric packages are needed. Both CLIs report `model_scope=prototype_only`. CLI two-value channel arguments are A then C; three-value cable arguments are A, B, C. `--r-core` units are ohm/km at 20 C, not resistance of the whole perimeter. The resistor/TCR reference and default `--resistor-temp` remain **25 C as a declared engineering assumption**; default TCR remains zero for the nominal comparison. Cable and junction-drop references stay at 20 C, source at 25 C. The CLI clean-cut sweep is a functional test and fails if selected inputs cannot produce the expected electrically ON states; use `simulate()` directly for undervoltage/reversed-source investigations. DESIGN_BOUNDS records the machine-readable provenance and unknown manufacturer test fields.

Previous **HP12** SMT synchronization verified on Python **3.14.4**: **23 electrical and 13 design-bound tests PASS**, including all **280 nominal clean-cut cases** (7 combinations x 40 spans), a second 280-cut sweep at the selected nonuniform corner, **615 inter-core fault cases** (3 pairs x 5 states x 41 stations), all five earth-connected station locations (0/10/20/30/40), repair/retest, floating islands, closed-form solutions, HP12 TCR/reference/rating limits, thermal arithmetic and CLI JSON/error status. Both normal `--json` CLIs exited 0. No native/build/approval operation or physical test was run for that bounded HP12 update.

**Historical PS12 synchronization, 2026-09-08:** all four reproduction commands above passed
on **Python 3.14.4**, with **23 electrical and 13 design-bound tests, no skips**.
Both CLIs exited 0 with and without `--json`. Normal numerical expectations remain
unchanged; tests then checked PS12 identity, 500/1000/500 V family ratings and the
separate one-pulse-curve scope. No native/build/workflow/approval operation,
commit, upload, order or physical test was performed by this bounded update.

**TE evidence/provenance correction, 2026-09-11, before deduplication:** isolated suites on
**Python 3.14.4** pass **23 electrical +14 design-bound tests, no failures or
skips**, preserving all normal numerical expectations. Both read-only model
commands without `--json` exit 0; JSON/error paths pass in the focused suites.
New/updated assertions distinguish assumed temperature conditions, unknown TE
test parameters and unverified catalogue-rating transfer. No native/build/
workflow/approval operation, commit, upload, order or physical test was run.

Clean-cut sweep maximum KCL residual: **4.34e-14 A**. Maximum source/power-balance residual: **7.71e-12 W**. These are numerical errors, not measurement uncertainty or model accuracy.

## 2. Calculated Results

These are **historical ideal-36 V comparisons**, not measurements or current
parametric bounds. Their currents are branch currents before clamp diversion.
[DESIGN_BOUNDS: Normal Current](DESIGN_BOUNDS.md#normal-current) owns the current
TE prototype upper, cable/tolerance and leakage screens with their assumptions.

| Case | Source A | Source W | Branch current min/max, mA | Largest resistor W |
| :--- | ---: | ---: | ---: | ---: |
| 41 boards, 27.6 ohm/core, 2.8 V total branch drop | 0.847705 | 30.5174 | 8.0448 / 15.0909 | 0.501018 |
| Five boards, zero cable R | 0.150909 | 5.4327 | 15.0909 / 15.0909 | 0.501018 |
| All 41 boards, zero cable R | 1.237455 | 44.5484 | 15.0909 / 15.0909 | 0.501018 |
| 41 boards, 40 ohm/core, 3.3 V LED + 0.7 V diode | 0.727083 | 26.1750 | 6.2096 / 14.5455 | 0.465455 |

The low-R entire-load case is essential: a five-board demonstration does not establish 41-board capacity. The LRS-75-36 has capacity margin for these declared cases before actual thermal/input derating and added protection/auxiliary load. Inspect the delivered working unit's nameplate and settings; its disconnected spare contributes no current or power. The LRS-35 results remain historical comparisons, not the current source allocation. Neither model is a coordinated fence-fault protective device by itself.

### Open-Circuit Observability

For a single clean cut with healthy branches/GDTs and no additional shorts, the
expected states pass at **every** span, including both terminal spans. Before
the cut both channels remain on; after an A-only or C-only cut only the intact
channel remains on. B-only, any two-core or all-three-core cuts leave both off.
Use the first applicable state transition to locate the adjacent 100 m span,
then isolate all sources and six ends before repair; retest for further sites.
The full truth table and operating procedure are
[INSTALL's Clean-Cut Indications](../INSTALL.md#clean-cut-indications)
and [Repair And Retest](../INSTALL.md#repair-and-retest), supplemental
**repository-only** references.

Tests remove complete cuts at spans 0, 19, and 39 in turn and verify that repair reveals the next site; representative successive single-core faults are also tested. The 1 microamp ON discriminator is only a numerical state classifier. No daylight brightness is established at that threshold.

Negative controls deliberately reproduce both defects: a permanent End A/C strap illuminates the broken channel after an A-only or C-only cut; connecting both B ends to negative leaves both channels lit after a B-only cut. A failed-short AC arrester can similarly mask an A cut. No clean-cut localization promise applies to mixed shorts/cuts or failed indicators/protection parts.

## 3. Continuous Operation: W3 Open

[DESIGN_BOUNDS: Evidence And Inputs](DESIGN_BOUNDS.md#evidence-and-inputs) owns
the source/tolerance/TCR derivation: **35 V feed floor / 40.39597 V upper are
declared screens, not enforced limits or a guaranteed combined PSU maximum**.
Startup, overshoot, malfunction, external surges and aging are outside that
normal envelope; the PSU's higher OVP threshold does not enforce it. Zero
junction drops screen upper branch stress and output shorts, not a physical
LED operating point. Current/leakage splits, nonuniform-cable corners, local
tap versus whole-source loading and daylight limitations are in
[Normal Current](DESIGN_BOUNDS.md#normal-current).

The **2026-09-11 TE correction** distinguishes supported +/-100 ppm/C from
the **assumed 25 C reference and linear temperature screen**, not TE-confirmed
test endpoints or a self-heating solution. [Thermal Screens](DESIGN_BOUNDS.md#thermal-screens)
owns exact loss, derating/working-voltage arithmetic and unknown overload-test
fields, separately from named PR02/MBE comparisons. TE's **four-layer, 2 oz
outer / 4 oz inner reference PCB** differs from this **two-layer, 2 oz-per-side
board**: catalogue-rating transfer is unverified, not proof of two-layer failure.
The [retained alternative lands](ASSEMBLY.md#2512-smt-resistors) still require
W4 placement/stencil/solder acceptance. **PR02 thermal/standoff data and PS12
overload/pulse curves do not qualify TE.** SMT changes heat flow, not generated
watts or evidence that the resistor/OneGel is cooler; no hot-spot or mounted
K/W model is established for this part.

**Disposition:** establish the actual allowed source envelope and measure
steady-state closed-OneGel chip/pad/PCB and material-interface temperatures,
with both branches, output shorts and credible hot/solar conditions. Rating-only
ambient ceilings are not simultaneous electrothermal limits; the resistance
screen separately assumes resistor temperature <=125 C. The former 35-37 V
proposal is unimplemented; qualifying a passive design over the real normal PSU
range is an alternative to a new precision cutoff. The **60 C interface / 110 C
film targets** remain proposed development targets, not universal user limits.
Meet actual part/cable/material limits with uncertainty. **Normal TEST must be
continuous-safe without a timer**; no such thermal test has been performed.

J_IN carries local indicator current, not the distributed current in WAGO
through-splices and the hub. Contact heating and surge paths need separate
evidence; no 72 A terminal/board rating is assigned.

## 4. Powered Faults: C5 Open

### Source And Fuse Interpretation

`assess_psu()` checks **both** rated current and rated output power, with a configurable continuous derating factor. Mean Well [S4] specifies overload at **110-150% of rated output power**, hiccup mode, automatic recovery after fault removal. The model distinguishes within-rated, outside-rated, overload-threshold-band, and above-the-band CV demand. It does **not** replace the supply by a constant-current source or claim a hiccup duration/duty cycle. Actual overload current and fuse-clearing time are returned as `None`.

Littelfuse 217 data [S5], for the specified `0217002.MXP` 2 A fuse, includes **70 A interruption at 60/75 VDC**, not just a 250 VAC label. Relevant standardized continuous-current tests are:

| Applied current | Published opening condition |
| :--- | :--- |
| 3.0 A, 150% | 60 minutes minimum |
| 4.2 A, 210% | 30 minutes maximum |
| 5.5 A, 275% | 0.05 to 2 seconds |
| 8.0 A, 400% | 0.01 to 0.3 seconds |

These are specified test conditions, not a prediction under source hiccup, outdoor temperatures or pulse repetition. The nominal melting I-squared-t of 5.73 A2s is not a complete low-current clearing or cyclic cooling model. The former instantaneous 2 A fuse-blow verdict is removed. Do not fix coordination by simply choosing a smaller fuse without healthy-load, cable, fault, temperature and inrush discrimination.

### Actual Topology Locations

The fault study explicitly uses **0.25 ohm lumped source-path resistance**, with **0.1 ohm arc slope** for ignited-state cases. These are transparent example inputs, not measured PSU/lead/GDT specifications. `--source-ohm` changes that input; the study uses the 0.25 ohm example when the nominal source is ideal. Hard faults are exact zero ohms. Each location includes both channels' distributed load and the separate A/B/C conductors. Selected results:

| Path/state | Station / distance | Source A | Fault-path A | Fault-path W | Interpretation |
| :--- | :--- | ---: | ---: | ---: | :--- |
| AB hard short | 0 / 0 km | 144.000000 | 144.000000 | 0 ideal | CV invalid for either PSU; **not actual fault current** |
| AB 100 ohm | 0 / 0 km | 1.197071 | 0.357007 | 12.745423 | Within LRS-75 rating; resistor-like fault heating can persist |
| AB hard short | 20 / 2 km | 1.600490 | 1.160727 | 0 ideal | Within LRS-75 rating; 2 A fuse not a prompt disconnect |
| AB 100 ohm | 20 / 2 km | 0.969602 | 0.199537 | 3.981497 | Within either nominal PSU envelope |
| AB hard short | 40 / 4 km | 1.112913 | 0.507648 | 0 ideal | LRS-35 overload band; within LRS-75 rating |
| AB 100 ohm | 40 / 4 km | 0.919507 | 0.145702 | 2.122913 | Within either nominal PSU envelope |
| AB ignited 10 V | 40 / 4 km | **0.979810** | **0.259543** | **2.602168** | Follow-current load line below 1 A total |
| AB ignited 15 V | 40 / 4 km | 0.913626 | 0.134598 | 2.020787 | Also below either source's rating |
| A_E@40 and B_E@0, each 10 V, shared-earth path 1 ohm | Both shed ends | 1.192841 | 0.417771 per tube | 4.195167 per modeled tube path | No negative/PE bond needed for this two-tube circuit |
| Same two paths, each 15 V | Both shed ends | 0.863876 | 0.025684 per tube | 0.385321 per modeled tube path | Positive load-line current is not proof the physical arc holds |

CB results equal AB only for the symmetric default inputs; both are separately solved. AC has no driven steady follow current in the healthy symmetric case, not a generic guarantee under asymmetry, cuts or an external transient. A short AC tube creates a diagnostic backfeed path. All three common-mode tubes are additionally tested at the actual five earth-connected station indices. The earth-path values 0/1/10 ohm are sensitivities, not an earthing design or electrode measurements.

An ideal short's zero modeled dissipation excludes real contact/arcing resistance; cable and source-path power still dissipate energy. A large CV demand is useful for showing loss of regulation, but **cannot** be used as sustained GDT heating or as evidence that the fuse will open. Conversely, the sub-rated far-end cases demonstrate that the PSU overload function need not intervene. GDT glow-to-arc transition current is not holding current, and 36 V below 470 V DC sparkover says nothing sufficient about post-ignition extinction.

### Architecture Decision And Interface Requirements

The alternatives and interface targets below preserve the earlier C5
investigation. They are not a newly selected circuit or a prerequisite imposed
by this SMT model update on prototype exports; C5 performance remains unresolved.
The Ruilon/Bencent and raised-overpass references in that investigation retain
their historical applicability; the current AC selection is the SMT Ruilon in
section 1, not a new source-shutdown or holdover-qualified architecture.

**Recovery in plain terms:** a GDT normally has very high resistance. A sufficiently
large surge ionizes its gas and starts conduction; the conducting arc voltage is
only roughly 10-15 V for the present parts, not their approximately 470 V firing
voltage. After the surge, the gas must deionize and the tube stop conducting.
If the DC source keeps enough current flowing, the tube may remain conducting
or restrike. A 36 V source being below 470 V does not, by itself, prove recovery.
The modeled 0.26 A / 2.6 W far-end arc with less than 1 A total supply current
explains why the 2 A fuse need not clear it. **This is a conditional scenario,
not a measured failure of the selected tubes.** Obtain application-specific
recovery evidence or perform a protected powered type test; the cattle-fence
prohibition removes one exposure, not this device/source interaction.

**Bare GDTs plus the existing fuse/hiccup PSU are not an approved protection architecture.** The following are bounded engineering paths, not completed selections:

1. **Retain bare tubes only with explicit DC holdover and fault containment evidence.** Obtain Ruilon/Bencent extinction specifications for the actual source/cable RLC network, temperature, life, pulse polarity and restarting PSU. Bourns `2027-47-BLF` is a concrete alternative to investigate: [S11] specifies 135 V DC holdover with extinction under 150 ms, but expressly says **"network applied"**. Its test network must be obtained and compared with this system; a voltage number alone is insufficient. The current drawing is **8.0 +/-0.4 mm body diameter**, not the previously suggested 6 mm drop-in. It cannot silently replace the overpass or SMT tubes. Its 1 kV/us sparkover figure is a **typical distribution**, not a guaranteed better residual-voltage limit. No substitution is approved.
2. **Use a coordinated series GDT/MOV path instead of an unqualified bare tube where self-extinction cannot be established.** Bourns `GMOV-14D500K` is an actual manufacturer-supported AC/DC hybrid candidate [S12]: 65 VDC MCOV, <1 microamp leakage and 4 pF capacitance at the stated 25 C conditions, MOV 82 V +/-10% at 1 mA, and a 230 V nominal GDT. This gives a concrete non-arc voltage-limiting element in series with the tube, rather than trying to infer extinction from 470 V sparkover. However its front protection level is still up to 800 V under the stated test; its 150 V clamp entry is **typical**, not a 5 V LED clamp. Body maximum 16.5 mm diameter/20 mm height and 7.5 +/-1 mm lead pitch are not existing footprints. DC recovery, post-damage failure, thermal disconnect/containment, RF/cable coordination, protected geometry and enclosure fit remain to qualify. Do not parallel it with the original bare GDT and assume follow current is then solved; the bare path would remain.
3. **A source disconnect can supplement either path, not replace missing remote-fault coverage.** A simple fixed overcurrent threshold cannot distinguish the 0.86-0.98 A follow-current cases from the provisional normal-load range, which extends beyond 1.2 A at low cable R. A larger supply worsens available follow energy. If retaining tubes without guaranteed self-extinction, event/local-temperature sensing or another proven means of detecting every sustaining path must drive a latched disconnect. No such complete detector/shutdown design is implemented. Do not call a hub relay alone a C5 fix.

Required TEST interface behavior for the next circuit decision:

- Maintain nominal 36 V and an **enforced** allowed maximum appropriate to the accepted resistor/LED design; detect overvoltage independently of the PSU's higher OVP threshold. Include supply adjustment, tolerance, startup, failed regulation and source-interface drop.
- Carry the entire healthy low-R load continuously, including tolerances and auxiliary/clamp currents; the current screen is **1.536239 A/62.0579 W**. The older proposed 1.6 A nominal limiter settings are not automatically suitable at their minimum tolerance. Apply actual source/interface derating, not only the nominal 0.847705 A load.
- Coordinate fast current limiting, short-circuit interruption, and **latched** source isolation following detected surge/follow-current, persistent overload or repeated PSU dropout. No automatic retry into a known fault. Operator reset must not automatically restore RUN.
- Isolate TEST positive before the A/C source split and TEST negative from Start B using appropriately rated, independently reviewed interruption/isolation means. Keep all six mode contacts independent, prevent transmitter/PSU connection during global transfer, and retain protective-earth continuity. Never open PE to extinguish a GDT.
- Specify the actual maximum fault energy and interruption time from component/path limits, not an arbitrary safe timeout. Measure source output capacitance and current waveforms: `E_cap = C*V^2/2`, `E_GDT = integral(V_GDT(t)*I_GDT(t) dt)`. Include cable stored energy, turn-off overshoot and repeated hiccup pulses. Require sufficient off time and a verified recovery test before re-energization.
- Prove detection or benign continuous fault behavior for **sub-rated resistive shorts** as well as GDT follow current. Overcurrent protection alone cannot promise this; normal/fault current ranges overlap. Local thermal interruption in a GDT path does not protect an unrelated cable resistive short.

No time limit on healthy TEST is proposed. A fault-triggered latch is a different safety function. The preferred immediate evidence request is a quantified holdover/recovery comparison for the actual tubes and the `2027-47` candidate; if that fails, evaluate the series GDT/MOV architecture before freezing the PCB. None of these routes establishes a board-level lightning rating.

## 5. LED Protection: C4 Open

The candidate calculations in this section are **historical MBE/onsemi-era
investigations**, not the selected TE 3521/BYG23T limits. Its original requirement
to survive both installation polarity errors is **superseded by the user decision
in section 9**. Do not treat the
historical active/clamp investigations as mandatory circuitry or a specified
field surge environment.

### Necessary Topology

With only the series rectifier, reversed supply puts two dissimilar reverse-biased junctions in series. Their leakage/capacitance determines voltage sharing; it does not guarantee LED VR <=5 V. With normal supply but reversed flying leads, the rectifier conducts and the external LED takes reverse voltage. An ordinary PCB antiparallel diode, anode at B and cathode at LED_POS, is then **also reverse biased** and does not solve that second fault.

The smallest credible **DC-reversal candidate** is a true low-voltage avalanche/shunt clamp from LED_POS to B, downstream of the existing R and rectifier. It must conduct in avalanche for positive connector voltage and in the forward direction for negative connector voltage. The existing R/D must remain in series with **every** core-to-connector path, so a clamp cannot introduce B-to-A/C backfeed. A bridge or a clamp directly across the core pair cannot be validated by the existing one-way-rung model.

Required evidence is simultaneous, not interchangeable:

```text
V_clamp_positive_max(I, T, tolerance, ringing) <= 5 V     # LED leads reversed
abs(V_clamp_negative_min(I, T, ringing))       <= 5 V     # source reversed
I_LED_normal_min = I_branch_min - I_shunt_max(V_LED_max,T) # retain daylight current
I_LED_peak and pulse energy <= accepted APEM pulse limits # correct orientation too
```

The accessible APEM product page [S1] confirms no resistor, family 1.8-3.3 V, 20 mA maximum and 5 V reverse maximum. It does not provide the **exact SG LED's maximum Vf over current/temperature**, reverse-leakage distribution or a forward-pulse safe operating envelope. The family voltage range is not a guaranteed min/max junction I/V specification at all temperatures. Pending better data, do not design above 20 mA on the assumption that short pulses are harmless, or trade away existing useful current without a daylight test.

### Researched Candidates

| Candidate | Accessible primary data | Decision / missing evidence |
| :--- | :--- | :--- |
| **Vishay BZX85C3V9-TR**, two proposed PCB clamps | [S6], rev. 2.9: VZ **3.7-4.1 V at 60 mA**, 5 ms pulse, 25 C; dynamic R <15 ohm at that point; coefficient -0.07 to -0.02 %/C **at 60 mA**; leakage <10 microamp **at 1 V**. DO-41; 0.86 mm maximum lead. | Best minimal passive candidate to characterize, **not approved**. Available DC branch current is <18.65 mA in the declared screen, below its 60 mA VZ test point. A monotone quasi-static I/V assumption therefore makes the 4.1 V point useful, unlike a 5 mA-tested small zener. But no guaranteed leakage at the green LED's actual Vf/temperature, no full-current/full-temperature clamp envelope, and no forward transient LED-current protection are established. Its forward-voltage graph is typical, not a guaranteed negative-polarity clamp bound. |
| **Vishay BZX85C4V3-TR** | [S6]: **4.0-4.6 V at 50 mA**, coefficient -0.05 to +0.01 %/C there, leakage <3 microamp at 1 V. | More separation from green Vf, less reverse-voltage margin. Still no guaranteed leakage at 3.3 V or actual maximum green Vf. Not approved. |
| **Nexperia BZT52H-B3V9** | [S7], rev. 7: **3.82-3.98 V at 5 mA**, differential R up to 95 ohm at 5 mA and 500 ohm at 1 mA; coefficient -3.5 to 0 mV/K at 5 mA; leakage <=3 microamp at 1 V; VF <=0.9 V at 10 mA under pulse test. | Not enough evidence for a 16-19 mA reversed-lead DC load. The 5 mA VZ maximum is not its clamp maximum at that higher current; a small-signal differential resistance at one point is not a global slope bound. The headline 830 mW requires 1 cm2 cathode copper; standard-footprint P25 is 375 mW. No implementation approval or packaging suffix allocation. |
| **TI TL431BQDBZR**, adjustable shunt fallback | [S8], SLVS543S: 1-100 mA recommended cathode range; B-grade Vref **2.483-2.507 V at 10 mA**; 34 mV maximum full Q-temperature deviation; Iref <=4 microamp, deviation <=2.5 microamp; dynamic impedance <=0.5 ohm at the specified low-frequency conditions. | A sharper, calculable DC threshold is possible, at the cost of two divider resistors per channel and reverse-polarity design. Not an automatically qualified fast clamp. Off-current <=0.5 microamp is tested at **REF=0**, not at the near-threshold REF voltage during normal LED operation. Need actual off-region loading, startup/overshoot, capacitive stability, negative-polarity behavior, thermal/pulse data and LED Vf. No complete circuit/BOM selected. |
| **TI TL431LIBQDBZR** | [S9]: 1-15 mA recommended cathode range, 18 mA absolute positive limit. | **Reject as a direct replacement shunt for this unrestricted branch.** Reversed/open-LED branch current can exceed 15 mA. The similar name does not confer the standard TL431's 100 mA capability. |

For example, extrapolating the BZX85C3V9 test-point coefficient from 25 to -40 C gives `4.1*(1 + 0.0007*65) = 4.28655 V` at that test point. This is a useful **screening calculation**, not proof of a guaranteed 4.28655 V transient/full-temperature clamp at this application's current. Hot low-current leakage and the cold LED's higher Vf can both matter to brightness. Obtain those bounds rather than silently using the nominal zener number or a typical curve.

### Forward-Pulse Obstacle

Even a perfectly bounded 4 V clamp across an LED does not enforce 20 mA: a correctly oriented LED may take excessive current **before** its terminal voltage reaches the clamp threshold. The existing R limits but does not establish pulse safety. At an illustrative 950 V input and the nominal 2.8 V branch drop, `branch_budget(950)` gives **430.5 mA and 407.8 W instantaneous resistor demand**. This is an electrical stress screen, not the actual transient waveform or absorbed energy. Neither a 1 W DC resistor rating nor a zener's pulse-power rating qualifies the LED.

Simply splitting the present 2.2 kohm into a pre-clamp resistor and a post-clamp resistor also needs a feasibility check. With only the broad family screening values Vf_min=1.8 V, Vf_max=3.3 V, an ideal clamp `Vc <=5 V`, a desired high-Vf source-end current of `(36-3.3-0.7)/2200 = 14.545 mA`, and a 20 mA peak ceiling:

```text
R_post >= (Vc - 1.8)/0.020        # bound current for the low-Vf LED
R_post <= (Vc - 3.3)/0.014545...  # do not clip normal high-Vf LED current
```

Even with **zero clamp tolerance**, both require Vc >=7.3 V, incompatible with a 5 V reversed-lead limit. This does not prove the actual SG LED has that broad Vf spread; it proves that **those family numbers are insufficient to approve the simple split-resistor solution**. Narrower exact LED data, an accepted optical-current tradeoff, or a separately qualified active current limiter is needed. Do not choose a 20 mA nominal current-regulator part whose maximum exceeds the LED's 20 mA limit.

A supportable next architecture must therefore retain the one-way series path and provide **both local output-polarity voltage limiting and a demonstrated forward-current/pulse bound**. A pulse-rated upstream impedance plus a protected low-voltage current-limiting stage and output clamp is a credible larger alternative if the passive feasibility window does not close. Its compliance voltage, quiescent current and branch R must be recomputed to preserve the 6-15 mA-class useful field currents; no such active stage is selected or represented as validated by this DC model. Source shutdown alone cannot stop a transient induced locally in a kilometre-scale cable.

Measure the voltage at the **actual LED terminals**, not only the PCB connector: the nominal 200 mm flying leads add inductance and coupling, so clamp-loop placement and ringing can consume the reverse-voltage margin. Changing their polarity must not disconnect the protection from the LED being protected.

Rectifier coordination is also open. onsemi [S2] gives **1000 V repetitive reverse**, 1200 V **nonrepetitive** under the stated half-wave condition, junction range **-65 to +150 C**, and reverse leakage maxima 10 microamp at 25 C / 50 microamp at 100 C at rated DC voltage. The G suffix identifies the Pb-free order option; do not infer a 175 C limit from legacy prose. No specified fast-recovery/ringing bound is supplied here. The reviewed GDT data [S10] gives up to 950 V impulse sparkover for SMD5050-470NA and 1100 V for 2R470TD-8 at 1 kV/us; B5G470L's 850 V covers **99% of measured values**. Account for actual differential/common-mode paths, unequal ignition and lead inductance; do not treat 1200 V nonrepetitive rectifier data as blanket repetitive margin or 470 V as a transient clamp. Cable impulse withstand is unverified.

## 6. Historical P3 Candidate Handoff

This section preserves the earlier unselected zener/active candidate handoff.
The actual hybrid in sections 1/9 and ASSEMBLY supersedes its population status;
do not add these candidates to the new 16-part BOM. C4/C5/W3 remain open for
their documented unresolved qualification/design scope, not because D3/D4 are absent.

The exact **C4-A candidate netlist delta**, solely for evaluation if its evidence closes, is:

| Proposed reference | Candidate MPN | Required connections | Quantity |
| :--- | :--- | :--- | ---: |
| ZD1 | Vishay BZX85C3V9-TR | Cathode / KiCad pin 1 to `LED_A_POS` = D1.1 = J_LED_A.1; anode / pin 2 to `WIRE_B` = J_LED_A.2 | 1 |
| ZD2 | Vishay BZX85C3V9-TR | Cathode / pin 1 to `LED_C_POS` = D2.1 = J_LED_C.1; anode / pin 2 to `WIRE_B` = J_LED_C.2 | 1 |

R1/R2, D1/D2, terminal polarity and the one-way series order stay unchanged in that candidate. Do **not** connect these clamps to EARTH, the resistor input, or across D1/D2. Candidate DO-41 maximum body is 4.1 x 2.6 mm, lead maximum 0.86 mm; a 1.10 mm nominal finished PTH permits 1.02 mm at -0.08 tolerance, or 0.16 mm diametral lead clearance. Pad/annular ring, spacing, forming, pulse loop and actual placement still require P3/assembler acceptance. No coordinates, footprint fit, availability/C-code, or current sharing are assumed. If eventually selected alone it adds two THT parts, but **alone it does not close the forward-pulse requirement**; final counts depend on the complete design.

For the **C4-B active-clamp investigation**, an explicit DC starting circuit is TL431BQDBZR cathode pin 1 to the same LED_POS, anode pin 3 to B, reference pin 2 to a divider with 4.42 kohm LED_POS-to-REF and 10.0 kohm REF-to-B. Its ideal threshold is about 3.598 V; calculate reference, divider tolerance/TCR, Iref, cathode-current dependence, and transient errors before assigning a bound. Divider nominal loading alone is approximately 0.23 mA at 3.3 V. Divider MPNs and reverse protection are **not selected**; this is not a complete alternative BOM or pulse-safe circuit.

The next bounded decisions/evidence are:

1. **APEM:** obtain SG02E max/min Vf vs current and junction temperature, continuous-current derating, permitted forward pulse current/energy/repetition, reverse limit conditions and harness capacitance. Measure representative purchased parts and daylight ON/OFF at 5 m, but do not replace manufacturer worst-case bounds with a few samples.
2. **Clamp vendor/design:** for BZX85C3V9/C4V3, request maximum I at the actual LED maximum Vf over temperature and maximum positive/negative clamp voltage over the available branch current and defined pulse envelope. A provisional brightness budget is <=0.3 mA shunt diversion at the minimum useful current (about 5% of the 6.21 mA sensitivity), subject to actual 5 m acceptance; it is a target, not a part specification. If unavailable or incompatible, use the active-stage route and qualify its current limit rather than adding a guessed zener.
3. **Source/GDT:** confirm PSU nameplate, setting/adjustment behavior, thermal derating, output C, overload/hiccup I(t), and shutdown/restart response. Obtain actual tube holdover test networks/conditions and a quantified quenching/failure-containment decision for every discharge path. Require the same review for `2027-47-BLF` or `GMOV-14D500K` before any geometry/BOM substitution.
4. **Thermal and transients:** settle the enforceable supply window and R choice, then test continuous normal/reversal/fault conditions in the potted/sun-heated assembly. Define the surge and nearby-cattle-fence pulse source impedance, polarities, repetitions and energy before approving rectifiers, resistors, clamps or shutdown timing. Keep an unpotted reference; use appropriate isolated/high-voltage instruments and qualified test facilities.
5. **Integration:** only after an approved electrical decision, parent/layout owners update actual schematic/PCB/BOM/CPL, retain protected copper/vias/earth clearance and LED terminal mappings, regenerate/check production data, and rerun these regressions with the real branch behavior. Add nonlinear/reverse/transient evidence; a one-way approximation must not validate a replacement that is actually bidirectional.

No claim of 5/20 kA assembled performance, 72 A terminal capacity, equal transient sharing, direct-strike protection, weather lifetime, or cable impulse withstand follows from this work. A source-side or local protection redesign must retain the agreed earthing/bonding review and RF/site acceptance; there is no assumed unbonded-earth solution.

## 7. Evidence Register

Sources S1-S12 were retrieved during the earlier P2 session on 2026-09-06 using **webfetch only**; S13-S19 record later part reviews and identity evidence. APEM and TI HTML were readable directly. Where direct PDF fetching produced raw binary or a 403, text was obtained through `https://r.jina.ai/https://...` targeting the manufacturer document (or manufacturer-authored LCSC-hosted GDT document). That is an extraction aid, not a second manufacturer guarantee or proof the served revision is the latest. For the historical HP12 SMT conversion, the supplied research review visually confirmed S15 pages 1, 2, 4, 5, 6 and 8; that model update reread its TCR reference/test temperatures via webfetch text extraction, not a new visual land review. For the historical PS12 selection, the supplied research visually read S16 pages 1, 2, 4, 5, 6, 7 and 8 and verified the exact JLCPCB identity S17. The **2026-09-11 correction** uses the supplied TE drawing review plus fresh S18 text extraction (after direct webfetch returned PDF binary) and a fresh live S19 identity fetch. It confirms Rev G, 02/2025 and the stated TCR method/mounting text, not a new visual pad-leader inspection, vendor acceptance or physical qualification. ASSEMBLY/DFM controls the drawing/process review.

**2026-09-14 GDT provenance:** this bounded note update uses the supplied
prior-turn review of original manufacturer PDF page images: **S20 pages
1, 2, 3, 5 and 6**, and **S21 pages 1-3**. It reuses that review and the existing
[DFM drawing evidence](DFM_EVIDENCE.md#smt-land-resolution), not a new fetch or
independent page-image inspection in this note task. The Bencent URL's
20260514 upload path is not a new revision; its sheet remains **A2, 2018-01-03**.
No supplier response, allocated-lot acceptance or powered-recovery test is inferred.

| ID | Primary document / provenance | Relevant evidence |
| :--- | :--- | :--- |
| S1 | [APEM Q10F5SXXSG02E live product page](https://www.apem.com/led-indicators/professional-grade-panel-mount-led-indicators/q10/q10f5sxxsg02e) | No-resistor option, 1.8-3.3 V family listing, 20 mA max, 5 V reverse, -40 to +85 C, 20-25 cNm = 0.20-0.25 Nm. Exact SG I/V/pulse bounds absent from retrieved page. |
| S2 | [onsemi 1N4001/D](https://www.onsemi.com/pdf/datasheet/1n4001-d.pdf), June 2024 rev. 18; [text extraction](https://r.jina.ai/https://www.onsemi.com/pdf/datasheet/1n4001-d.pdf) | **Historical, retired diode.** Pages 2/5/6: blocking/leakage/temperature, ordering suffixes, 0.86 mm lead maximum. |
| S3 | [Vishay 28766, MBx/SMA](https://www.vishay.com/docs/28766/mbxsma.pdf), 11-Jul-2018; [text extraction](https://r.jina.ai/https://www.vishay.com/docs/28766/mbxsma.pdf) | **Historical, retired MBE.** Pages 1-4/8-10: rating modes, film limits, TCR/tolerance, derating and separate pulse constraints, not TE 3521 data. |
| S4 | [Mean Well LRS-35](https://www.meanwell.com/Upload/PDF/LRS-35/LRS-35-SPEC.PDF), [LRS-75](https://www.meanwell.com/Upload/PDF/LRS-75/LRS-75-SPEC.PDF), file revision 2025-04-07; [35 text](https://r.jina.ai/https://www.meanwell.com/Upload/PDF/LRS-35/LRS-35-SPEC.PDF), [75 text](https://r.jina.ai/https://www.meanwell.com/Upload/PDF/LRS-75/LRS-75-SPEC.PDF) | 36 V / 1 A / 36 W and 36 V / 2.1 A / 75.6 W; adjustment/tolerance/ripple/tempco conditions; 110-150% output-power hiccup; higher OVP threshold. |
| S5 | [Littelfuse 217 datasheet](https://www.littelfuse.com/assetdocs/littelfuse-fuse-217-datasheet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), revised 07/17/25; [text extraction](https://r.jina.ai/https://www.littelfuse.com/assetdocs/littelfuse-fuse-217-datasheet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) | Pages 1-2: opening-time test conditions, 2 A row DC interruption and nominal I2t. |
| S6 | [Vishay BZX85, 85607](https://www.vishay.com/docs/85607/bzx85.pdf), rev. 2.9, 17-Sep-2025; [text extraction](https://r.jina.ai/https://www.vishay.com/docs/85607/bzx85.pdf) | Pages 1-3: exact zener test currents, leakage test voltages, coefficients, pulse conditions, conditional 1.3 W thermal rating, DO-41 dimensions and -TR ordering. |
| S7 | [Nexperia BZT52H series](https://assets.nexperia.com/documents/data-sheet/BZT52H_SER.pdf), rev. 7, 1-Jan-2023; [text extraction](https://r.jina.ai/https://assets.nexperia.com/documents/data-sheet/BZT52H_SER.pdf) | Pages 4-6: 5 mA VZ test, current-dependent differential R, 1 V leakage test, pulse and copper-dependent power ratings. |
| S8 | [TI TL431/TL432 SLVS543S](https://www.ti.com/document-viewer/TL431/datasheet), May 2024, sections 5, 6.4, 6.13, 9.2.2.2.3 | [BQ electrical limits](https://www.ti.com/document-viewer/TL431/datasheet/GUID-XXXXXXXX-SF0T-XXXX-XXXX-000000299837), [operating conditions](https://www.ti.com/document-viewer/TL431/datasheet/GUID-XXXXXXXX-SF0T-XXXX-XXXX-000000290477), [stability](https://www.ti.com/document-viewer/TL431/datasheet/GUID-AB8AA1BF-5A8E-4134-8DDE-4B67E83A4679), [pin mapping](https://www.ti.com/document-viewer/TL431/datasheet/GUID-55DC935C-B584-4F42-9176-D1944A98396D). |
| S9 | [TI TL431LI/TL432LI SLVSDQ6A](https://www.ti.com/lit/ds/symlink/tl431li.pdf), Nov 2018; [text extraction](https://r.jina.ai/https://www.ti.com/lit/ds/symlink/tl431li.pdf) | Pages 4-5: 15 mA recommended vs 18 mA absolute cathode current, not the standard TL431 rating. |
| S10 | Manufacturer-authored [Ruilon SMD5050 SP-GDT-006 A3/2024-08-19](https://www.lcsc.com/datasheet/C39692533.pdf), [2RD-8 SP-GDT-017 A3/2023-11-02](https://www.lcsc.com/datasheet/C2836978.pdf), [Bencent B5G470L A2/2018-01-03](https://www.lcsc.com/datasheet/C5337217.pdf), distributed by LCSC | Newly retrieved text via [SMD5050 extraction](https://r.jina.ai/https://www.lcsc.com/datasheet/C39692533.pdf), [2RD-8 extraction](https://r.jina.ai/https://www.lcsc.com/datasheet/C2836978.pdf), [B5G extraction](https://r.jina.ai/https://www.lcsc.com/datasheet/C5337217.pdf): 950/1100 V impulse limits and B5G's 99% figure; typical 15/10/15 V arcs at stated 1 A conditions. No system-specific holdover guarantee. |
| S11 | [Bourns 2027](https://www.bourns.com/docs/product-datasheets/2027.pdf), rev. E 01/26; [text extraction](https://r.jina.ai/https://www.bourns.com/docs/product-datasheets/2027.pdf) | Network-qualified DC holdover, typical-distribution impulse sparkover and actual 8 mm body/lead variants. |
| S12 | [Bourns GMOV](https://www.bourns.com/docs/product-datasheets/GMOV.pdf), rev. 01/25; [text extraction](https://r.jina.ai/https://www.bourns.com/docs/product-datasheets/GMOV.pdf) | Series GDT/MOV hybrid for AC/DC, explicit 14D500K data, large physical envelope and still-high transient front voltage. |
| S13 | [Vishay PR01/02/03, 28729](https://www.vishay.com/docs/28729/pr010203.pdf), 08-Jul-2025; [exact PR02 inventory reference](https://www.vishay.com/search?type=inv&query=PR02000202201FA100) | **Historical, retired PR02 selection.** 2.2k/1% copper-lead 2 W, 250 ppm/K, 0.83 maximum lead and axial mounting/hot-spot data. Its 220 C / 75 K/W / body-standoff figures do not apply to TE 3521. |
| S14 | [Vishay BYG23T-M3, 89429](https://www.vishay.com/docs/89429/byg23t.pdf), 25-Feb-2020; [C145454 exact identity](https://www.lcsc.com/product-detail/C145454.html) | Selected BYG23T-M3/TR, 1300 V repetitive reverse, SMA. Original p4 outline/land figure visually read through the public PDF viewer. 75 ns reverse recovery is not forward-clamp response; typical 9 V/620 ns forward recovery at 1.5 A/12 A per us is not a <=5 V guarantee. |
| S15 | [Uni-Royal HP Series, SMD-SP-003 V.7, 08-Jan-2026](https://www.uni-royal.cn/en/images/userfile/file/1784806233a2e6d381ea80b5d9.pdf) | **Historical, superseded HP122WF2201T4E selection, 2512 2.2k/1%.** HP12 2 W at 70 C ambient, linear derating to zero at 155 C; +/-100 ppm/C referenced to 25 C with -55/125 C TCR tests. Family 300/500 V working/overload maxima are also limited by sqrt(P*R) and 2.5 times that voltage. Five-second overload is not an impulse curve. That HP12 analysis did not import PR02 thermal parameters or the tighter website TCR. |
| S16 | [Uni-Royal PS Series, SMD-SP-007 V.7, 08-Jan-2026](https://www.uni-royal.cn/en/images/userfile/file/1784854235b7c79f8d8a205c5d.pdf), via the [PS product page](https://www.uni-royal.cn/en/article.php?id=10109) | **Historical PS122WF2201T4E, PS12 / 2512 2.2k/1%.** 2 W at 70 C ambient, linear derating to zero at 155 C, -55..155 C operation; +/-100 ppm/C at 25 C reference with -55/+125 C TCR tests. |
| S17 | [JLCPCB C2793873](https://jlcpcb.com/partdetail/C2793873) | Historical Uni-Royal PS122WF2201T4E identity. |
| S18 | [TE Connectivity CGS 3521, Data Sheet 9-1773463-5 Rev G, 02/2025](https://www.te.com/commerce/DocumentDelivery/DDEController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), [JLCPCB C4129105](https://jlcpcb.com/partdetail/C4129105) | **Selected 35212K2FT for prototype, 2512 2.2k/1%.** P1 catalogue 2 W at 70 C ambient, derating to zero at 155 C, -55..155 C operation; 250/500/500 V working/overload/dielectric ceilings; p2 RCWV formula. P3 recommended pads 1.50 x 3.00 mm, 5.00 inner gap / 6.50 pitch, with four-layer 2 oz outer / 4 oz inner mounting. P4 +/-100 ppm/C at 2.2k, room/min/max operating-temperature characterization (User Spec), without numeric TCR reference/endpoints. The overload ceiling supplies no short-time test voltage/duration. AEC-Q200 qualified, not board-qualified. |
| S19 | [JLCPCB C876850](https://jlcpcb.com/partdetail/C876850) | **Yageo SR2512FK-7W2K2L**, 2.2k/2 W/1%/100 ppm/2512 identity independently confirmed. Unpopulated production variant; separate part/model/process/thermal review is required before a source/BOM switch, not a TE model substitute. |
| S20 | [Ruilon SMD5050 Series, SP-GDT-006 A3, 2024-08-19](https://www.ruilon.com.cn/Uploads/pdf/06-smd5050%20series_a3.pdf) | Supplied 2026-09-14 original-page review, pp. 1/2/3/5/6; exact **SMD5050-470NA** electrical entries, body/land drawing and reflow/caution text. Current AB/BC/AC selection; component test conditions, not assembly or DC-recovery approval. |
| S21 | [Bencent B5G470L, A2, 2018-01-03](https://www.bencent.com.cn/index/xiazai/name/_upfile_admin_file_20260514_2026051411072672523.pdf.html) | Supplied 2026-09-14 original-page review, pp. 1-3. **Historical retired AC part**: preserves its DC/impulse/probability, capacitance and process comparison; not the current AC population or equivalent guarantees to SMD5050. |

## 8. Continuation Decision, 2026-09-07

This records the first continuation's analysis/selection state. The later
user decision in **section 9** supersedes its required installation-polarity
coverage and next-architecture recommendation, not its numerical evidence.

**P2 is not complete.** The research below narrows decisions and rejects specific
unsafe shortcuts; it does not turn an unselected circuit into a file-ready one.
The actual station is still the R/D/LED circuit in section 1. The working source
is one LRS-75-36; the spare remains disconnected. Provisional
CA10.A364/current WAA364 is **eight-pole**, but the same six-independent-end
functional matrix applies, and the exact DC/global-transfer approval is open.
See [ENVIRONMENT_EVIDENCE.md](ENVIRONMENT_EVIDENCE.md).

### Cable And Continuous Duty

The following is the **historical MBE / 20 C reference / 35..37 V / 4.4 V
screen**, not the current TE prototype calculation. `scripts/design_bounds.py` still
reuses the same three-core solver; current inputs/results are in sections 1-3
and [DESIGN_BOUNDS.md](DESIGN_BOUNDS.md):

- User reel identity **CM03/05.100** and red/black/plain-green colours are
  confirmed. AMC 2026 V.3 specifies 3 x 2.5 mm^2, Class 5 tinned copper,
  60 V max DC, -30..+70 C and 7.4 mm maximum OD.
- IEC 60228:2004 Table 3 gives **8.21 ohm/km at 20 C** for metal-coated 2.5 mm^2
  Class 5 copper. Use that as a **conditional design ceiling**, not measured
  reel resistance. AMC/reel 0.30 mm strands versus that table's 0.26 maximum
  is a construction/declaration discrepancy to reconcile, not an unknown reel
  identity or a reason to invent a different resistance column.
- At 70 C, plus an explicit **0.025 ohm/core/100 m span** contact allowance,
  the modeled upper core resistance is **40.29306 ohm**. Contact/splice budgets
  must hold per span at service temperature, not just in a whole-core sum.
- The study declares **35..37 V at the TEST feeds, nominal 36**, including
  normal ripple/hub losses. **Neither limit is enforced in hardware.** The
  existing accessible-adjustment 40.39597 V screen is still relevant until a
  real interface enforces the window; PSU OVP is not a 37 V limiter.
- At the declared low feed, uniform high-drop/Rmax branches give **5.8796 mA**
  far-end current. A single high-drop/Rmax far-end LED with all other drops
  zero and Rmin gives **4.6681 mA**. These named corners are not an exhaustive
  minimum. The deliberately loose independent-comparison lower bound is
  **1.4946 mA**, not a predicted brightness or an accepted optical current.
  None validates a new clamp's additional load or a guaranteed 6 mA minimum.
- At 37 V, zero drop/Rmin, the bounds are **17.0777 mA/branch, 1.400373 A total,
  0.631876 W/resistor**. Only **18.124 mW** remains below standard-mode P70.
  The derating-only local ambient ceiling is **71.534 C**; at 75 C the
  corresponding source ceiling is only **35.7805 V**. Thus a 37 V setting
  alone is not W3 closure.

The concrete thermal provisions for development are an instrumented closed
assembly with **60 C bulk/local-interface and 110 C film targets**, including
uncertainty, while separately keeping the actual cable interface <=70 C and
meeting all part/material limits. Those are proposed targets, not measured
temperatures. For just the two existing branches, 1.263751 W upper heat and
an illustrative 30 C outside/60 C bulk target require effective heat rejection
<=**23.7388 K/W**, **before solar/contact/auxiliary heat**. No OneGel conductivity
is fabricated to make this pass. Its own manufacturer sources disagree on
cure/temperature; it is one-component/no-mix **OneGel**, not MP0100.
Retaining the resistor for continuous normal TEST still needs source enforcement
and demonstrated thermal interfaces, or a supported circuit/thermal redesign.
A timeout is not substituted for normal-duty safety.

### C4: What The Candidate Work Actually Establishes

[LED_PROTECTION_RESEARCH.md](LED_PROTECTION_RESEARCH.md) contains complete
candidate connections, exact parts, original curve review and limitations:

| Candidate / result | Decision |
| :--- | :--- |
| Two individually 22-ohm-ballasted **LM4050BEM3-4.1/NOPB** references after the one-way diode | Calculated **4.3584 V steady connector ceiling at 20 mA total**, worst individual current **11.9273 mA <15 mA**. No equal sharing assumption. A separate negative clamp is still required. Below-knee loading uses an explicit monotonic/no-latch assumption; turn-on and actual LED-harness peaks remain unverified. This does not itself bound forward LED current. |
| L1: protected **LT3092** current stage | A 15.343..17.042 mA static engineering screen avoids needing LED Vf_min. **Do not populate L1:** startup/dropout recovery is not a guaranteed <=20 mA pulse ceiling. The subsequently viewed PWC2512 100 us curve also fails the proposed upstream rectangular-pulse screen. |
| L2: pulse impedance, **TVS2700**, then a precision 1.8k post-resistor and the output clamps | A declared protected node <=35 V and Rpost>=1770 give **19.774 mA** without assuming Vf_min. **Do not populate L2:** nominal normal TEST puts that node at **29.264 V**, outside TI's recommended 0..27 V range. An open post-resistor can allow **20.26 mA**, above the TVS's 12 mA absolute entry. A benign ordinary-duty input stage is still needed, not only a surge test. |
| TT **WHS2-200RFA25**, two per rung in the L2 comparison | Original pulse curves support room-temperature screening of <=0.210 J and <=664 V per part for the declared 1200 V/100 us envelope. This resolves the earlier unreadable-curve problem, not hot repetitive qualification, complete diode/TVS coordination or physical placement. |

The useful next C4 decision is a **continuous-duty-compatible pre-clamp plus
passive post-resistor**, or a genuinely bounded dynamic current stage. Do not
add an output zener alone and call forward-pulse protection complete. The
1200 V/100 us development envelope is a proposed test limit, not a measured
cattle-fence/field envelope. At the physical 200 mm LED leads, require actual
forward peak + uncertainty <=20 mA and reverse peak + uncertainty <=5 V.

### C5: Holdover Network And Fault Coverage

[SOURCE_PROTECTION_RESEARCH.md](SOURCE_PROTECTION_RESEARCH.md) resolves the
previously unspecified **ITU-T K.12 135 V test: 1300 ohm sustained DC feed**,
with a separate RC/surge network. At a 10 V tube voltage its DC feed is about
**96 mA**, versus the existing model's **260 mA** far-end arc path. Littelfuse's
0.2 A qualification is also below that modeled path. This fails a sufficient
load-line comparison; it does **not** prove the physical tube will latch.

**Do not make a compact-GDT-only substitution to close C5.** The investigated
Bourns GDT25/2035/2027 candidates have network-qualified holdover, not the
missing powered-fence guarantee. The 2027 candidate's ten-shot rating is 10 kA,
not the baseline earth tube's 20 kA; 2035 also has a same-MPN January-2027 PCN.

A genuinely DC-power-specified alternative exists: TDK
**B88069X1993B501 / LN8-A1200DC-4**, 48 V +/-20% with a stated 30 A source,
and **three grading capacitors per stack**. That is a credible bounded
electrical starting point, not a 135 V telecom extrapolation. Six cells need
six 8.4 x 13.8 x 8.9 mm-class SMD stacks and eighteen capacitors; no reviewed
guardrail-preserving mounting/RF solution has been demonstrated. No carrier,
guardrail change or substitution is approved by that size screen.

The source proposal (TPS26600 current limiter, independent OV, manual-reset
latch and two-pole TEST isolation) is **not a completed hub schematic**. Its
62 V absolute limit requires a coordinated surge front end; a 470 V GDT alone
does not protect it. Complete the latch/startup, DC isolation and energy budget
before connecting it to an exposed perimeter. PE must never be switched.

Finally, neither source limiting nor holdover specifies damaged-device safety.
A stable <=0.10-ohm short would dissipate <=0.256 W under an **enforced** 1.6 A
ceiling, but the declared cable study's near-source 100-ohm fault dissipates
**13.4676 W at only 1.2071 A total**. Local interruption/containment or a
supported benign failure envelope remains a real design task. These hazardous
sub-rated cases cannot be dismissed as insignificant faults or detected by
simply lowering a common fuse. A contained, independently monitored component
recovery experiment may precede field qualification; no such test was performed.

## 9. Simplified Indicator Direction

User clarification and subsequent implementation, 2026-09-07, after checkpoint
**ad282e3**, with TE prototype evidence corrected 2026-09-11 and the user-approved
SMT AC conversion recorded 2026-09-14. This is the current design direction,
not an approved order/field release:

- LED damage from **accidental low-voltage installation polarity reversal is
  accepted**, with spare indicators for replacement. This changes the required
  fault tolerance, not the APEM ratings or a test result. Wiring remains checked
  before power and corrected while isolated; no mains/PE error is accepted.
- **Continuous-safe normal TEST remains a hard requirement.** The indicators
  have exposed front faces in the intended cool environment, but this does not
  measure their junctions or the gel-filled PCB's resistor hot spots.
- Direct-strike rebuilding is accepted; no strike frequency is established.
  **Energized cattle fencing is now prohibited near the whole 4 km boundary,
  stations and hub**, explicitly confirmed by the user. The earlier 0.5 m /
  300 m parallel-run scenario is withdrawn; do not require an energizer-on test
  for the prohibited configuration or invent a universal safe separation.
  Confirm and maintain the exclusion; reassess if surrounding land use changes.
  Nearby lightning, ordinary switching and RUN behavior remain relevant.
- The authorized **16-part hybrid uses SMT R1/R2 and all three inter-core GDTs**:
  **nine SMT and seven THT** electrical parts, plus four mounting footprints.
  Use the [reviewed prototype population](ASSEMBLY.md#reviewed-components), not
  an automatic Yageo substitution. GDT_AC replaces the axial Bencent with the
  same Ruilon SMT part as AB/BC, without changing any GDT net connections. No
  active current stage, timer or new supply connection is fitted.

### Minimal Circuit And Layout

The implementation retains `WIRE_A/C -> 2.2k resistor -> series diode -> LED_POS`.
D3/D4 add one diode per channel with **cathode at LED_POS and anode at
WIRE_B**, downstream of the series diode. It is a **shunt across the external
LED connection**, not a third series component. This reduces negative connector
voltage while preserving the one-way core path. It does not regulate forward
pulse current or protect reversed flying leads; the latter is now an accepted
installation risk. The diodes/placement are selected, but the actual RF,
recovery/ringing and claimed transient performance still need qualification.
The previous 40-part circuit is not imposed as a prerequisite.

[ASSEMBLY: Placement And Polarity](ASSEMBLY.md#placement-and-polarity) and
[SMA controls](ASSEMBLY.md#indicator-sma-and-resistor-assembly) own the exact
origins, terminal mappings, SMA lands and straight cathode links;
preserve its [Physical Guardrails](ASSEMBLY.md#physical-guardrails). No added
vias or folded branches are introduced, and SMT resistors have **no insertion
holes or axial standoff**. TE body containment does not establish exact
land-pattern equivalence: the [retained alternative](ASSEMBLY.md#2512-smt-resistors)
requires supplier placement/stencil/solder acceptance under W4. The
[dated drawing correction](DFM_EVIDENCE.md#te-3521-body-and-lands-fit) is not
supplier approval. Earlier folded-route and axial options are history, not
pending choices.

### SMT AC Conversion

**Approved construction, 2026-09-14, updated for 1.2.1-dev westward placement;
physical qualification remains held.** GDT_AC uses origin **(123.70,122.50)**,
with pad 1 on A at **(123.70,120.50)** and pad 2 on C at **(123.70,124.50)**.
Its **F.Cu-only, 3.20 mm-wide** stubs at X=123.70 run
from A **Y=114.88 to 120.00** and C **Y=130.12 to 125.00**, retaining **1.80 mm
between connected copper**, not merely a land-to-land gap. The old AC pad pair's
two **1.40 mm PTHs and their A/C interlayer links are removed**; dedicated rail
stitches, J_IN and the core-side earth-GDT PTH links remain. The new A/C stubs
are single-layer paths, not dual-layer copper credited by the old pad links.

The **3.20 mm F.Cu B rail's centreline endpoint is X=115.00**. The rear B
segment remains at **Y=122.50, X=106.00..131.00**, widened to **exactly 6.00 mm,
not 6.40 mm**, retaining its own GDT_B_E input PTH at X=131.00 through the rear
route. The existing B-return stem at X=135.50 actually left **2.10 mm**, not
**>=3.00 mm**. The full-copper review identified the necessary minimal right shift to
**X=136.50**, giving **3.10 mm stem clearance** and a source-geometry minimum
of **3.02 mm between all rear A/B/C copper**; global core/EARTH minimum remains
**3.25 mm**. These nominal geometry values are not finished-etch guarantees or
insulation ratings. The subsequent user-approved westward change moves AB/BC
and their stubs, AC and its takeoffs, and the nine rail vias to the
[controlled coordinates](ASSEMBLY.md#physical-guardrails). All **14 vias** remain
at their original sizes; five EARTH vias, rear copper, mounts, other components,
circuit connections, A/C main rails, EARTH and indicator routing are unchanged
by that relocation. See
[DESIGN_BOUNDS](DESIGN_BOUNDS.md#ac-conversion-copper-screen) for the exact
6.00 mm metal-area/resistance tradeoff and interlayer-current limitations.

There is **no formed AC air gap**. The adopted SMT body-height envelope is
**5.21 mm before solder seating allowance**. Rear B copper passes beneath the
**whole AC pad/body projection**, separated from front copper by the nominal
**1.440 mm FR-4 core**, not qualified insulation. The westward relocation raises
the unlike-net inter-GDT pad minimum from **0.80 to 3.20 mm** and AC-to-B_E
pad gap from **1.321790 to 3.260515 mm**. Each SMT tube still has **2.80 mm between
its own lands and 1.80 mm between connected copper**; facing AB/BC B pads share
one net and retain their 2.42 mm gap. This is not a blanket 3 mm front-layer
minimum. Larger inter-device gaps address the identified geometry, not verified
flashover immunity. Actual transient, contamination, solder/placement, process
and environmental effects remain to qualify; mask and gel do not establish
dielectric withstand. [ASSEMBLY](ASSEMBLY.md#physical-guardrails)
and [DFM_EVIDENCE](DFM_EVIDENCE.md#westward-clearance-evidence) own the physical drawing,
lands, seating and process acceptance; this record assigns no new board rating
or guaranteed sharing through other GDTs. Rear B widening does not qualify
resistor heat rejection, OneGel or continuous TEST.

### Selected SMT Resistors

At nominal source-end current, the existing resistor dissipates about **0.50 W**,
versus roughly **0.03-0.05 W per LED** for illustrative forward drops. The two
resistors are the principal normal heat sources inside the box. Changing 2.2k
from 1 W to 2 W does **not** remove the approximately 1 W total nominal heat.
A larger permitted temperature, different mounting or more copper can explain
a higher rating without making the body cooler.

Current TE ratings, engineering assumptions, unknown test conditions and loss
screens are maintained in [DESIGN_BOUNDS](DESIGN_BOUNDS.md#thermal-screens),
not inferred from the preceding PS12/HP12/PR02 selections. Those selections and
the other investigated options below remain **historical**, not substitutes,
a combined BOM or evidence qualifying the unpopulated Yageo variant:

| Exact candidate | Relevant rating / practical limit |
| :--- | :--- |
| **Historical: Uni-Royal PS122WF2201T4E / C2793873** | PS12 / 2512 SMT, 2.2k, 1%, 2 W at 70 C ambient, linear derating to zero at 155 C; +/-100 ppm/C with 25 C reference [S16]. Family working/overload/dielectric maxima 500/1000/500 V; RCWV and five-second overload 66.3325/165.8312 V. |
| **Historical, superseded: Uni-Royal HP122WF2201T4E** | HP12 / 2512 SMT, **2.2k, 1%, 2 W at 70 C ambient**, linear derating to zero at 155 C. Used **+/-100 ppm/C with 25 C reference**, not the historical website's 75 ppm/C. Family working voltage was limited to 66.3325 V at nominal 2.2k/2 W; five-second overload was 165.8312 V, not an impulse rating [S15]. No HP12 hot-spot/K/W parameter or proven cooler result was assigned. |
| **Historical, retired: Vishay PR02000202201FA100** | Copper-lead PR02, 2.2k, 1%, 2 W P70, +/-250 ppm/K. Its 15.24 pitch / 1.40 holes, 0.83 maximum lead, >=1 mm body standoff, 220 C hot-spot limit and typical mounted 75 K/W belonged to the previous axial assembly. None applies to 2512 SMT. |
| **Historical, unselected: TT PWC2512-2K2FI** | 2.2k, 1%, +/-100 ppm/K, body envelope 6.8 x 3.4 x 0.8 mm. **2 W at 70 C requires 500 mm^2 copper per termination**; the 100 mm^2-per-termination arrangement is **1.5 W**, not 2 W. Those package-specific copper conditions are not 3521 data. |
| **Historical, unselected: Vishay CRCW25122K20FKEGHP** | 2.2k, 1%, +/-100 ppm/K. **1.5 W at 70 C ambient**, or **2 W at 105 C terminal-part temperature**, not ambient. Body envelope 6.5 x 3.3 x 0.7 mm; reflow lands 1.25 x 3.35 each with 5.00 inner gap. Not the selected package or its heat-flow model. |

The smaller TE upper-power screen than the historical PR02 case follows only
from the changed TCR/reference resistance envelope, not a modeled cooling
benefit. Section 3 retains the required continuous-duty/source and measured
OneGel interface controls; catalogue tables are not that qualification.

Historical option sources from the earlier focused resistor investigation, 2026-09-07:
[Vishay 28729, 08-Jul-2025](https://www.vishay.com/docs/28729/pr010203.pdf),
[TT PWC, 07.26](https://www.ttelectronics.com/TTElectronics/media/ProductFiles/Resistors/Datasheets/PWC.pdf),
[Vishay 20043, 17-Mar-2026](https://www.vishay.com/docs/20043/crcwhpe3.pdf).
The active TE prototype source is **S18, 9-1773463-5 Rev G, 02/2025**;
S15/S16 preserve the superseded HP12/PS12 reviews, and S19 confirms the
Yageo identity without assigning it this model.
These are source/option records, not procurement allocation, a passed physical
test or permission to transfer another resistor family's thermal or overload data.
