markshuttle/dogfence-pcb/pcb/LED_PROTECTION_RESEARCH.md

# LED Protection Research

**Research began 2026-09-07 from checkpoint 97e202d; current hardware 1.2.1-dev. Research, not circuit selection or release approval.**

Added in **ad282e3**, this note includes later findings and dated corrections.
Candidate calculations retain their original parts/circuits/assumptions;
technical errata are allowed, not routine order rewrites. Purchase history is
in [MATERIALS](../MATERIALS.md#resistor-procurement-and-history) (**repository-only**,
not shipped with these notes). The study uses one TEST source and a disconnected
spare, never series, parallel, separate-channel or opposite-end supplies.

**Original handoff, superseded:** section 11 rejects L1's PWC pulse-resistor
string. L2 removes the regulator-current overshoot problem, but TVS2700 exceeds
its recommended normal input range and can exceed its DC absolute limit after
a post-resistor fault. **Neither circuit is selected**; these are negative
findings, not a completed design awaiting field qualification alone.

**Historical implementation after ad282e3:** the **16-part PR02/BYG23T hybrid**
used two 2 W axial resistors, two SMA series diodes and two SMA negative shunts,
not L1/L2. The shunts do not guarantee forward-pulse limiting or instantaneous
<=5 V clamping. Installation-polarity LED damage and direct-strike rebuilding
are accepted, not all routine/nearby transient damage. **Continuous-safe TEST
remains required. Energized cattle fencing is prohibited near the entire
boundary, stations and hub**; the old close-parallel exposure is withdrawn.

**2026-09-11 applicability correction:** the prototype [BOM](BOM.csv) now uses
**TE Connectivity 35212K2FT / C4129105 2512 SMT**. The unpopulated **Yageo
SR2512FK-7W2K2L / C876850** needs independent part/model/process/thermal review
and controlled source updates; TE results do not qualify it. [ELECTRICAL](ELECTRICAL.md#9-simplified-indicator-direction)
records the selected circuit. [DESIGN_BOUNDS](DESIGN_BOUNDS.md#evidence-and-inputs)
records TE **9-1773463-5 Rev G, 02/2025**: the **25 C reference / -30..125 C
linear screen are engineering assumptions**, not TE TCR test conditions.
Catalogue-rating transfer from TE's four-layer reference to this two-layer board
is unverified, not proof of failure; the [alternative lands](ASSEMBLY.md#2512-smt-resistors)
still need placement/stencil/solder acceptance. **PR02 thermal/standoff and PS12
five-second overload/pulse data do not qualify TE or Yageo.**

**C4/C5/W3/W1/W4 remain open**, deferred only for Gate P files, not closed.
No investigated circuit is a prototype-file prerequisite. [Artifact controls](ASSEMBLY.md#prototype-artifacts)
retain supplier/qualification holds and source-hash requirements; the historical
execution records below are not fresh artifact verification.

## 1. Initial L1 Investigation

The initial active development circuit investigated was:
**pulse impedance and a protected input, a floating LT3092 current source, then
ballasted precision shunts and a separate negative clamp at the LED connector**.
The current setting is about **16.18 mA**, not 20 mA nominal. The output shunt
can accommodate **20 mA total without exceeding either reference's 15 mA
operating ceiling**. Its calculated steady positive limit is **4.3584 V**.

This removes LED minimum forward voltage from the current-safety calculation.
It also establishes a useful output-voltage passband without first demanding
the entire SG LED I/V distribution. It does **not** establish an instantaneous
20 mA ceiling merely by quoting the current source's DC accuracy.

**No complete, datasheet-only, pulse-safe selection is supported yet.** The
specific remaining design gaps are current-source recovery/overshoot, shunt
turn-on overshoot, interpretation of below-knee reference loading, the selected
pulse resistor's applicable curves, and the actual excitation of the 200 mm
LED harness. A concrete test envelope and quantitative closure conditions are
below. Unknown LED minimum Vf is not the reason for this disposition.

## 2. Candidate Netlist

Candidate **L1**, repeated independently for X=A and X=C. `B` means `WIRE_B`,
not earth or a new ground plane. Intermediate nodes are private to that rung.
References below are research names, not assignments in the existing schematic.

```text
WIRE_X -- RPx1 -- RPx2 -- RPx3 -- RPx4 -- DPx(A->K) -- Px
Px -- UCLx.IN
UCLx.OUT -- RIx -- LED_X_POS -- J_LED_X.1 -- external LED anode
UCLx.SET -- RSx -- LED_X_POS
external LED cathode -- J_LED_X.2 -- WIRE_B

Px -- TVPx.IN;             TVPx.GND -- B
Px -- CPx -- B

LED_X_POS -- RBx1 -- Kx1 -- UZx1.cathode
LED_X_POS -- RBx2 -- Kx2 -- UZx2.cathode
UZx1.anode = UZx1.pin3 = B
UZx2.anode = UZx2.pin3 = B

LED_X_POS -- TVNx.IN;      TVNx.GND -- B
```

| Per-Rung Reference | Quantity | Exact Candidate MPN | Connection / Purpose |
| :--- | ---: | :--- | :--- |
| RPx1..4 | 4 | TT Electronics `PWC2512-390RFI` | Four 390 ohm, 1%, 100 ppm/K pulse-withstanding resistors in series: 1560 ohm nominal. Pulse-envelope approval remains outstanding. |
| DPx | 1 | Diotec `BYG23T` | Anode toward resistor string, cathode to Px; 1300 V repetitive blocking. Not a claim that the original 1N4007G has sufficient repetitive margin. |
| TVPx | 1 | TI `TVS1800DRVR` | IN pins 4/5/6 to Px; GND pins 1/2/3 and exposed pad to B. Primary low-voltage input protection, not an LED-voltage clamp. |
| CPx | 1 | KEMET `C1210C106K5RACTU` | 10 uF, 50 V, X7R, 10%, nonpolar, Px-to-B. Effective capacitance at bias/temperature is a design gap; nominal 10 uF is not its minimum. |
| UCLx | 1 | ADI `LT3092IST#PBF` | SOT-223: IN pin 3 to Px, SET pin 1 to RSx, OUT pin 2 and tab to RIx. Use I grade for the specified industrial junction range. |
| RSx | 1 | Vishay `TNPW080551K1BEEA` | 51.1 kohm, 0.1%, 25 ppm/K, SET-to-LED_X_POS. |
| RIx | 1 | Vishay `TNPW080531R6BEEA` | 31.6 ohm, 0.1%, 25 ppm/K, OUT-to-LED_X_POS. |
| UZx1, UZx2 | 2 | TI `LM4050BEM3-4.1/NOPB` | Each: cathode pin 1 to its own Kx node, anode pin 2 to B, pin 3 tied to B as recommended for high EMI. B-grade extended-temperature 4.096 V reference. |
| RBx1, RBx2 | 2 | Vishay `TNPW080522R0BEEA` | Separate 22.0 ohm, 0.1%, 25 ppm/K ballast resistors. Do not parallel the references without them. |
| TVNx | 1 | TI `TVS0500DRVR` | IN pins 4/5/6 to LED_X_POS; GND pins 1/2/3 and pad to B. Used for its specified forward/negative clamp, **not** its approximately 9 V positive surge clamp. |

This version has 15 components per rung, replacing the existing two. If all ten
other electrical parts were retained, the board would have 40 electrical parts,
not the then-current 14. No allocation, JLCPCB code, footprint fit, or placement is
approved. The resistor and capacitor codes follow their manufacturers' ordering
tables; supplier allocation and exact product specification sheets still need
confirmation. The `LM4050BEM3` orderable is listed in TI's addendum; do not invent
an A-grade extended-temperature 4.1 V order code from a family description.

All shunts and the input capacitor are **after DPx**. Moving TVPx ahead of DPx
creates a B-to-A/C forward-diode path through RP and can defeat clean-cut
isolation. There is no A-to-C auxiliary supply or shared reference node. Keep
the existing connector polarity and two distinct local LED terminal mappings.

## 3. Current Source Bounds

ADI LT3092 revision D, 08/20, pp. 4, 9-16 [R1]:

- ISET = 9.8..10.2 uA over the specified full-temperature, 2..40 V,
  1..200 mA conditions; initial 25 C accuracy is 1%.
- OUT-to-SET offset is +/-4 mV over temperature at the listed 2 V/1 mA
  condition. Load-related offset change is specified up to 2 mV; line-related
  offset change is 0.010 mV/V at the specified condition. Not every row carries
  the full-temperature marker.
- Dropout maxima are 1.45 V at 10 mA and 1.65 V at 200 mA. The external RI
  drop is additional. At 6.2 mA, nominal RI contributes 0.196 V, not 0.511 V.
- All quiescent/drive current goes to OUT; there is no separate B-referenced
  milliamp bias load. SET contributes an additional approximately 10 uA.
- IN withstands +/-40 V relative to SET/OUT. Reverse current is less than
  1 mA in the protection description; this is not sufficiently small to replace
  the one-way input rectifier for cut isolation.
- No input/output capacitors are generally required, but ADI explicitly
  requires in-situ stability checking with complex loads and long wires.

The correct two-terminal programming equation includes SET current:

```text
Iterminal = (ISET * RS + VOS) / RI + ISET
Inominal = 10 uA * 51100 / 31.6 + 10 uA = 16.180886 mA
```

A transparent **engineering screen**, allowing each programming resistor a
total +/-1% envelope and |VOS,total| <=6.4 mV, gives:

```text
Ilow  = (9.8 uA * 51100 * 0.99 - 6.4 mV) / (31.6 * 1.01) + 9.8 uA
      = 15.342931 mA
Ihigh = (10.2 uA * 51100 * 1.01 + 6.4 mV) / (31.6 * 0.99) + 10.2 uA
      = 17.042299 mA
```

The 6.4 mV screen rounds 4 mV offset + 2 mV load change + 0.38 mV line change
upward. **It is not a newly guaranteed all-corner 17.043 mA rating.** Confirm
the combined line/load/temperature envelope and dropout transition, rather
than silently extending the 25 C rows. The +/-1% resistor allowance includes
design margin for TCR/process/drift, not a lifetime qualification. TNPW's
general-operation rating, low dissipation, cleanliness and process limits
remain applicable [R6].

ADI also calls out leakage at the 10 uA SET node: 10 nA already creates a 0.1%
reference error. Keep the SET circuit clean and compact; the suggested guard
potential is OUT, on both PCB sides, not B or EARTH. Potting is not proof of
acceptable surface leakage or a reason to omit this check.

Use **18 mA as the development stage ceiling**, leaving 2 mA to the user's
20 mA limit. Obtain a supported dynamic bound or qualification sufficient for
the declared envelope before calling that ceiling enforced. LT3092's internal
200 mA-class fault current limit is **not** the programmed 16 mA protection.
Its typical line-transient and turn-on plots are not maximum overshoot data.

No LED minimum Vf occurs in these equations. A shorted LED is included in the
intended current limit. A simple pass transistor/0.65 V VBE limiter or a
20 mA-nominal CCR does not offer an equivalent maximum-current bound.

## 4. Precision Shunt Bounds

TI LM4050-N, SNOS455H, March 2025, section 5.7 [R2], for the chosen BEM3 part:

| Parameter | Specified Limit / Condition |
| :--- | :--- |
| Reference voltage | 4.096 V; +/-29 mV at 100 uA over -40..125 C |
| Current-related voltage change | <=1.2 mV from IRMIN to 1 mA; <=10 mV from 1 to 15 mA, over temperature |
| Minimum operating current | <=78 uA over the extended temperature range |
| Maximum operating current | 15 mA; 20 mA is absolute maximum, not a usable shunt rating |
| Stability | Internally compensated; no output capacitor needed; tolerates capacitive loads |

Adding the magnitudes of both current-change limits conservatively:

```text
Vz_lo = 4.096 - 0.029 - 0.0012 - 0.010 = 4.0558 V
Vz_hi = 4.096 + 0.029 + 0.0012 + 0.010 = 4.1362 V
RB_lo = 22 * 0.99 = 21.78 ohm
RB_hi = 22 * 1.01 = 22.22 ohm

Vconnector_hi <= Vz_hi + Itotal * RB_hi / 2
              = 4.33618 V at 18 mA
              = 4.35840 V at 20 mA

Ione_hi <= (Itotal * RB_hi + Vz_hi - Vz_lo) / (RB_lo + RB_hi)
         = 11.927273 mA at 20 mA total < 15 mA
```

These are steady-state bounds with functioning references and the stated
resistor/temperature envelope. They do not assume equal current sharing.
At small total currents only one reference may regulate; that cannot increase
the positive voltage above the high-current bound. Self-heating must keep each
junction in range; the current-change tests are pulsed. Approximately 50 mW in
the more heavily loaded reference would produce about 14 C rise using TI's
287 C/W test-board metric, not a measured potted-board thermal resistance.

**Low-loading argument, with its exact limitation:** a fixed reference must
already be near 4.096 V at 100 uA. For its normal monotone, non-latching shunt
characteristic, a terminal voltage <=4.0 V therefore implies less than 100 uA
per reference. The pair's conservative DC diversion budget is **0.20 mA**,
about 3.3% of 6 mA. This uses a specified operating point, not a typical zener
leakage curve and not the TL431 `REF=0` off-current specification. However,
TI does not explicitly tabulate maximum current throughout the below-knee
0..4.0 V region. Treat monotonic/no-latch operation there as a stated circuit
assumption; obtain vendor confirmation of **I <=100 uA for 0..4.0 V over
-40..125 C**, or qualify/review that assumption before claiming it guaranteed.
Do not relabel IRMIN as a literal datasheet leakage specification.

Thus the design offers a **0..4.0 V normal LED-voltage passband**. Exact SG Vf
is needed only to establish where the purchased LEDs lie within that passband
and their brightness/headroom, not to bound forward current or the positive
reversed-lead voltage. The existing 3.3 V family screen has substantial voltage
separation from the reference knee.

For negative connector voltage, TVS0500 section 7.6 [R3] specifies **VF <=0.65 V
at 1 mA over operating free-air temperature**, unlike the retrieved ordinary
diodes' 25 C-only forward maxima. BYG23T's <=50 uA reverse leakage at 125 C and
rated voltage is below that current in steady supply reversal. Use the usual
monotone forward-diode characteristic for lower current. TVS0500 leakage at
5 V is <=220 nA at 85 C and <=755 nA at 105 C. These are specified temperature
points, not an invented 125 C maximum. Its 155 pF capacitance is typical.

TVS0500 alone is **not** sufficient: its positive breakdown is 7.5..8.4 V at
1 mA and its positive surge clamp can reach 9.5 V. The two precision references
are what protect a reversed external LED under positive supply.

## 5. Normal Current And Cuts

Use 3.3 V as an explicit LED **brightness/headroom screen**, not as an inferred
full-temperature APEM guarantee. With RP allowed +/-4%, RI allowed +/-1%,
BYG23T screened at 1.9 V, and a conservative 1.65 V current-source dropout:

The RP +/-4% is an allowed design/measurement envelope for these screens, not
a manufacturer guarantee combining every tolerance, aging and pulse-history
extreme. Extend the envelope and recalculate if the accepted process requires it.

```text
RP = 1497.6..1622.4 ohm
RI_max = 31.916 ohm
Vlocal_needed_for_6mA_LED
  >= 3.3 + 1.9 + 1.65 + (0.006 + 0.00020022) * (1622.4 + 31.916)
  ~= 17.1071 V, before upstream capacitor/TVP leakage and wiring allowances.
```

Use **17.2 V local X-to-B** as a preliminary useful-light interface target under
those assumptions, not as a guaranteed field voltage. The 1.65 V dropout use
at lower current assumes monotone dropout behavior; the guaranteed table
points and the diode's 25 C forward-voltage condition must remain visible.
At 35.5..36 V near the source there is enough series headroom for the current
setting; allowing 0..0.20022 mA diversion gives about **15.14..17.04 mA**.

Read-only calculations with the existing persistent model used RP+RI =1591.6
ohm and a combined constant semiconductor drop of 6.85 V. They deliberately
omit current clipping, new shunt loading, input-capacitor dynamics and leakage:

| Uniform 41-Station Screen | Total Source Current | Far-End Branch Current | Unclipped Source-End Branch Current |
| :--- | ---: | ---: | ---: |
| 27.6 ohm per 4 km core | 0.930308 A | 8.069182 mA | 18.314903 mA |
| 40 ohm per 4 km core | 0.813526 A | 6.132720 mA | 18.314903 mA |

Subtracting 0.20022 mA for the reference pair and negative-clamp allowance
from the latter gives **5.9325 mA**,
not a proven 6 mA minimum. Current clipping changes cable drops, and independent
LED/resistor corners must be modeled; uniform high Vf is not the worst possible
loading of a single high-Vf far-end LED. The smaller resistance is a credible
headroom recovery, **not** a completed full-network guarantee. A lower verified
low-current rectifier drop, lower cable resistance, or revised resistor/current
settings can close this small uniform-case deficit. Do not lower RP blindly:
more upstream load and inrush can counteract the apparent benefit.

With DPx blocking every new core-to-B path, the ideal one-way clean-cut topology
is preserved: A-only leaves C on after the cut, C-only leaves A on, and B/any
two/all-three cuts leave both off after the cut. No End A/C strap or second B
return is added. Real reverse leakage and stored energy require an OFF-state
and settling check, not the old solver's 1 uA classifier as an optical limit.
The new input capacitors must discharge after a cut; a brief decay is different
from a permanent backfeed. Aggregate hot leakage must not create a misleading
visible indication on a floating island.

## 6. Conducted Pulse Envelope

Proposed **development envelope**, to be accepted by the electrical/GDT owners
and the laboratory, not claimed to describe every lightning or cattle pulse:

- Absolute differential voltage at the rung's WIRE_X/B pads <=1200 V, including
  DC bias and local overshoot; both polarities; powered and unpowered.
- Exercise 1.2/50 us voltage pulses with declared generator impedance, initially
  42 ohm, and a faster front up to 1 kV/us. Independently exercise the fast
  collapse/reversal caused by GDT firing, not only the generator's rising edge.
- For the high-voltage portion, screen energy conservatively as no more than
  1200 V for 100 us: integral(V^2 dt) <=144 V^2 s. Specify the subsequent tail
  separately; an arbitrarily long 40 V tail is not inside that energy budget.
- Initial component-development repetition: five pulses per polarity per
  selected corner, at least 60 s apart. This is neither lifetime nor repetitive
  cattle-fence qualification. Add the actual repetitive envelope separately.
- The circuit-level test excludes direct injection into the LED harness until
  its separate coupling test is defined. Excluding it is not field approval.

For RP_min =1497.6 ohm, conservatively ignoring all diode/clamp drops:

```text
Ipre_peak <= 1200 / 1497.6 = 0.801282 A
E_RP_total <= 1200^2 * 100 us / 1497.6 = 0.096154 J
P_RP_each_peak <= (0.801282)^2 * (390 * 1.04) < 261 W
E_RP_each <= 0.0261 J
V_RP_each <= 0.801282 * (390 * 1.04) < 326 V
```

The individual figures intentionally combine adverse independent corners.
PWC2512 has a 500 V limiting-element voltage, but **that does not approve a
261 W pulse**. TT publishes separate 1.2/50, 10/700, single-pulse and repetitive
curves [R7]. They were not visually read in the initial investigation. **Section
11 now resolves them and rejects this L1 resistor string for the stated 100 us
rectangular screen.** For any other use, confirm the
390 ohm curve, initial hot temperature, repetition and allowed drift against
the numbers above before selecting these parts. The original MBE0414's 1 W
rating is not such evidence. Four parts reduce voltage and heat concentration;
they do not magically multiply an unverified pulse rating.

TVS1800 [R4] specifies 24.7 V maximum for the stated 35 A 8/20 us test with
18 V prebias at 125 C; 23/23.4 V maxima at 24/40 A and 27 C; VBR=19.5..23.8 V
at 1 mA. Its 10/1000 us absolute current rating is 6 A. The candidate's <0.81 A
screen is much smaller, but waveform equivalence and startup at this lower
current are still to be established. Set a **30 V measured input-node ceiling**
including layout overshoot; the LT3092 then has margin to its 40 V limit even
with a slightly negative LED output. No 24.7 V universal clamp is inferred
for every pulse shape or duration from one test entry.

With Px <=30 V and raw negative input >=-1200 V, DP reverse stress is <=1230 V,
below its 1300 V repetitive rating. The original 1000 V 1N4007G is not adequate
for this declared envelope; its 1200 V nonrepetitive entry is not a substitute.
BYG23T's 5 mJ avalanche figure is not used as permission to exceed 1300 V [R5].

Require CP **effective capacitance >=4.7 uF at the actual bias, temperature and
age** if relying on the following first-order filter screen:

```text
dVP/dt <= 0.801282 A / 4.7 uF = 0.1705 V/us
RP_min * CP_min = 7.0387 ms
```

This is a lumped charging bound, not a parasitic feedthrough or current-loop
overshoot guarantee. KEMET [R8] provides nominal tolerance, +/-15% X7R
temperature behavior, insulation and process tests, but not that particular
biased/aged 4.7 uF minimum in the retrieved family table. Obtain the part-specific
bound. The 50 V rating does not establish retained capacitance.

Bulk capacitance stays **before the current source**. No capacitor is put
across the limiter, and no deliberate output reservoir is connected directly
across the external LED. Both arrangements can bypass the programmed current
limit. Even small unavoidable shunt/connector capacitances and the harness
still need transient evaluation. Wiring remains power-off/discharged; hot
reconnection of a charged output is not included in a nominal DC limit.

## 7. Source, Thermal And RF Consequences

The study uses one LRS-75-36, 36 V / 2.1 A /75.6 W, with adjustable
output, hiccup overload and higher OVP thresholds [R9]. The disconnected spare
does not make a 4.2 A fence source. For one active source, a provisional 18 mA
per rung ceiling gives <=1.476 A and <=59.63 W at 40.4 V, before other loads.

Input-capacitor startup is different: an ideal voltage step into all 82 empty
capacitors through RP_min gives **1.971 A at 36 V**, or **2.212 A /89.37 W at
40.4 V**. The latter exceeds one LRS-75's ratings. The published typical
30 ms PSU rise time is not an enforced slew limit. A controlled source window
and/or supported startup behavior are necessary; the spare PSU is not
an assumed remedy. No timer is proposed for normal TEST.

Normal source-end heat is still roughly a watt per board. At 18 mA, RP_max
would dissipate 0.526 W per rung (about 0.132 W per resistor). Lower RP moves
some heat into LT3092 rather than removing it. Its tab is OUT, **not B or
EARTH**. At 40.4 V, RP_min and zero LED/rectifier drop, the simple
`I*(40.4-I*RP_min)` screen is 0.2673 W at the low current-setting corner;
its maximum over all currents is 0.2725 W. This upper screen includes RI/SET
network dissipation, so does not undercount LT3092's share. Thermal layout must
support it and keep junctions <=125 C in normal operation. Neither ADI's
four-layer thermal examples nor a resistor's catalog P70 establish gel/solar
temperatures on this board.

TVS1800's DC breakdown-current absolute maximum is only 18 mA. It is not a
continuous-power substitute for a failed-open current source: calculate and
qualify that fault separately. With normal current-source/shunt operation,
the 40.4 V screen places Px below about 18 V, but low-end setting/resistor
corners and leakage need checking. The input-capacitor short and current-source
open/short faults must be included in the eventual fault/thermal analysis.

RF loading is not zero just because a current source is used. CP bypasses its
high AC impedance through the input rectifier. In an ideal symmetric RUN
connection, A/B/C have equal local potentials; real imbalance does not.
The additional input path is approximately
`RP + Z(DP) + Z(CP || TVP)`, in parallel with the downstream branch. If DP
conducts, a crude lumped worst-case conductance for 82 branches is
`82/1497.6 = 54.75 mS`; if DP is off, junction capacitance dominates. This is
not a transmission-line prediction or a sum of 82 directly connected 10 uF
capacitors. TVS0500 and LM4050 also add connector capacitance. The Flat-Clamp
parts can draw transient current below standoff on fast edges; TI cautions
about repetitive edges above approximately 0.7 V/us at high temperature.
Measure the actual carrier, differential/common-mode amplitudes, impedance,
receiver field and unintended LED light with the final station population.

A guaranteed GDT holdover candidate would help powered recovery, **not** prove
LED pulse safety or bound the pre-spark front. Its impulse maximum, test slope,
extinction network and failure behavior must be supplied by the other owner.
If its guaranteed impulse level exceeds this envelope, revise the rectifier,
RP, TVP and spacing before integration. Added branch clamps/energy storage can
change the network used to assess holdover; give their load model to that owner.
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
